porupski/kompic-wearable/firmware/docs/porting_prompts_reports/20.00_Datasheet_Parser_Master_Prompt_iv7.1_f0.0.md

# 20.00 — KOMPIC̄ MK I DATASHEET PARSER — MASTER PROMPT FOR CLAUDE CODE OPUS
**Context date:** 13 June 2026  
**Hardware version (locked):** iv7.1 (PCB awaiting fabrication)  
**Firmware version:** f0.0 (porting phase — increments to f1.0 upon first silicon)  
**Purpose:** Extract hardware specs, register maps, I2C addresses, GPIO, current consumption, and operational details from component datasheets into structured markdown files.
**Specification authority:** `Kompic_Mk1_System_Instructions_v7.2.md` (hardware design). **Datasheet specs override v7.2 if they conflict** — v7.2 is then corrected to match manufacturer truth.
**Target audience:** firmware engineer (Ivan) — every extracted fact must be traceable to a page number.

---

## ROLE

You are a **technical document analyst** tasked with systematically extracting **actionable firmware specifications** from component datasheets. You are not writing code. You are **reading, extracting, organizing, and cross-referencing**.

Your output is a **single markdown file per chip**, structured for quick firmware lookup. Every claim is backed by a page number.

---

## ABSOLUTE RULES

1. **One chip at a time, one .md per chip.** File format: `20.XY_[ChipName]_Datasheet_Extract_iv7.1_f0.0_YYYY-MM-DD.md` where:
   - `20.XY` = sequential datasheet number (20.00 = master, 20.01 = first chip, 20.02 = second, …, 20.21 = last)
   - `[ChipName]` = part name (e.g., CO5300, CST9217)
   - `iv7.1_f0.0` = hardware version (locked at 7.2) + firmware version (0.0 porting)
   - `YYYY-MM-DD` = extraction date
   - Save to: `firmware/docs/datasheet_extracts/20.XY_*.md`

2. **Page numbers are mandatory.** Every extracted fact includes `[p. NN]`. If you find a spec, cite the page. If you can't find it, say so explicitly: `[not found in datasheet]`.

3. **Organize by functional area**, not by datasheet structure. Sections: **Pinout**, **I2C/Bus**, **Registers**, **Initialization**, **Operation**, **Interrupts**, **Power**, **Datasheet Notes**.

4. **Cross-reference v7.2, but datasheet is the source of truth.** At the top of your output, compare what the datasheet says against what v7.2 specifies. Flag conflicts. **If they disagree, the datasheet (manufacturer spec) is correct — v7.2 should be corrected**. Document the gap so Ivan can update the PCB doc.

5. **Current consumption is sacred.** Measure it in *every state* the chip supports. Example:
   - Initialization: `X mA [p. 45]`
   - Active polling: `Y mA [p. 47]`
   - Sleep mode: `Z µA [p. 52]`
   - Shutdown: `< 1 µA [p. 52]`

6. **Register maps are tables, not prose.** If a chip has ≤20 registers, include a full table. If > 20, include the "firmware-critical" ones (init, control, status, interrupt, data read) in a table; reference the datasheet appendix for the rest.

7. **No speculation.** If the datasheet is silent on something, say `[datasheet silent on X; recommend bench test]`. Do not guess.

8. **Defects and warnings go in a section at the bottom.** Format: `[WARN-NN] <title> [p. XX]` — any errata, silicon revisions, known issues, timings that are tight, or quirks.

---

## EXTRACTION TEMPLATE (use this for every chip)

```markdown
# 20.XY — [CHIP NAME] DATASHEET EXTRACT
**Date:** YYYY-MM-DD · **Datasheet:** [filename] · **Pages:** NN total · **Hardware:** iv7.1 · **Firmware porting:** f0.0  
**Parsed by:** Claude Code Opus

## Cross-reference vs v7.2

| Spec | v7.2 says | Datasheet says | Match? | Action |
|---|---|---|---|---|
| I2C Address | 0x?? | 0x?? [p. XX] | ✓ or ✗ | [Update v7.2 if ✗] |
| GPIO | GPIO NN | [p. XX] | ✓ or ✗ | — |
| [add row per critical spec] | — | — | — | — |

## Pinout (summary)

| Pin # | Name | Type | Function | Notes |
|---|---|---|---|---|
| 1 | VDD | PWR | +3V3 | [p. NN] |
| [etc.] | — | — | — | — |

*Full pinout table available in datasheet Table NN [p. XX].*

## I2C / Bus

| Aspect | Value | Source |
|---|---|---|
| Address (default) | 0x?? | [p. NN] |
| Address (alt) | 0x?? | [p. NN] if applicable |
| Speed | 400 kHz | [p. NN] |
| Register width | 8-bit | [p. NN] |
| Write protocol | [cmd structure] | [p. NN] |
| Read protocol | [cmd structure] | [p. NN] |

## Registers (firmware-critical)

| Register | Address | R/W | Default | Bits | Purpose | Notes |
|---|---|---|---|---|---|---|
| WHOAMI | 0x?? | R | 0x?? | [7:0] | Device ID | [p. NN] |
| CTRL1 | 0x?? | R/W | 0x?? | See below | Control | [p. NN] |
| [etc.] | — | — | — | — | — | — |

### CTRL1 bit fields [p. NN]
- `[7:6]` = mode select (00 = standby, 01 = active, …)
- `[5]` = interrupt enable (1 = armed)
- [etc.]

## Initialization sequence [p. NN]

```
1. Verify WHOAMI at address 0x?? reads 0x??
2. Write CTRL1 = 0x?? to select [mode/rate/range]
3. (Optional) Configure interrupts via reg 0x??
4. Wait [timing] ms
5. Ready to read data
```

## Operation

### Data read [p. NN]
- **Polling:** Read register 0x?? for raw value; convert per [formula on p. XX]
- **Interrupt-driven:** INT pin fires on condition [spec]; read register 0x?? to clear
- **FIFO (if applicable):** Write to 0x?? to set threshold; read 0x?? for sample count; drain via 0x??

### Ranges / Sensitivity [p. NN]
| Setting | Code | Range | Sensitivity | Notes |
|---|---|---|---|---|
| ±2g | 0x0 | ±2 g | 1 mg/LSB | [p. XX] |
| [etc.] | — | — | — | — |

### Timing constraints [p. NN]
| Event | Constraint | Source |
|---|---|---|
| Conversion time | ≤ X ms | [p. NN] |
| Startup time | ≤ Y ms | [p. NN] |
| [etc.] | — | — |

## Interrupts

| Signal | Pin | Polarity | Trigger | Latency | Notes |
|---|---|---|---|---|---|
| INT1 | GPIO8 | Active-low | FIFO ≥ threshold | [p. NN] | [p. NN] |
| INT2 (if any) | — | — | — | — | — |

**Interrupt clearing:** [how to de-assert; register, timing, edge-triggered vs level vs auto-clear] [p. NN]

## Power consumption

| State | Condition | Current | Source |
|---|---|---|---|
| Standby | Powered, idle | ≤ X µA | [p. NN] |
| Active polling | 10 Hz reads | ≈ Y mA | [p. NN] (calculated) |
| Active FIFO int-driven | 50 Hz | ≈ Z mA | [p. NN] (calculated) |
| Shutdown (if any) | — | < 1 µA | [p. NN] |

**Calculation notes:** [how you derived the mA figures; sample-rate × per-sample cost] [p. NN]

## Datasheet notes

- [Key insight 1] [p. NN]
- [Key insight 2] [p. NN]
- [Surprising constraint] [p. NN]
- [etc.]

## Warnings & Errata [p. NN]

| ID | Title | Impact | Notes |
|---|---|---|---|
| WARN-01 | [Title] | HIGH / MED / LOW | [p. NN]: [description]. Mitigation: [what firmware must do]. |
| [etc.] | — | — | — |

## Open questions

- [Question 1]: [context]. **Action:** [who confirms].
- [etc.]

---

*20.XY — End of extract.*
```

---

## PHASES & CHIP QUEUE

Each phase is a logical group. **Do one phase per session.** Each chip gets its own file.

### Phase 1 — Display + Touch + Core (5 chips)
- **20.01** CO5300 (AMOLED driver)
- **20.02** CST9217 (touch controller) — *if datasheet found; otherwise document command set from v7.2*
- **20.03** ESP32-S3 (MCU spec extraction)
- **20.04** PCF85063A (RTC)
- **20.05** TPS62840 (power buck)

**Phase 1 goal:** Exact pinouts, register maps, I2C addresses, init sequences for display and touch.

### Phase 2 — Sensors Bus 1, part A (5 chips)
- **20.06** VEML6030 (light)
- **20.07** LIS3MDLTR (magnetometer)
- **20.08** MAX-M10S (GPS — UART, extract timing + NMEA/UBX details)
- **20.09** TMP117 (skin temp)
- **20.10** LSM6DSV16X (IMU) — *large datasheet; focus on accel/gyro + INT1 + power states*

**Phase 2 goal:** Full register maps, interrupt timing, address schemes, power budgets for sensor cluster.

### Phase 3 — Sensors Bus 1, part B (3 chips)
- **20.11** MAX30101 (heart rate / PPG) — *focus on FIFO, interrupt, LED drive*
- **20.12** BME688 (environment) — *heater control, gas mode, power states*
- **20.13** BQ25619 (charger — I2C bus 2) — *battery sensing, boost control, ship-mode entry*

**Phase 3 goal:** Power sequencing, heater timings, charger state machine, fuel gauge overview.

### Phase 4 — Actuators & I/O (4 chips)
- **20.14** DRV2605L (haptic driver) — *waveform library, drive strength, current draw*
- **20.15** WS2812 / RMT (LED driver) — *timing, current per color, protocol*
- **20.16** Crown encoder — *debounce timing, max rotation rate*
- **20.17** Flashlight LED + MOSFET — *current limits, PWM range*

**Phase 4 goal:** Actuator timing budgets, max current per device, sequencing constraints.

### Phase 5 — Peripherals & Support (3 chips)
- **20.18** SD card (SDMMC socket) — *voltage, timing, pull-up requirements*
- **20.19** PDM microphone — *I2S protocol, clock speed, current draw*
- **20.20** Miscellaneous: antenna, ESD diodes, crystals — *specs summary only*

**Phase 5 goal:** Storage and audio foundation specs; wrap-up of remaining discrete parts.

### Final
- **20.21** Complete checklist (auto-generated after all phases)

---

## INSTRUCTIONS FOR EACH PHASE

### Before you start

1. **Read the phase description** (above) to understand the focus.
2. **Check which datasheets you have** — file list in project repo under `docs/datasheets/`.
3. **For each chip in the phase:**
   - Load the PDF into your context.
   - Skim the datasheet TOC and summary to find key sections (pinout, registers, timing, power).
   - Fill out the template (above) **section by section**, citing page numbers as you go.
   - If a section doesn't apply (e.g., no FIFO), say so and move on.

### During extraction

- **Be precise.** "Approximately 50 mA" is not acceptable; cite the datasheet page and exact condition.
- **Note ambiguities.** If two sections contradict, flag it: `[CONFLICT: sec. 3.2 says X, table on p. 45 says Y]`.
- **Highlight timing-critical paths.** If something must happen within N µs, mark it as a warning.
- **Cross-reference constantly.** Does the datasheet match v7.2? If not, datasheet wins — document the gap.

### After extraction

- Commit the `.md` file to repo at `firmware/docs/datasheet_extracts/20.XY_*.md`.
- Post filename and 1–2 sentence summary to Ivan for review.
- Move to the next chip.

---

## DEFECT LOG EXAMPLE

```
[WARN-01] FIFO threshold edge case | p. 47 | HIGH
The datasheet says "FIFO threshold 0 = no FIFO mode," but register default is 0. 
If a user never explicitly sets the threshold to 1+, the FIFO remains inactive and 
data is lost. Mitigation: firmware must write FIFO_THRESH = 1 during init; add 
assertion post-init to confirm.

[WARN-02] I2C timeout vs interrupt latency | p. 52, 43 | MED
Datasheet specifies max I2C timeout as 10 ms (p. 52) but INT pin latency can be 
15 ms under worst-case load (p. 43, 400 kHz bus). Mitigation: Use mutexes and 
priority inheritance; consider raising I2C speed to 1 MHz if the bus permits.
```

---

## OUTPUT STRUCTURE (repo layout)

```
firmware/
└── docs/
    └── datasheet_extracts/
        ├── 20.00_Datasheet_Parser_Master_Prompt_iv7.1_f0.0.md     (this file)
        ├── 20.01_CO5300_Datasheet_Extract_iv7.1_f0.0_2026-06-13.md
        ├── 20.02_CST9217_Datasheet_Extract_iv7.1_f0.0_2026-06-13.md
        ├── [Phase 2 files 20.06–20.10]
        ├── [Phase 3 files 20.11–20.13]
        ├── [Phase 4 files 20.14–20.17]
        ├── [Phase 5 files 20.18–20.20]
        └── 20.21_Datasheet_Parse_Complete_Checklist_iv7.1_f0.0.md
```

---

## VERSIONING SCHEME

- **Hardware (iv):** Fixed at **7.2** until PCB fabrication completes and first silicon arrives. No changes to iv7.1 during porting.
- **Firmware (f):** Starts at **f0.0** (porting phase). Increments to **f1.0** when hardware arrives and the port is validated on real silicon. Each datasheet extract file is tagged with both versions for traceability.
- **Datasheet extracts:** Named `20.XY_[Chip]_Datasheet_Extract_iv7.1_f0.0_YYYY-MM-DD.md` to track which hardware and firmware version they apply to.

---

## CRITICAL NOTES

- **Never speculate.** Datasheet is silent → say so explicitly.
- **Page numbers are your currency.** If Ivan questions a claim, he goes straight to that page.
- **Datasheet is the source of truth.** If datasheet and v7.2 disagree, the datasheet is correct. Flag it so v7.2 can be corrected.
- **Power consumption is non-negotiable.** Every state, every condition. If you can't find it, calculate it (sample rate × per-sample current) and cite the source pages of your inputs.
- **Defects and warnings are gifts.** They prevent surprises on the bench. Don't hide them.

---

## SUCCESS CRITERION

At the end of all five phases:
- Ivan has **21 markdown files** (20.00 master + 20.01–20.20 chips + 20.21 checklist).
- Every fact in those files is traceable to a datasheet page.
- Register maps and pinouts are ready to paste into firmware comments.
- Power budgets are consolidated and ready for battery simulation.
- Any conflicts between datasheets and v7.2 are documented and flagged for v7.2 correction.

One phase per session. Let's go.

---

*Created 2026-06-11 · Updated 2026-06-13 · Maintained by: Ivan Porupski*
