porupski/kompic-wearable/firmware/docs/porting_prompts_reports/20.14-20.17_KICKOFF_PHASE4_Actuators_IO.md

# 20.14–20.17 KICKOFF — PHASE 4: ACTUATORS & I/O
**Date:** 13 June 2026  
**Hardware version:** iv7.1 (locked)  
**Firmware version:** f0.0 (porting)  
**Target chips:**
- **20.14** DRV2605L (haptic driver)
- **20.15** WS2812B (RGB LED, RMT protocol)
- **20.16** Crown encoder (mechanical specs)
- **20.17** Flashlight LED + MOSFET gate

**Effort estimate:** 1 session (3–4 hours)

---

## PHASE 4 GOAL

Extract **actuator and I/O driver specifications** — protocol timings, current limits, and sequencing constraints. Focus on haptic waveforms, LED color transitions, current per device, 5V boost rail arbitration.

---

## WHAT YOU'LL PARSE

### 20.14 — DRV2605L Haptic Driver
- I2C address (0x5A on **Bus 2** per v7.2)
- Register map (MODE, GO, WAVESEQ, FEEDBACK_CTRL, STATUS)
- Waveform library (click, buzz, alert; amplitude, duration)
- Drive strength control (voltage output range)
- Mode select (internal trigger, PWM, I2C)
- Current consumption (idle, active waveform, sweep)
- ERM vs. LRA (datasheet assumes ERM; confirm compatibility with ELV1411A LRA)
- Thermal limits

### 20.15 — WS2812B RGB LED (RMT Protocol)
- Protocol (1-wire timing; 0 vs. 1 bit encoding)
- Color format (GRB order? RGB order?)
- Update rate (refresh constraint)
- Power consumption (per color, per LED)
- RMT peripheral requirements (GPIO42, timing accuracy)
- Current limits (max per LED; 5V rail constraint)

### 20.16 — Crown Encoder
- Contact bounce time (typical debounce window)
- A/B quadrature phase relationship
- Maximum rotation rate (RPM → Hz conversion)
- Electrical specs (contact resistance, voltage limits)
- PCNT peripheral for debounce-free counting

### 20.17 — Flashlight LED + Gate MOSFET
**LED specs:**
- Forward voltage (3.2V typical for white)
- Maximum forward current
- Power dissipation (@rated current, de-rated with temperature)

**MOSFET (BSS138W):**
- Gate threshold voltage (Vgs(th))
- Rds(on) at 3.3V gate
- Maximum drain current (continuous)
- Thermal resistance (θja)

---

## 5V BOOST ARBITRATION SUMMARY

Add a section comparing all 5V consumers:
- **MAX30101 LEDs:** ~200 mA during active HR measurement
- **WS2812:** ~60 mA max (all white at full brightness)
- **Flashlight:** ~200–500 mA depending on brightness
- **BQ25619 boost capacity:** 1A total
- **Conflict:** If all three demand 5V simultaneously, boost can't supply. Firmware must sequence or limit.

---

## EXTRACTION CHECKLIST

- [ ] Protocol or electrical specs extracted
- [ ] Current draw (all modes, all brightness levels for LED/flashlight)
- [ ] Timing constraints (debounce, settling, update rate)
- [ ] Power limits (max continuous current, thermal limits)
- [ ] Warnings (contact bounce, current surges, thermal throttling)
- [ ] Page numbers on every claim

---

## OUTPUT FILENAMES

- `20.14_DRV2605L_Datasheet_Extract_iv7.1_f0.0_2026-06-13.md`
- `20.15_WS2812_Datasheet_Extract_iv7.1_f0.0_2026-06-13.md`
- `20.16_Encoder_Datasheet_Extract_iv7.1_f0.0_2026-06-13.md`
- `20.17_Flashlight_LED_MOSFET_Extract_iv7.1_f0.0_2026-06-13.md`

---

## SUCCESS FOR PHASE 4

By the end:
- Four .md files, each ≤ 6 pages
- 5V rail budget clearly defined
- Haptic waveform library enumerated
- Encoder debounce time confirmed
- Current arbitration strategy outlined

**Next phase:** Peripherals (files 20.18–20.20); SD, mic, miscellaneous.

---

*Created 2026-06-11 · Updated 2026-06-13 · Maintained by: Ivan Porupski*
