porupski/kompic-wearable/firmware/docs/porting_prompts_reports/20.18-20.20_KICKOFF_PHASE5_Peripherals_Misc.md

# 20.18–20.20 KICKOFF — PHASE 5: PERIPHERALS & MISC
**Date:** 13 June 2026  
**Hardware version:** iv7.1 (locked)  
**Firmware version:** f0.0 (porting)  
**Target chips:**
- **20.18** SD card (SDMMC interface)
- **20.19** PDM microphone (I2S protocol)
- **20.20** Miscellaneous (antenna, ESD diodes, crystals)

**Final deliverable:**
- **20.21** Datasheet Parse Complete Checklist

**Effort estimate:** 1 session (2–3 hours)

---

## PHASE 5 GOAL

Close out the datasheet extraction with **peripherals and miscellaneous** components. These have lower firmware criticality but are essential for correctness: storage (SD), audio input (PDM mic), RF (antennas), and protection (ESD diodes, crystal specs).

By the end of Phase 5, every datasheet is parsed, all extracted specs are organized, and the firmware team has a complete hardware reference library.

---

## WHAT YOU'LL PARSE

### 20.18 — SD Card (SDMMC Interface)
**File:** Generic SDMMC connector spec or LCSC reference  
**Focus:**
- Electrical specs (voltage, current limits)
- Timing constraints (setup/hold for GPIO38/39/40)
- Pull-up requirements (v7.2 says 10kΩ typical)
- Card detection (CD pin polarity if used; v7.2 says "verify on bench")
- Hot-swap safe (can ESP32 handle card removal during operation?)
- Speed grades (SD High-Speed, SDXC)

### 20.19 — PDM Microphone
**File:** Generic PDM MEMS spec or LCSC reference  
**Focus:**
- I2S protocol (CLK on GPIO47, DATA on GPIO48 per v7.2)
- Clock frequency (typical 1–4 MHz)
- Sampling rates supported (16, 32, 48 kHz typical)
- Bit depth (output resolution)
- Sensitivity (dBV/Pa or similar)
- Signal-to-noise ratio (SNR)
- Frequency response (20 Hz–20 kHz)
- Power consumption (active, standby)
- Acoustic overload point (SPL limit)

### 20.20 — Miscellaneous (Reference Specs Only)
**Collated specs for:**
- **BLE antenna (Johanson 2450AT18A):** Impedance, gain, pattern, tuning network values (per v7.2)
- **GPS antenna (ceramic patch):** Frequency (L1 1.575 GHz), gain, impedance
- **RTC crystal (32.768 kHz):** Load capacitance, ESR, tolerance, temperature range
- **ESD diode arrays (ESDALCL5, TPD2E001):** Clamping voltage, leakage current, response time
- **Schottky diodes (1N4148):** Forward voltage, leakage, reverse recovery time (for GPS/RTC backup isolation)

---

## EXTRACTION CHECKLIST

- [ ] Electrical specs (voltage, current, impedance)
- [ ] Timing constraints (if protocol-based)
- [ ] Interface pins and signal names
- [ ] Power consumption (if applicable)
- [ ] Warnings or known issues
- [ ] Page numbers on every claim

---

## OUTPUT FILENAMES (Phase 5 extracts)

- `20.18_SDCard_SDMMC_Extract_iv7.1_f0.0_2026-06-13.md`
- `20.19_PDM_Microphone_Extract_iv7.1_f0.0_2026-06-13.md`
- `20.20_Miscellaneous_Passives_Reference_iv7.1_f0.0_2026-06-13.md`

---

## FINAL CHECKLIST — ALL PHASES COMPLETE

**File:** `20.21_Datasheet_Parse_Complete_Checklist_iv7.1_f0.0_2026-06-13.md`

After Phase 5, create a summary file:

| # | Chip | File | Status | Notes |
|---|---|---|---|---|
| 20.01 | CO5300 | 20.01_CO5300_... | ✓ | Display pipeline, QSPI, sleep/wake |
| 20.02 | CST9217 | 20.02_CST9217_... | ✓ or [fallback] | Touch protocol (v7.2 if no datasheet) |
| 20.03 | ESP32-S3 | 20.03_ESP32-S3_... | ✓ | GPIO, I2C, SPI, sleep, boot straps |
| 20.04 | PCF85063A | 20.04_PCF85063A_... | ✓ | RTC, time/date, alarms, backup |
| 20.05 | TPS62840 | 20.05_TPS62840_... | ✓ | 3.2V buck, soft-start, efficiency |
| 20.06 | VEML6030 | 20.06_VEML6030_... | ✓ | Light sensor, auto-ranging |
| 20.07 | LIS3MDLTR | 20.07_LIS3MDLTR_... | ✓ | Magnetometer, hard-iron cal, LRA offset |
| 20.08 | MAX-M10S | 20.08_MAX-M10S_... | ✓ | GPS, NMEA/UBX, 1PPS, time-before-fix |
| 20.09 | TMP117 | 20.09_TMP117_... | ✓ | Skin temperature, precision, thresholds |
| 20.10 | LSM6DSV16X | 20.10_LSM6DSV16X_... | ✓ | IMU, accel/gyro, INT1, raise-to-wake |
| 20.11 | MAX30101 | 20.11_MAX30101_... | ✓ | Heart rate, PPG, FIFO, INT, LEDs |
| 20.12 | BME688 | 20.12_BME688_... | ✓ | Environment, gas heater, bus contention |
| 20.13 | BQ25619 | 20.13_BQ25619_... | ✓ | Charger, fuel gauge, boost, ship-mode |
| 20.14 | DRV2605L | 20.14_DRV2605L_... | ✓ | Haptics, waveforms, I2C bus 2 |
| 20.15 | WS2812 | 20.15_WS2812_... | ✓ | Status LED, RMT protocol, color |
| 20.16 | Encoder | 20.16_Encoder_... | ✓ | Crown input, debounce, PCNT |
| 20.17 | Flashlight | 20.17_Flashlight_... | ✓ | LED, MOSFET gate, PWM brightness |
| 20.18 | SD Card | 20.18_SDCard_... | ✓ | SDMMC interface, mount on demand |
| 20.19 | PDM Mic | 20.19_PDM_Mic_... | ✓ | I2S, audio capture, SNR |
| 20.20 | Miscellaneous | 20.20_Miscellaneous_... | ✓ | Antenna, crystals, ESD diodes |

---

## CONSOLIDATION TASKS FOR 20.21

In the final checklist, also include:
- **Total power budget** (sum of all sensors at typical duty cycle)
- **I2C bus utilization** (Bus 1 vs. Bus 2 worst-case load)
- **5V boost rail consumer list** (total max draw vs. 1A capacity)
- **RTC GPIO wake sources** (GPIO 6, 7, 8, 15, 16, 21 confirmed)
- **Cross-v7.2 conflicts** (any specs where datasheet overrides v7.2, list them for doc correction)

---

## SUCCESS FOR PHASE 5 (AND FINAL COMPLETION)

By the end:
- 21 datasheet extract .md files checked into `firmware/docs/datasheet_extracts/`
- Each file ≤ 8 pages, traceable to source pages
- Cross-references to v7.2 complete (conflicts flagged for doc correction)
- Power budgets consolidated (input for battery simulation)
- Register maps ready to paste into firmware comments
- Defects and warnings enumerated (input for firmware design)
- Final checklist confirms all specs captured

**Total time:** ~5 sessions (1 per phase) ≈ 25–30 hours focused extraction.

**Output:** A complete hardware reference library, organized and indexed for the firmware team.

---

*Created 2026-06-11 · Updated 2026-06-13 · Maintained by: Ivan Porupski*
