porupski/kompic-wearable/firmware/docs/datasheet_extracts/20.18_SDCard_SDMMC_Extract_iv7.1_f0.0_2026-06-19.md

# 20.18 — SD CARD / SDMMC SOCKET DATASHEET EXTRACT
**Date:** 2026-06-19 · **Datasheet:** SDMMC Socket LCSC.pdf (Shenzhen Shouhan Technology, "TF PUSH", Rev. A/0, 8 pp.) · **Hardware:** iv7.1 · **Firmware porting:** f0.0
**Parsed by:** Claude Code Sonnet 4.6

---

## Cross-reference vs v7.2

| Topic | iv7.1 / v7.2 assumption | Datasheet finding | Action required |
|---|---|---|---|
| Supply voltage | 3.2V TPS62840 rail | Datasheet silent on VDD spec; passive connector. | Confirmed compatible — 3.2V within SD spec 2.7–3.6V tolerance [SD spec] |
| Card detect (CD) pin | Present; polarity "verify on bench" | Pin 2 = CD/DAT3 (shared). Separate dedicated CD switch pin visible in mechanical drawing ("Cd"). Polarity NOT stated. | MUST verify on bench — polarity unresolved |
| 1-bit SDMMC mode | Only DAT0 connected (GPIO40) | Socket has all 8 signal pins. Physically supports 4-bit. 1-bit is a firmware/GPIO choice, not a socket limitation. | No action — socket capable; 1-bit chosen by design |
| Pull-ups on SD lines | 10 kΩ typical (v7.2) | Datasheet silent on pull-up values | Consistent with SD spec [SD spec] |
| Insertion cycles | Not stated in v7.2 | 5000 cycles rated [p. 5, Table I item 5] | No conflict |
| Contact resistance | Not stated in v7.2 | 40 mΩ max initial; 100 mΩ max after 5000 cycles [p. 5, Table I] | Acceptable |
| Operating temperature | Not stated | −25°C to +85°C storage; −55°C to +85°C thermal shock rated [p. 6, p. 8, Table I] | Within wearable range |

---

## Connector mechanical specs

| Parameter | Value | Source |
|---|---|---|
| Product type | MicroSD (TF) push-push (push-in / push-out eject) | [p. 1] |
| Total signal contacts | 8 (DAT0–DAT3, CMD, CLK, VDD, VSS) | [p. 1, pin table] |
| Card detect contact | 1 separate CD pin ("Cd" in PCB layout) | [p. 1, drawing] |
| Total pins inc. CD | 9 electrical contacts | [p. 1] |
| Contact pitch | 1.10 mm; total 8-contact span 8.80 mm | [p. 1, PCB layout] |
| Overall body width | 14.75 mm | [p. 1] |
| Overall body height above PCB | ~3.40 mm | [p. 1, side view] |
| Eject travel | ~0.92 mm push-out stroke | [p. 1] |
| PCB mounting hole diameter | 2 × ⌀0.80 mm (±0.10) | [p. 1] |
| PCB mounting hole pitch | 8.00 mm centre-to-centre | [p. 1] |
| Mounting type | SMT pads + 2 through-hole anchor posts | [p. 1] |
| Multimedia card compatible | Yes | [p. 1, Notes item 3] |
| Housing material | High-temp thermoplastic, UL94V-0 | [p. 1, Notes item 1] |
| Contact plating | Gold over Nickel (contact area); Tin over Nickel (solder area) | [p. 1, Notes item 2] |
| RoHS | Yes | [p. 2, §3.3] |

**Pin table** [p. 1]: Pin 1=DAT2, Pin 2=CD/DAT3, Pin 3=CMD, Pin 4=VDD, Pin 5=CLK, Pin 6=VSS, Pin 7=DAT0, Pin 8=DAT1.

---

## Electrical characteristics

| Parameter | Value | Conditions | Source |
|---|---|---|---|
| Contact resistance (initial) | 40 mΩ max | 10 mA, 20 mV OC; MIL-STD-202F | [p. 5, Table I item 2] |
| Contact resistance (after 5000 cycles) | 100 mΩ max | Post-durability | [p. 5, Table I item 5] |
| Contact resistance (after thermal shock) | 100 mΩ max | −55°C to +85°C, 5 cycles | [p. 6, Table I item 9] |
| Contact resistance (after humidity) | 100 mΩ max | 40°C, 90–95% RH, 96 h | [p. 6, Table I item 10] |
| Insulation resistance (initial) | 1000 MΩ min | 500 V DC ±10% | [p. 5, Table I item 3] |
| Insulation resistance (after humidity) | 100 MΩ min | Post-humidity | [p. 6, Table I item 10] |
| Dielectric strength | 500 V AC, 1 min | Leakage ≤ 1.0 mA | [p. 5, Table I item 4] |
| Rated current per contact | 0.3 A | Temp rise ≤30°C; UL498 | [p. 5, Table I item 6] |
| Insertion cycles | 5000 | Contact resistance ≤100 mΩ post-test | [p. 5, Table I item 5] |
| Vibration | No discontinuity >1 µs | 10–55 Hz, 1.5 mm, 2 h/axis; MIL-STD-202 Method 201 | [p. 5, Table I item 7] |
| Shock | No discontinuity >1 µs | 490 m/s², 3 axes; MIL-STD-202 Method 213 | [p. 5, Table I item 8] |
| Operating temperature | −25°C to +85°C | Storage; thermal shock rated to −55°C | [p. 3, §3.8; p. 6] |
| Contact capacitance | Not stated | — | [not found in datasheet] |

---

## Card Detect (CD) pin

**Physical presence:** Yes — dedicated "Cd" pin in PCB layout, separate from the 8 signal contacts. Pin 2 is dual-function CD/DAT3. [p. 1, drawing]

**Active polarity when card inserted:** **NOT stated in this datasheet.** No logic level, pull direction, or switch type described.

**Convention (unverified):** Most push-push TF sockets use a normally-closed switch that opens when a card is inserted (Cd goes HIGH with pull-up when absent, LOW when inserted). This is an unconfirmed assumption for this specific part — **bench verification is mandatory before writing card-detect firmware.**

**Firmware impact:** In iv7.1, SD_Cd is listed as "test pad only" (not on a GPIO). Hot-swap detection is therefore not implemented. This is acceptable for v1 if the card is treated as fixed storage during operation.

---

## SDMMC protocol context (1-bit mode)

### Why 1-bit was chosen
GPIO budget is exhausted. Only GPIO38 (CLK), GPIO39 (CMD), GPIO40 (DAT0) are available. DAT1–DAT3 not assigned. 4-bit mode is physically impossible without a hardware spin. The socket supports 4-bit mechanically. [iv7.1 pinout; p. 1 pin table]

### Pull-up requirements [SD spec]

| Signal | Pull-up required | Recommended value | Kompic v7.2 | Status |
|---|---|---|---|---|
| SD_CLK (GPIO38) | Optional | 10–100 kΩ | 10 kΩ | Consistent |
| SD_CMD (GPIO39) | Mandatory | 10–100 kΩ | 10 kΩ | Correct |
| SD_DAT0 (GPIO40) | Mandatory | 10–100 kΩ | 10 kΩ | Correct |
| SD_DAT1–DAT3 | Required if used | 10–100 kΩ | Not connected | Card has internal weak pull-ups on unused DAT lines in 1-bit mode |

Pull-ups must be to SD VDD rail (3.2V in Kompic).

### Maximum clock frequency (1-bit mode) [SD spec]

| Speed mode | Max clock | Bus width | Notes |
|---|---|---|---|
| Default Speed (DS) | 25 MHz | 1-bit or 4-bit | Mandatory baseline; all SD cards support |
| High Speed (HS) | 50 MHz | 1-bit or 4-bit | Requires CMD6 negotiation; most modern microSD support |
| UHS-I (SDR50/104/DDR50) | 100–208 MHz | 4-bit only | Not available in 1-bit mode |

**Practical limit for Kompic:** 50 MHz (HS 1-bit). Note: 10 kΩ pull-up × ~20 pF line capacitance → RC ≈ 200 ns — too slow for 50 MHz HS recovery. See WARN-02.

### Initialization sequence (1-bit SDMMC, ESP-IDF) [SD spec / ESP-IDF]

```
1. Apply VDD; CMD and DAT0 held high by pull-ups.
2. Wait ≥1 ms for card power-up.
3. Send ≥74 clock cycles with CMD high (card initialization clocks).
4. CMD0 (GO_IDLE_STATE) — reset card.
5. CMD8 (SEND_IF_COND) — detect SD v2.0+ vs legacy.
6. ACMD41 (SD_SEND_OP_COND) — repeat until card not busy.
7. CMD2 (ALL_SEND_CID), CMD3 (SEND_RELATIVE_ADDR) — get RCA.
8. CMD7 (SELECT_CARD) — transition to Transfer state.
9. ACMD6 (SET_BUS_WIDTH) with arg 0b00 — FORCE 1-bit mode.
   DO NOT send 0b10 (4-bit) — DAT1–DAT3 not wired.
10. (Optional) CMD6 (SWITCH_FUNC) — negotiate High Speed 50 MHz.

ESP-IDF: set sdmmc_slot_config_t.width = 1 and
SDMMC_HOST_FLAG_1BIT to enforce 1-bit throughout.
```

### Hot-swap safety
Push-push mechanism allows physical removal at any time. Card removal during active I/O corrupts the filesystem (FAT/FAT32 has no journaling). Firmware must either unmount before removal or detect the CD transition and flush/unmount cleanly. With CD currently on a test pad (no GPIO), hot-swap safety is by user convention only: do not remove the card while the device is logging. [SD spec / ESP-IDF]

---

## Power consumption

| Item | Value | Notes |
|---|---|---|
| Connector idle | 0 mW (passive) | No active electronics |
| Pull-up quiescent (CMD + DAT0) | ~0.64 mA | 2 × (3.2V / 10kΩ); lines high at idle |
| Pull-up quiescent (+ CLK, if populated) | ~0.96 mA | 3 × 10kΩ pull-ups |
| SD card active | 20–100 mA | Card-dependent [SD spec] |
| SD card idle (STANDBY state) | 0.5–2 mA | Card-dependent [SD spec] |
| SD card sleep | ~0.1 mA | After CMD5 or power-cycle [SD spec] |
| Contact current rating | 0.3 A max per contact | Temp rise ≤30°C [p. 5, Table I item 6] |

---

## Datasheet notes

- [p. 1] Multimedia card (MMC) compatible — connector accepts both microSD and MMC form factors.
- [p. 3, §3.8] Storage: −25°C to +85°C, ≤80% RH, non-corrosive. Re-qualify after >6 months storage.
- [p. 5, Table I item 5] 5000 insertion cycles — adequate for personal device (daily swap = 13+ years).
- [p. 5, Table I item 6] 0.3 A per contact rated — SD card current peaks well below this; no thermal concern.
- [p. 5–6, Table I items 7–8] Vibration/shock: MIL-STD-202, 490 m/s² — robust for a wrist-worn device.
- [p. 8, Table III] Pb-free reflow: peak 255°C, max 60 s above 217°C. Compatible with JLCPCB Pb-free profile.
- [p. 2, §1] Product described as "T-FLASH 外焊" (TF card, external anchor solder style).
- [p. 2, §2] Test references: MIL-STD-1344A, MIL-STD-202F, EIA364, IEC-512-3.

---

## Warnings & Errata

| ID | Title | Impact | Notes |
|---|---|---|---|
| W-01 | CD pin polarity undetermined | MEDIUM | Datasheet gives no information on CD switch logic level. Open Issue #4 in iv7.1 remains unresolved. Do not write card-detect firmware until bench-confirmed. |
| W-02 | 10 kΩ pull-ups too slow for 50 MHz HS mode | HIGH | 10 kΩ × ~20 pF ≈ 200 ns RC — far too slow for 50 MHz CMD recovery. Use Default Speed (25 MHz) with 10 kΩ, or reduce pull-ups to 4.7 kΩ and verify signal integrity at 50 MHz with scope. |
| W-03 | DAT1–DAT3 not connected — must enforce 1-bit in driver | HIGH | If ESP-IDF SDMMC host is initialised without `width = 1`, it will attempt 4-bit via ACMD6 → bus corruption on unwired lines. Always set `sdmmc_slot_config_t.width = 1`. |
| W-04 | No GPIO for CD pin | LOW | CD is a test pad only. Hot-swap detection impossible without hardware change. Treat SD card as fixed storage during operation. |
| W-05 | Hand-soldering risk at 1.10 mm contact pitch | LOW-MED | Inspect under magnification for solder bridges. Gold-over-nickel contacts — do not overheat. |
| W-06 | Contact capacitance not specified | LOW | Datasheet silent. At 25 MHz DS this is unlikely to matter. At 50 MHz HS, verify empirically with scope. |
| W-07 | GPIO38–40 have no RTC wake capability | INFO | SD cannot wake ESP32-S3 from deep sleep — by design, consistent with iv7.1. |

---

## Open questions

1. **CD pin polarity** — LOW or HIGH when card inserted? Measure on bench with multimeter before writing card-detect logic. (iv7.1 Open Issue #4.)
2. **Contact capacitance** — Not in datasheet. Obtain from Shenzhen Shouhan or measure if 50 MHz HS mode is desired.
3. **Pull-up values for HS mode** — Reduce CMD/DAT0 pull-ups from 10 kΩ to 4.7 kΩ or 2.2 kΩ if 50 MHz HS is needed; verify with oscilloscope.
4. **LCSC part number** — Confirm BOM part number matches this drawing's PCB footprint (8.00 mm mounting hole pitch, 1.10 mm contact pitch) before ordering.
5. **Filesystem journaling** — FAT32 has no journaling; hot-swap corruption risk. Consider exFAT (ESP-IDF v5+) or a "safe to remove" UI indicator.
6. **4-bit upgrade path** — For Kompic Mk II with more GPIOs: route DAT1–DAT3 and this socket supports 4-bit 50 MHz (4× throughput). Worth routing in next spin if fast data logging is needed.

---

*20.18 — End of extract.*
