porupski/kompic-wearable/firmware/docs/datasheet_extracts/20.19_PDM_Microphone_Extract_iv7.1_f0.0_2026-06-19.md

# 20.19 — MSM261DGT003 PDM MICROPHONE DATASHEET EXTRACT
**Date:** 2026-06-19 · **Datasheet:** MSM261DGT003.pdf · **Hardware:** iv7.1 · **Firmware porting:** f0.0
**Parsed by:** Claude Code Sonnet 4.6

---

## Cross-reference vs v7.1

| Topic | iv7.1 assumption | Datasheet reality | Action required |
|---|---|---|---|
| Supply rail | "1.8V rail (MEMS mic VDD)" listed under +1V8 consumers | VDD range 1.6–3.6 V; test conditions at 1.8 V — **1.8V is correct and confirmed** | None — rail assignment confirmed |
| VDD rail label | System Instructions list mic under +1V8 | 1.8V is within 1.6–3.6V range; 1.8V is the datasheet reference condition | Confirmed: power from +1V8 rail |
| PDM protocol | PDM (not I2S) | Confirmed PDM digital output, fourth-order Σ-Δ modulator, ½-cycle PDM data format | Confirmed |
| L/R pin | "likely tied to GND" | JP9 default = GND (left channel = Mic(Low)); DATA asserts on CLK **falling** edge, latches on CLK **rising** edge | Confirmed: JP9 default GND = L channel; firmware/ESP32 must sample on rising edge |
| Mic_CLK GPIO | GPIO47 | CLK input to mic — no constraint from mic side beyond frequency range | Confirmed |
| Mic_Dout GPIO | GPIO48 | DATA output from mic | Confirmed |
| Operating temperature | Not stated in iv7.1 | Not explicitly stated in datasheet for operating range; storage −40 to +100°C; reliability bias tests to +105°C | Operating range not specified — see Open Questions |
| Decoupling | Not called out | 100 nF + 10 µF ceramic as close to VDD as possible [p. 12] | Add to bring-up checklist |

---

## Pinout (summary)

| PIN# | Function | Kompic iv7.1 connection |
|---|---|---|
| 1 | VDD | +1V8 rail |
| 2, 5 | GND | GND |
| 3 | DATA | GPIO48 (Mic_Dout) |
| 4 | CLK | GPIO47 (Mic_CLK) |
| 6 | L/R (SEL) | JP9 default = GND → left channel (Mic(Low)) |

Package is 6-pad LGA. Pins 2 and 5 are both GND; there is no separate pad for a separate power-good or enable — VDD is the only power input. The acoustic port (Ø0.65 mm) is top-ported (top face of the package). [p. 9]

---

## Interface / Protocol

**PDM confirmed — not I2S.** The MSM261DGT003 outputs a 1-bit pulse-density-modulated bitstream using a fourth-order Sigma-Delta (Σ-Δ) modulator. There are no I2S frame-sync (WS/LRCK) or I2S word-clock signals. The only two signal lines are:

- **CLK** — a clock input driven by the host (ESP32). The mic samples and modulates audio continuously at this clock rate.
- **DATA** — a 1-bit open-drain-like PDM output line. The bit density encodes instantaneous amplitude: higher density of 1s = higher sound pressure. Polarity: increasing sound = increasing density of 1s. [p. 3]

**Data format: ½ Cycle PDM.** The DATA line is driven for only one half of each clock cycle (the active half), and goes to High-Z for the other half. This allows two PDM microphones to share a single DATA line (stereo configuration) — one mic drives during the high half, the other during the low half. [p. 3, p. 7]

**L/R pin controls which half-cycle is active:**

| L/R pin | Mic name | Asserts DATA on | Latches DATA on |
|---|---|---|---|
| VDD | Mic(High) | CLK rising edge | CLK falling edge |
| GND | Mic(Low) | CLK falling edge | CLK rising edge |

**Kompic uses L/R = GND (JP9 default)** → Mic(Low) → DATA is asserted on CLK falling edge and the valid data bit is latched (read by host) on the CLK rising edge. [p. 7]

**How ESP32-S3 I2S-PDM-RX mode handles this:**
The ESP32-S3 I2S peripheral has a dedicated PDM RX mode (`I2S_COMM_FORMAT_STAND_PCM_SHORT` with PDM RX enabled via `i2s_pdm_rx_config_t`). In this mode:
- The I2S peripheral generates the CLK output on Mic_CLK (GPIO47) — there is no separate WS line.
- DATA is received on Mic_Dout (GPIO48).
- The peripheral integrates a decimation filter (CIC + IIR) that converts the incoming 1-bit PDM bitstream at the CLK frequency into multi-bit PCM samples at the target audio sample rate.
- The decimation ratio is: **decimation = f_CLK / (f_sample × 2)**. At f_CLK = 3.072 MHz and f_sample = 48 kHz, decimation = 32.
- For L/R = GND (Mic(Low)), the ESP32 PDM RX mode samples on the rising edge, which is correct.
- No MCLK or WS signals are needed or generated in PDM mode.

---

## Electrical characteristics

| Parameter | Symbol | Min | Typ | Max | Units | Conditions | Source |
|---|---|---|---|---|---|---|---|
| Supply voltage | VDD | 1.6 | — | 3.6 | V | — | [p. 3] |
| Absolute max supply | — | −0.3 | — | 4.0 | V | — | [p. 3] |
| Logic input high | VIH | 0.7×VDD | — | 3.6 | V | — | [p. 5] |
| Logic input low | VIL | −0.3 | — | 0.3×VDD | V | — | [p. 5] |
| Logic output high | VOH | VDD − 0.45 | — | — | V | IOUT = 2 mA | [p. 5] |
| Logic output low | VOL | — | — | 0.45 | V | IOUT = 2 mA | [p. 5] |
| Clock duty cycle | — | 40 | — | 60 | % | — | [p. 5] |
| Short circuit current | ISC | 1 | — | 10 | mA | DATA pin grounded | [p. 3] |
| Max output load | CLOAD | — | — | 200 | pF | — | [p. 3] |

**Note on logic levels at 1.8V VDD:**
- VIH min = 0.7 × 1.8 = 1.26 V
- VIL max = 0.3 × 1.8 = 0.54 V
- ESP32-S3 GPIO output high (3.3V domain on R8 per iv7.1) = ~3.0–3.3V → well above VIH. **Mismatch: mic VDD = 1.8V but CLK is driven from the 3.3V GPIO domain (GPIO47 is "3.3V domain on R8").** CLK input to the mic at 3.3V logic levels exceeds VIH max of 3.6V absolute — it is within the absolute maximum (3.6V), but VOH of a 3.3V GPIO can reach 3.3V which is above the mic's VDD. This warrants verification. See Warnings & Errata.

---

## Acoustic performance

| Parameter | Symbol | Min | Typ | Max | Units | Conditions | Source |
|---|---|---|---|---|---|---|---|
| Sensitivity | S | −27 | −26 | −25 | dBFS | 94 dB SPL @ 1 kHz; Standard mode, f_CLK=2.4 MHz | [p. 4] |
| Sensitivity | S | −26 | −25 | −24 | dBFS | 94 dB SPL @ 1 kHz; Low-Power mode, f_CLK=768 kHz | [p. 5] |
| Sensitivity matching | — | — | ±1 | — | dB | Between matched units | [p. 2] |
| SNR (A-weighted) | SNR | — | 64 | — | dB(A) | 20 kHz BW, A-weighted; f_CLK=2.4 MHz | [p. 4] |
| SNR (A-weighted) | SNR | — | 63 | — | dB(A) | A-weighted 20 Hz–8 kHz; f_CLK=768 kHz | [p. 5] |
| Acoustic overload point | AOP | — | 120 | — | dB SPL | 10% THD @ 1 kHz | [p. 4, p. 5] |
| Total harmonic distortion | THD | — | 0.1 | — | % | 94 dB SPL @ 1 kHz | [p. 4, p. 5] |
| PSRR | PSRR | — | 50 | — | dBV/FS | 200 mVpp sinewave @ 1 kHz | [p. 4, p. 5] |
| PSR+Noise | PSR+N | — | −80 | — | dBFS(A) | 100 mVpp square wave @ 217 Hz, A-weighted | [p. 4, p. 5] |
| DC output offset | — | — | 4 | — | % FS | Fullscale = ±100% FS | [p. 3] |
| Directivity | — | — | Omnidirectional | — | — | — | [p. 3] |

**Frequency response (from graph, p. 7):** The typical frequency response measured at 94 dB SPL shows the response is flat (within ~1 dB) from approximately **200 Hz to 5 kHz**, with a gradual roll-off below 200 Hz (low-frequency −3 dB point not explicitly tabulated — estimated from graph at approximately 100–150 Hz) and a slight rise (~1–2 dB) above 5 kHz up to the plotted 10 kHz limit. The datasheet does not provide explicit −3 dB frequency numbers in tabular form; the graph is the only reference. [p. 7]

---

## Timing

### Clock frequency ranges by mode

| Mode | f_CLK min | f_CLK max | VDD | Source |
|---|---|---|---|---|
| Sleep Mode | 0 | 50 kHz | 1.6–3.6 V | [p. 3] |
| Low-Power Mode | 150 kHz | 900 kHz | 1.6–3.6 V | [p. 3] |
| Standard Performance Mode | 1.1 MHz | 4.0 MHz | 1.6–3.6 V | [p. 3] |

Mode is determined **entirely by the CLK frequency applied** — there is no separate mode register or control pin. The mic automatically enters the correct mode based on where f_CLK falls. [p. 6]

### Timing parameters

| Parameter | Symbol | Min | Typ | Max | Units | Conditions | Source |
|---|---|---|---|---|---|---|---|
| Clock rise/fall time | t_EDGE | — | — | 20 | ns | — | [p. 7] |
| Delay time to High-Z | t_DZ | — | — | 40 | ns | DATA → Hi-Z after active half | [p. 7] |
| Delay time to data driven | t_DD | — | — | 50 | ns | DATA valid after CLK edge | [p. 7] |
| Fall-asleep time | — | — | — | 30 | µs | f_CLK ≤ 50 kHz | [p. 3] |
| Wake-up time | — | — | — | 200 | µs | f_CLK ≥ 151 kHz | [p. 3] |
| Power-up time | — | — | 6 | 20 | ms | VDD ≥ V(min) | [p. 3] |
| Mode-change time | — | — | — | 10 | ms | Any mode transition | [p. 3] |

**Sample rate derivation (Standard Performance Mode, f_CLK = 1.1–4.0 MHz):**

The PDM bitstream must be decimated by the host to recover PCM audio. The decimation ratio determines the audio sample rate. The ESP32-S3 I2S-PDM-RX hardware decimation filter typically supports a fixed oversampling ratio of 64×.

| Target sample rate | Required f_CLK (at 64× decimation) | In-range? |
|---|---|---|
| 16 kHz | 64 × 16,000 = 1.024 MHz | Borderline — below 1.1 MHz min for Standard mode; would fall in gap between Low-Power max (900 kHz) and Standard min (1.1 MHz). **Not cleanly achievable.** |
| 44.1 kHz | 64 × 44,100 = 2.8224 MHz | Within Standard mode range (1.1–4.0 MHz). Achievable. |
| 48 kHz | 64 × 48,000 = 3.072 MHz | Within Standard mode range (1.1–4.0 MHz). Achievable. Preferred target. |

Note: the ESP32-S3 PDM RX decimation ratio is configurable (the `dn_sample_mode` field in `i2s_pdm_rx_config_t` can select ×64 or ×128 downsampling). At ×64 and f_CLK = 3.072 MHz, audio output = 48 kHz. The datasheet test condition uses f_CLK = 2.4 MHz (yielding 37.5 kHz equivalent decimated rate at 64×), which is non-standard audio — the 2.4 MHz figure is a characterisation convenience, not a recommended operating point. For Kompic, **f_CLK = 3.072 MHz → 48 kHz PCM** is the target.

For 16 kHz: use ×128 decimation at f_CLK = 2.048 MHz (within Standard mode range) → 16 kHz output. Alternatively, decimate 48 kHz PCM in firmware to 16 kHz.

---

## Power consumption

| State | Condition | Current (typ) | Source |
|---|---|---|---|
| Standard Performance Mode | f_CLK = 2.4 MHz, VDD = 1.8 V | 670 µA | [p. 4] |
| Low-Power Mode | f_CLK = 768 kHz, VDD = 1.8 V | 290 µA | [p. 5] |
| Sleep Mode | f_CLK ≤ 50 kHz, VDD = 1.8 V | 1 µA (typ) | [p. 3] |
| Powered Down | VDD = 0 V | 0 | [p. 6] |

**Sleep mode entry:** reduce f_CLK to ≤ 50 kHz. Fall-asleep time ≤ 30 µs. The mic remains powered (VDD held); only CLK is throttled. [p. 3, p. 6]

**Wake from sleep:** raise f_CLK to ≥ 151 kHz. Wake-up time ≤ 200 µs. [p. 3]

**Power down:** remove VDD entirely (VDD = 0 V). Requires full power-up sequence on re-enable (power-up time 6–20 ms). [p. 6]

**Power budget at 1.8 V (Kompic):**
- Standard mode: 670 µA × 1.8 V = **1.2 mW**
- Low-power mode: 290 µA × 1.8 V = **0.52 mW**
- Sleep: 1 µA × 1.8 V = **1.8 µW**

---

## Package

**LGA (Land Grid Array), metal can**

| Dimension | Value | Tolerance |
|---|---|---|
| Length (L) | 4.00 mm | ±0.10 mm |
| Width (W) | 2.00 mm | ±0.10 mm |
| Height (H) | 1.10 mm | ±0.10 mm |
| Acoustic port diameter | Ø0.65 mm | ±0.05 mm |

[p. 9]

**Orientation:** Top-ported — the acoustic port (Ø0.65 mm hole) is on the top face of the metal can. The PCB must have a matching hole beneath the port if the mic faces down, or the port must be exposed to the sound path. For Kompic, the acoustic port faces up (toward the PTFE sticker / case hole). [p. 2, p. 9]

**Pad layout (bottom view, 6 pads):**

Pads are arranged in two columns of three (left column: 1, 2, 3; right column: 4, 5, 6 — numbered from bottom-left, bottom-right, up):

| Column left | Column right |
|---|---|
| PIN 3 = DATA (top-left) | PIN 4 = CLK (top-right) |
| PIN 2 = GND (mid-left) | PIN 5 = GND (mid-right) |
| PIN 1 = VDD (bot-left) | PIN 6 = L/R (bot-right) |

Pad dimensions (from bottom view drawing): each pad approximately 0.64 mm tall × 0.57 mm wide, with 0.3 mm spacing between pad rows. Corner radius on package body R0.319 mm. [p. 9]

**MSL rating:** Class 1 — no bake required before reflow. [p. 10]

**Maximum reflow cycles:** 3. [p. 10]

**Reflow peak:** 260°C max. [p. 8]

**Tape & reel:** EIA-481 standard, 13-inch reel, 5700 units per reel. [p. 11]

---

## ESP32-S3 I2S-PDM configuration notes

### Driver configuration (ESP-IDF I2S PDM RX)

```c
i2s_chan_config_t chan_cfg = I2S_CHANNEL_DEFAULT_CONFIG(I2S_NUM_0, I2S_ROLE_MASTER);
i2s_new_channel(&chan_cfg, NULL, &rx_handle);

i2s_pdm_rx_config_t pdm_rx_cfg = {
    .clk_cfg = {
        .sample_rate_hz = 48000,
        .clk_src         = I2S_CLK_SRC_DEFAULT,
        .mclk_multiple   = I2S_MCLK_MULTIPLE_256,  // not used in PDM RX
        .dn_sample_mode  = I2S_PDM_DSR_8S,          // x64 decimation
    },
    .slot_cfg = I2S_PDM_RX_SLOT_DEFAULT_CONFIG(I2S_DATA_BIT_WIDTH_16BIT,
                                                I2S_SLOT_MODE_MONO),
    .gpio_cfg = {
        .clk  = GPIO_NUM_47,    // Mic_CLK
        .din  = GPIO_NUM_48,    // Mic_Dout
        .invert_flags = {
            .clk_inv = false,
        },
    },
};
i2s_channel_init_pdm_rx_mode(rx_handle, &pdm_rx_cfg);
```

### CLK frequency calculation

The ESP32-S3 I2S PDM RX clock is derived from the APB or PLL clock and divided down. The CLK output frequency on GPIO47 equals:

**f_CLK = sample_rate × decimation_ratio**

| sample_rate_hz | dn_sample_mode | decimation | f_CLK on GPIO47 | In mic Standard mode range? |
|---|---|---|---|---|
| 48,000 | I2S_PDM_DSR_8S (×64) | 64 | 3.072 MHz | Yes (1.1–4.0 MHz) |
| 16,000 | I2S_PDM_DSR_8S (×64) | 64 | 1.024 MHz | No — below 1.1 MHz min |
| 16,000 | I2S_PDM_DSR_16S (×128) | 128 | 2.048 MHz | Yes (1.1–4.0 MHz) |
| 44,100 | I2S_PDM_DSR_8S (×64) | 64 | 2.8224 MHz | Yes |

**Recommended operating point for Kompic:** 48 kHz, ×64 decimation, f_CLK = 3.072 MHz.

**For 16 kHz capture:** use ×128 decimation (I2S_PDM_DSR_16S) with sample_rate_hz = 16,000 → f_CLK = 2.048 MHz. Do not try 16 kHz with ×64 (f_CLK = 1.024 MHz falls in the dead band between Low-Power max 900 kHz and Standard min 1.1 MHz).

### L/R pin setting for single channel

JP9 is soldered to GND by default → L/R = GND → **Mic(Low)** mode:
- DATA is asserted on the **CLK falling edge**
- The host latches DATA on the **CLK rising edge**

ESP32-S3 PDM RX in `I2S_SLOT_MODE_MONO` with default slot configuration reads the left channel (CLK-falling-edge data), which is exactly what Mic(Low)/L=GND provides. No inversion flags needed.

If a second mic were added (stereo), it would tie L/R to VDD (Mic(High)), share the DATA line, and assert on the rising edge — the two mics share one wire without contention because each drives only during its own half-cycle.

### Decoupling

Place 100 nF ceramic + 10 µF ceramic on VDD as close to PIN 1 as possible. [p. 12] The 1.8V rail is a low-noise LDO output (XC6206) which helps, but the decoupling is still required. The PSRR of 50 dBV/FS at 1 kHz means a 200 mVpp ripple on VDD injects a −50 dBFS signal into the audio — keep the 1.8V rail clean.

### Sleep strategy

To put the mic to sleep without removing power: reduce f_CLK to ≤ 50 kHz (or stop the CLK entirely — 0 Hz is within the sleep range). The mic enters sleep in ≤ 30 µs, drawing 1 µA. Wake by restoring f_CLK ≥ 151 kHz; allow ≤ 200 µs before valid data.

In ESP-IDF: `i2s_channel_disable(rx_handle)` stops the CLK. Re-enable with `i2s_channel_enable(rx_handle)` and discard the first ~200 µs of samples.

---

## Datasheet notes

- [p. 2] Part is described as "omnidirectional, top-ported, PDM digital output MEMS microphone." Package confirmed 4 mm × 2 mm × 1.1 mm metal can LGA.
- [p. 2] Fourth-order Σ-Δ modulator. Features include multiple modes (Sleep, Low-Power, Standard Performance) and sensitivity matching within ±1 dB between units.
- [p. 3] Test conditions for all specifications: 25 ±10°C, 50 ±20% R.H., VDD = 1.8 V, f_CLK = 2.4 MHz, L/R pin grounded, no load.
- [p. 3] Mode is controlled entirely by CLK frequency — no register writes, no I2C, no SPI. Pure hardware state machine.
- [p. 3] DC output offset is 4% FS (typ) — this is a normal PDM characteristic; the decimation filter in the ESP32 will center the output. No action needed in firmware beyond standard I2S-PDM driver.
- [p. 6] State diagram confirms four states: Powered Down (VDD=0), Sleep (f_CLK ≤ 50 kHz), Low-Power (150 kHz ≤ f_CLK ≤ 900 kHz), Standard Performance (1.1 MHz ≤ f_CLK ≤ 4 MHz). Transitions are automatic based on f_CLK and VDD.
- [p. 7] Frequency response graph (94 dB SPL) shows flat response approximately 200 Hz–5 kHz, mild rise above 5 kHz. Low-end rolloff visible below ~200 Hz. Graph x-axis: 100 Hz–10 kHz.
- [p. 7] Timing diagram clarifies the ½-cycle PDM scheme. DATA line goes to High-Z for the half-cycle when this mic is not the active talker. This is key for stereo shared-wire operation.
- [p. 9] Pin 1 marker (triangle/chamfer) is at bottom-left corner of package bottom view.
- [p. 10] MSL Class 1 — no moisture bake required. Max 3 reflow cycles. Do not board wash, brush, or ultrasonically clean after reflow. Do not apply pressure or vacuum to the acoustic port.
- [p. 10] Floor life (out of bag): ≤ 4 weeks at ≤ 75% RH.
- [p. 12] Recommended interface shows ESD protection diodes (PESD5V0F1BL) on CLK and DATA lines, series impedance Z_rf on CLK and DATA, and termination resistor R_term at the processor end. Decoupling: 100 nF + 10 µF on VDD.
- [p. 13] ESD: ±2 kV HBM on I/O pins, ±8 kV LID-GND (lid to ground), ±200 V MM.
- [p. 13] Reliability sensitivity note: sensitivity shall vary within ±3 dB of initial value after all reliability tests (measured after 2 hours conditioning at 25 ±10°C, 50 ±20% RH).

---

## Warnings & Errata

| ID | Title | Impact | Notes |
|---|---|---|---|
| W1 | CLK voltage domain mismatch | MEDIUM | GPIO47 is in the "3.3V domain on R8" (iv7.1 system instructions). The mic VDD = 1.8 V, so CLK VIH max is 3.6 V absolute. A 3.3V GPIO driving CLK to the mic is within the absolute maximum (3.6V), but the margin is only 0.3 V. The datasheet does not explicitly call out a max VIH beyond the absolute maximum supply spec of 4.0 V. However, best practice for a 1.8V-supply digital device is to use a 1.8V logic driver or add a series resistor to form a voltage divider. Verify on bring-up: measure VIH on CLK pin. If the 3.3V GPIO drives CLK without a level translator and the mic operates correctly, it is technically within absolute max ratings — but it is a reliability concern. |
| W2 | 16 kHz at ×64 decimation falls in CLK dead band | HIGH | f_CLK = 1.024 MHz (16 kHz × 64) is below the Standard Performance Mode minimum of 1.1 MHz and above the Low-Power Mode maximum of 900 kHz. The mic would be in an undefined transition zone. Always use ×128 decimation for 16 kHz (f_CLK = 2.048 MHz). |
| W3 | Acoustic port must not be blocked or pressurized | MEDIUM | The PTFE sticker on the case hole is the correct solution. Do not apply vacuum to the port during assembly (e.g., pick-and-place suction must not cover the port hole). The datasheet explicitly prohibits pressure or vacuum on the port. [p. 10] |
| W4 | No explicit operating temperature range stated | LOW | The datasheet gives storage temperature (−40 to +100°C) and reliability test ranges but does not state a separate operating temperature specification. For a wearable, operation from −20 to +60°C is assumed safe based on reliability testing to −40/+105°C, but this is not explicitly confirmed. |
| W5 | Mode-change time 10 ms must be respected | MEDIUM | When transitioning between modes by changing f_CLK (e.g., waking from sleep to standard mode), allow 10 ms before treating DATA as valid. [p. 3] |
| W6 | Power-up time 6–20 ms | MEDIUM | After VDD is applied, valid PDM data is not available for up to 20 ms. The firmware driver must discard the first ≥20 ms of samples after power-on, or after exiting power-down mode. |

---

## Open questions

1. **CLK level translator needed?** The CLK line (GPIO47) is in the 3.3V domain. The mic is a 1.8V device with VIH max equal to the absolute maximum supply of 3.6V (effectively). Is there a series resistor on R8 that already limits the CLK drive voltage, or is the GPIO swinging full 3.3V to the mic CLK pin? Check the schematic: if R8 is a series resistor on the clock line forming a divider with the mic's input impedance, the voltage at the CLK pin may be safe. If R8 is a pull-up resistor (to 3.3V) on the DATA line only, the CLK drive issue remains unmitigated.

2. **Operating temperature range?** The datasheet does not specify a minimum/maximum operating temperature. For a wrist-worn device (skin contact ~20–37°C ambient, but potential exposure to −10°C to +50°C outdoors), is there any guidance from MEMSensing? Not stated in the datasheet. Assume safe based on reliability qualification range.

3. **Frequency response −3 dB lower limit?** The graph (p. 7) shows rolloff below 200 Hz but the exact −3 dB low-frequency cutoff is not tabulated. For voice/keyword detection at 300 Hz+, this is fine. For full-bandwidth audio logging down to 20 Hz, the low-frequency rolloff may clip bass content. Characterise on bring-up with a known SPL source.

4. **Does the ESP-IDF I2S PDM RX driver correctly handle Mic(Low) (L/R=GND) without clock inversion?** The ESP32-S3 Technical Reference Manual should be cross-checked to confirm that the default PDM RX configuration reads DATA on the rising CLK edge, matching Mic(Low) behaviour. If the driver defaults to Mic(High) (rising-edge assertion), set `clk_inv = true` in `invert_flags`.

5. **Actual sensitivity in dBV/Pa?** The datasheet expresses sensitivity in dBFS (relative to digital full-scale), not dBV/Pa. Converting to dBV/Pa requires knowing the ADC reference, which is internal to the Σ-Δ modulator and not stated. For absolute SPL calibration, characterise against a known source on the bench. The ±1 dB sensitivity matching is useful for stereo applications but Kompic uses only one mic.

6. **R8 role clarification:** iv7.1 mentions "3.3V domain on R8" for both GPIO47 and GPIO48. Is R8 a single series resistor on the CLK line, a pull-up on DATA, or something else? This directly affects W1 above.

---

*20.19 — End of extract.*
