porupski/kompic-wearable/firmware/docs/datasheet_extracts/20.20_Miscellaneous_Passives_Reference_iv7.1_f0.0_2026-06-19.md

# 20.20 — MISCELLANEOUS COMPONENTS REFERENCE EXTRACT
**Date:** 2026-06-19 · **Hardware:** iv7.1 · **Firmware porting:** f0.0
**Parsed by:** Claude Code Sonnet 4.6
**Components:** BLE antenna, GPS patch antenna, RTC crystal, ESDALCL5 ESD, TPD2E001 ESD, ML621 backup cell, XC6206 1.8V LDO

---

## Cross-reference vs v7.1

| # | Component | Role | Key finding | Action needed |
|---|---|---|---|---|
| 1 | Johanson 2450AT18A0100001E | BLE/WiFi chip antenna | Confirmed 2.4–2.5 GHz — correct band for ESP32-S3 BLE/WiFi. NOT a GPS antenna. The flag from 20.08 was correct: this part is in the wrong position in the BOM if labelled as GPS antenna. As the BLE antenna it is the right part. | No firmware action. RF trace width at 0.17mm is a known open issue for the 1mm stackup. |
| 2 | BAT WIRELESS BWGNSCNX8-8W2 | GPS patch antenna | Confirmed 1575±5 MHz and 1561±5 MHz — GPS L1 and BeiDou B1. Passive (no LNA). RHCP. Correct band. Resolves 20.08 flag. | No firmware action. Confirm bias-T is absent (passive). |
| 3 | HCI FC31M2-32.768 | RTC oscillator crystal | CL must be specified at order: 6 / 9 / 12.5 pF options. Confirm which was ordered — drives PCB cap selection. ESR < 70 kΩ. | Confirm CL variant ordered. Check PCB caps match. |
| 4 | ESDALCL5-1BM2 | ESD, single-line, I2C / data lines | 26 pF typ capacitance at 1 MHz, 0 V bias — HIGH for I2C at 400 kHz; marginal but tolerable if placed at the IC side not the connector. Bidirectional. VBR = 5 V min. | No firmware action. Layout note: place as close to protected IC as possible. |
| 5 | TPD2E001 | ESD, 2-channel, USB D+/D- | 1.5 pF typ — excellent for USB 2.0 FS (12 Mbps) and CDC. ±8 kV contact / ±15 kV air. Leakage ≤ 1 nA. | No firmware action. Fits USB FS perfectly. |
| 6 | Panasonic ML621 | RTC backup rechargeable cell | 5.0 mAh, 3.0 V nominal, CV charging 2.8–3.2 V. Present 3.2V rail → 1×1N4148 clamp gives ~2.5 V at cell — BELOW the 2.8 V guaranteed minimum. Needs re-check. | CRITICAL: verify actual charge voltage at cell. May need lower Vf diode or second diode removed. |
| 7 | Torex XC6206P182MR | 1.8 V LDO | Confirmed 1.8 V output. Max I_out = 80 mA (table E-4 for 1.8 V row). Dropout = 150 mV typ at 60 mA (Dropout Voltage 1 table). Quiescent 1.0 µA typ, 3.0 µA max. No enable pin — always on when VIN is present. VIN range 1.8–6.0 V. | No firmware action. Budget 1.8V rail against 80 mA limit. |

---

## Part A — BLE Antenna: Johanson 2450AT18A0100001E

### Band confirmation
**This is a 2.4–2.5 GHz chip antenna.** [Antenna-2450AT18A0100001E-Rev4.0.pdf p. 1]

It is the correct antenna for the ESP32-S3-WROOM-1U BLE and WiFi radios (2400–2500 MHz). The flag raised in extract 20.08 — "the BOM antenna is 2.4 GHz, wrong band for GPS" — was correct. The antenna is correctly assigned to BLE; the GPS receiver (MAX-M10S) uses the separate BAT WIRELESS BWGNSCNX8-8W2 ceramic patch. No band conflict exists once the two antennas are understood as separate BOM lines.

### Electrical specifications
| Parameter | Value | Source |
|---|---|---|
| Passband frequency | 2400–2500 MHz | [p. 1] |
| Impedance | 50 Ω | [p. 1] |
| Return loss | 9.5 dB min (band edge); −15.98 dB typ @ 2450 MHz | [p. 1, p. 4] |
| Peak gain | 1.5 dBi typ | [p. 1] |
| Average gain | 0.0 dBi typ | [p. 1] |
| Average radiated efficiency | 74% | [p. 1] |
| Radiation pattern | Near-omnidirectional in horizontal plane | [p. 4] |
| Power capacity | 3 W max (CW) | [p. 1] |
| Operating temperature | −40 to +125°C | [p. 1] |

### Package / dimensions
| Dimension | Value |
|---|---|
| Package | SMD, EIA 1206, Nickel Tin termination |
| Length (L) | 3.20 ± 0.20 mm |
| Width (W) | 1.60 ± 0.20 mm |
| Thickness (T) | 1.30 +0.10/−0.20 mm |
| Terminal a (end cap) | 0.50 ± 0.30 mm |
| Pin 1 | Feed |
| Pin 2 | NC* (must be soldered for mechanical stability) |

[Antenna-2450AT18A0100001E-Rev4.0.pdf p. 2]

### Matching network (evaluation board reference values)
The evaluation board uses a tee (series–shunt–series) network: [p. 3]

| Component | Value | JTI P/N |
|---|---|---|
| C (series, toward antenna) | 1.0 pF | QSCF500Q1R0B1GV001T |
| L (shunt to GND) | 2.7 nH | LRC0402CS2N7GV001T |
| L (series to antenna pad) | 3.9 nH | LRC0402CS3N9GV001T |

**Critical note:** These values are for Johanson's own evaluation board (P/N 2450AT18A0100001CE1), which uses a specific stackup and trace geometry. The system instructions confirm matching network values on the Kompic PCB are documented as 1 pF series, 2.7 nH shunt, 3.9 nH series — matching the JTI reference — but the datasheet explicitly states: *"matching values on client's PCB will be different, depending on the layout, thickness, material, etc."* [p. 3] These must be re-verified after the 1 mm 4-layer stackup is finalised and the 50 Ω trace width is corrected.

### PCB keep-out and layout
- Corner-mount recommended. [p. 1]
- Ground clearance zone at antenna end: 6.5 × 4 mm minimum (measured from evaluation board drawing). [p. 3]
- Evaluation board overall ground plane: 39.5 × 13.5 mm. The antenna sits on the short edge corner. [p. 3]
- Ground vias adjacent to the matching network "highly recommended to have better antenna efficiency." [p. 3]
- Feed line is GCPW (grounded coplanar waveguide) at 50 Ω on the evaluation board. [p. 3]
- System instructions document keep-out as approximately 14 × 8 mm, 3 mm GND clearance on all layers. This is consistent with the datasheet geometry.

### Known open issue (from system instructions)
RF traces are laid at 0.17 mm, carried over from the 0.8 mm stackup design. The actual 1 mm 4-layer stackup has not been characterised for 50 Ω width. Both the trace width and the matching network values must be re-derived before trusting antenna performance. [02_Kompic_Mk1_System_Instructions_v7.1.md, Open Issues §1]

---

## Part B — GPS Patch Antenna: BAT WIRELESS BWGNSCNX8-8W2

### Band confirmation — RESOLVES 20.08 FLAG
**Confirmed: this antenna operates at 1575±5 MHz (GPS L1) and 1561±5 MHz (BeiDou B1).** [BWGNSCNX8-8W2.pdf p. 1, p. 4]

This is the correct antenna for the MAX-M10S GPS receiver. The 20.08 extract flagged that the BOM label "Antenna-2450AT18A0100001E" appeared under the GPS line item — that was a BOM annotation error. The actual GPS antenna fitted is the BWGNSCNX8-8W2, which is definitively L1/B1 band. The 20.08 concern is closed.

### Electrical specifications
| Parameter | Value | Source |
|---|---|---|
| Frequency range | 1575±5 MHz (GPS L1) and 1561±5 MHz (BeiDou B1) | [p. 1, p. 4] |
| Antenna type | Passive ceramic patch | [p. 1, p. 4] |
| Input impedance | 50 Ω | [p. 4] |
| V.S.W.R | < 3 (spec); measured: 1.39 @ 1561 MHz, 3.07 @ 1575 MHz | [p. 4, p. 9] |
| Gain (spec) | 1 dBi (typ) | [p. 4] |
| Measured gain @ 1575 MHz | 0.17 dBi | [p. 10] |
| Measured gain @ 1570 MHz | 0.80 dBi (peak across band) | [p. 10] |
| Measured gain @ 1580 MHz | −1.13 dBi | [p. 10] |
| Polarization | RHCP (right-hand circular) | [p. 4] |
| Return loss @ 1561 MHz | −12.785 dB (measured) | [p. 9] |
| Return loss @ 1575 MHz | −6.25 dB (measured) | [p. 9] |
| Efficiency @ 1575 MHz | 39.08% (measured) | [p. 10] |
| Efficiency @ 1570 MHz | 44.67% (measured, peak) | [p. 10] |
| LNA | None — passive antenna only | [p. 1, p. 4] |
| DC voltage input | Not applicable (passive) | [p. 4] |
| Power capacity | 50 W | [p. 4] |
| Operating temperature | −45°C to +85°C | [p. 4] |
| Storage temperature | −45°C to +85°C | [p. 4] |

### Mechanical specifications
| Parameter | Value | Source |
|---|---|---|
| Dimensions | 8 mm × 8 mm × 2 mm | [p. 1, p. 4, p. 6] |
| Material | Ceramic dielectric | [p. 4] |
| Color | Silver White | [p. 4] |
| Weight | 3.2 g | [p. 4] |
| Connector type | Not specified (bare pin/pad — ANT pin + GND pin) | [p. 3] |

### Mounting method
The datasheet shows a feed pin (ANT connection) and a ground pin for convenient soldering. [p. 3] The system instructions confirm: "ceramic patch on edge, perpendicular to the PCB; feed pin soldered to top copper; radiating face aimed through its epoxy window; 50 Ω feed trace from bias-T < 5 mm, top layer only." [02_Kompic_Mk1_System_Instructions_v7.1.md]

### Performance notes
- VSWR at 1575 MHz measures 3.07 — exceeding the < 3 specification. This is marginal but not unusual for a passive ceramic patch of this size without active matching. Acceptable for a wearable tracker where sensitivity is secondary to form factor. [p. 9]
- Efficiency at L1 is 39%, which is moderate for an 8×8 mm passive patch. A wearable environment (body shadowing, epoxy window) will further reduce effective gain. No LNA is present, so the MAX-M10S input sensitivity determines system NF. The MAX-M10S has its own integrated LNA.
- RHCP matches GPS satellite polarization. [p. 4]
- The antenna was designed for BeiDou/GPS dual-band use (1575 and 1561 MHz). [p. 1, p. 3]

---

## Part C — RTC Crystal: HCI FC31M2-32.768-NTLLLDT

### Frequency confirmation
**Confirmed: 32.768 kHz, fundamental mode.** [FC31M2-32.768-NTLLLDT.pdf p. 1]

This is the correct crystal for the PCF85063A RTC.

### Electrical specifications
| Parameter | Value | Conditions / Notes | Source |
|---|---|---|---|
| Nominal frequency | 32.768 kHz | Fundamental mode | [p. 1] |
| Crystal mode | Fundamental | | [p. 1] |
| Frequency tolerance | ±20 / ±30 / ±50 ppm | Must be specified at order; other options available | [p. 1] |
| Stability over temperature | −0.03 ± 0.01 ppm/ΔT² | Parabolic coefficient (T in °C from turning point) | [p. 1] |
| Turning point temperature | 25 ± 5°C | | [p. 1] |
| Equivalent series resistance (ESR) | < 70 kΩ | | [p. 1] |
| Shunt capacitance C0 | 1.5 pF typ | | [p. 1] |
| Motional capacitance C1 | 3.3 fF typ | | [p. 1] |
| Load capacitance (CL) | 6 pF / 9 pF / 12.5 pF | Must be specified at order | [p. 1] |
| Drive level | 0.1 µW typ / 0.5 µW max | | [p. 1] |
| Aging | ±3 ppm/year | At +25°C | [p. 1] |
| Operating temperature | −40 to +85°C | Other options available | [p. 1] |
| Storage temperature | −55 to +125°C | | [p. 1] |

### Package
| Parameter | Value | Source |
|---|---|---|
| Package type | SMD, 3.2 × 1.5 mm ceramic seam seal | [p. 1] |
| Dimensions | 3.2 ± 0.15 mm × 1.5 ± 0.15 mm × 0.9 mm max | [p. 1] |
| Pads | 2 solder pads, both CRYSTAL (symmetric) | [p. 1] |
| Land pattern suggestion | 1.7 mm pad length, 2.5 mm pad spacing centre-to-centre | [p. 1] |

### Critical firmware/PCB design note — Load Capacitance
**The CL variant ordered determines which external caps to place.** The PCF85063A oscillator's effective load capacitance is set by the two PCB capacitors (C_ext1, C_ext2) in series plus stray capacitance (~2–3 pF typical for a short trace). General formula: CL = (C_ext1 × C_ext2)/(C_ext1 + C_ext2) + C_stray.

For the common 12.5 pF crystal with ~2.5 pF stray: two matched caps of ~20 pF each in series give approximately (20×20)/(20+20) + 2.5 = 12.5 pF. Verify actual CL variant on the BOM. If the 6 pF variant was ordered, caps should be approximately 7 pF each (series = 3.5 pF + 2.5 pF stray).

The datasheet does not specify which CL variant the NTLLLDT order code corresponds to — the ordering code suffix must be decoded or confirmed with HCI. [p. 1]

### Stability calculation
At body temperature ~35°C (ΔT = 10°C above turning point 25°C):
- Frequency deviation = −0.03 × 10² = −3 ppm. At 32.768 kHz this is ~0.1 Hz/s drift, or about 8.6 s/day — well within RTC correction range. The PCF85063A has a software offset register to correct this.

---

## Part D — ESDALCL5-1BM2 ESD Diode

### Description
Single-line, bidirectional, low-capacitance, low-leakage TVS diode. Designed to protect data lines or I/O ports. [ESDALCL5-1BM2.pdf p. 1]

### Electrical characteristics (Ta = 25°C)
| Parameter | Symbol | Condition | Value | Unit | Source |
|---|---|---|---|---|---|
| Breakdown voltage (pin1→pin2) | V_BR | I_R = 1 mA | 11 min, 13 typ | V | [p. 2] |
| Breakdown voltage (pin2→pin1) | V_BR | I_R = 1 mA | 5 min, 8 typ | V | [p. 2] |
| Stand-off / leakage current | I_RM | V_RM = 3 V | ≤ 10 nA | nA | [p. 2] |
| Stand-off / leakage current | I_RM | V_RM = 1 V | ≤ 1 nA | nA | [p. 2] |
| Dynamic resistance | R_d | Square pulse, I_PP = 1 A, t_p = 2.5 µs | 650 typ | mΩ | [p. 2] |
| Line capacitance | C_line | F = 1 MHz, V_R = 0 V | 26 typ, 30 max | pF | [p. 2] |
| Peak pulse voltage (ESD) | V_PP | IEC 61000-4-2 contact and air | ±30 kV | kV | [p. 2] |
| Peak pulse power | P_PP | 8/20 µs, T_j initial = T_amb | 150 W | W | [p. 2] |
| Peak pulse current | I_PP | 8/20 µs | 9 A | A | [p. 2] |

### ESD compliance
- IEC 61000-4-2 Level 4 and higher: ±30 kV air, ±30 kV contact discharge. [p. 1]
- MIL STD 883G Method 3015-7: Class 3 Human Body Model. [p. 1]

### Package
SOD882 (also designated M2). Body: 1.00 × 0.60 mm, height 0.47 mm typ. Very small: 0.6 mm² PCB area. [p. 1, p. 6]

### Application on Kompic Mk I
The ESDALCL5-1BM2 is a single-line device. On a wearable with multiple I2C lines and interrupt lines, each protected line requires one device. The system instructions do not explicitly identify which specific signals use this device vs. the TPD2E001.

**I2C signal integrity concern:** The 26 pF typ (30 pF max) line capacitance is significant. At I2C Fast Mode 400 kHz with 5.1 kΩ pull-ups and 3.2 V rail, the RC time constant is 5100 × 30×10⁻¹² = 153 ns. The I2C spec allows maximum rise time of 300 ns at 400 kHz (C_bus ≤ 400 pF, t_r ≤ 300 ns). A single ESDALCL5-1BM2 contributes 30 pF max per line. If multiple devices are daisy-chained on a bus that also has node capacitance, verify total C_bus remains under 400 pF. If used only at the connector/port entry point (not mid-bus), impact is limited. Datasheet recommends placement at the input of the device under protection. [p. 1]

**No firmware action required.** This is a passive protection device with no register interface.

---

## Part E — TPD2E001 ESD Diode

### Description
Two-channel, uni-directional TVS diode array for high-speed data interfaces. Rated to IEC 61000-4-2 Level 4. [tpd2e001.pdf p. 1]

### Electrical characteristics (V_CC = 5 V, T_A = −40°C to 85°C)
| Parameter | Symbol | Condition | Min | Typ | Max | Unit | Source |
|---|---|---|-----|-----|-----|---|---|
| Supply voltage | V_CC | | 0.9 | — | 5.5 | V | [p. 4] |
| Supply current | I_CC | | — | 1 | 100 | nA | [p. 4] |
| Diode forward voltage | V_F | I_F = 10 mA | 0.65 | — | 0.95 | V | [p. 4] |
| Breakdown voltage | V_BR | I_BR = 10 mA | 11 | — | — | V | [p. 4] |
| Channel clamp voltage (±15 kV HBM) | V_C | I_F = 10 A, positive transients | — | — | V_CC + 25 | V | [p. 4] |
| Channel clamp voltage (±8 kV contact) | V_C | I_F = 24 A, positive transients | — | — | V_CC + 60 | V | [p. 4] |
| Channel clamp voltage (±15 kV air) | V_C | I_F = 45 A, positive transients | — | — | V_CC + 100 | V | [p. 4] |
| Channel leakage current | I_IO | V_IO = GND to V_CC | −1 | — | 1 | nA | [p. 4] |
| Channel input capacitance | C_IO | V_CC = 5 V, bias = V_CC/2, f = 10 MHz | — | 1.5 | — | pF | [p. 4] |

### ESD ratings
| Standard | Level | Value | Source |
|---|---|---|---|
| IEC 61000-4-2 contact | Level 4 | ±8 kV | [p. 4] |
| IEC 61000-4-2 air-gap | Level 4 | ±15 kV | [p. 4] |
| HBM (ANSI/ESDA/JEDEC JS-001) | — | ±15 kV | [p. 4] |
| CDM (JESD22-C101) | — | ±1 kV | [p. 4] |

### Application on Kompic Mk I — USB D+/D-
The application schematic in the datasheet shows IO1 → D+ and IO2 → D−, with V_CC tied to V_BUS via 0.1 µF bypass. [p. 1, p. 7] The system instructions confirm: "D+/D- via TPD2E001 to IO20/IO19." [02_Kompic_Mk1_System_Instructions_v7.1.md]

At 1.5 pF per channel, the capacitive loading on USB D+/D- is negligible for USB 2.0 Full Speed (12 Mbps) and well within USB 2.0 Hi-Speed (480 Mbps) tolerance if the native USB port is ever used at higher speed. The ESP32-S3's native USB operates at USB 2.0 Full Speed only, so even 10× this capacitance would not matter.

**V_CC connection for Kompic:** Since there is no USB VBUS detected in the system instructions (USB-C CC pins set device mode with 5.1 kΩ to GND), the V_CC pin should be connected to the 3.3 V or 5 V rail via 0.1 µF bypass, or left with only the bypass cap per the datasheet's Option 2 (0.1 µF cap only, no supply rail connection) allowing IO voltage swing up to 10 V. In USB CDC use the IO lines swing 0–3.3 V (ESP32-S3 GPIO levels), so V_CC to 3.3 V with 0.1 µF bypass is the clean choice. [p. 7–8]

### Package
Available in SOT-5X3 (DRL, 5-pin, 1.60×1.20 mm), USON (DRY, 6-pin, 1.45×1.00 mm), WSON (DRS, 6-pin, 3.00×3.00 mm), SOT-23 (DZD, 4-pin, 2.90×1.30 mm). [p. 1] The LCSC BOM variant must be checked to identify the specific package on the Kompic board.

**No USB-specific certification stated in the datasheet.** The device is listed for USB 2.0 as a primary application. [p. 1]

**No firmware action required.**

---

## Part F — ML621 Rechargeable Backup Cell

### Description
Panasonic ML621 — coin-type manganese rechargeable lithium battery, intended for RTC/memory backup. [ML621.pdf p. 1]

### Specifications
| Parameter | Value | Notes | Source |
|---|---|---|---|
| Nominal voltage | 3.0 V | | [p. 1] |
| Charging voltage (guaranteed) | 2.8 V to 3.2 V | At −20°C to +60°C | [p. 1, p. 2] |
| Nominal capacity | 5.0 mAh | Drain to 2.0 V cutoff, 20°C; standard condition: CV 3.1 V, 1 kΩ, 50 h discharge: 200 kΩ | [p. 1, p. 2] |
| Continuous drain | 0.01 mA (10 µA) | | [p. 1] |
| Diameter | 6.8 mm max | Without tabs | [p. 1] |
| Height | 2.1 mm max | Without tabs | [p. 1] |
| Weight | Approx. 0.22 g | | [p. 1] |
| Operating temperature | −20°C to +60°C | Both discharge and charging | [p. 1] |
| Charging system | Constant-voltage (CV) only | Trickle charging FORBIDDEN | [p. 1, p. 2] |
| Charge/discharge cycles | Approx. 1,000 at 10% depth of discharge | | [p. 1] |
| Self-discharge (retention) | ~80% at 150 days at 60°C, 3.1 V continuous charging; ~60% at 300 days at 60°C | From Fig. (continuous charging, high temperature stress) | [p. 2] |

### Charging circuit on Kompic Mk I
From system instructions: "ML621 rechargeable cell (5.5 mAh), 1×1N4148 + 10 kΩ charge limit. At the PCF85063's sub-µA timekeeping draw this holds the clock for ~4 years." [02_Kompic_Mk1_System_Instructions_v7.1.md]

**Critical discrepancy — charge voltage:**
- The 3.2 V rail charges through one 1N4148 diode (V_f ≈ 0.6–0.7 V forward). At 10 µA (the level in the RTC backup circuit), V_f for a 1N4148 is approximately 0.5–0.55 V (much lower than the 0.7 V at 10 mA).
- Cell charge voltage ≈ 3.2 V − 0.5 V = 2.7 V — this falls BELOW the 2.8 V minimum guaranteed charging voltage.
- At 2.7 V the datasheet warns: "It is not possible for the battery to recover completely when the charging voltage is below the specification." [p. 2]
- **Action required:** Increase charge voltage to ensure cell sees ≥ 2.8 V. Options: (a) use the Schottky diode instead of 1N4148 (V_f ≈ 0.2–0.3 V at low current → cell gets 2.9–3.0 V); (b) use 3.3 V rail if available as charge source; (c) verify actual 3.2 V rail voltage and actual diode drop at the circuit's charge current. The BQ25619's REGN reference (~3.3–3.5 V) could be an alternative source if accessible.

**Trickle charging prohibition:** The current Kompic charging circuit (1N4148 + 10 kΩ from 3.2 V) is a passive constant-current-limiting resistor plus diode, not a true CV charger. It approximates CV because the cell voltage will rise until it equals (V_rail − V_diode), at which point current drops to approximately zero. This is acceptable as a passive CV approximation. The prohibition on trickle charging refers to forcing current into a fully-charged cell, which this circuit avoids because the diode + resistor current naturally falls as the cell charges up. However, if the cell voltage ever exceeds the rail-minus-diode voltage, the diode blocks reverse current — correct behavior.

### RTC backup duration calculation
The PCF85063A (from its datasheet, not in this extract) has a timekeeping current of approximately 0.25 µA typical in backup mode.

- ML621 capacity: 5.0 mAh
- PCF85063A backup current: ~0.25 µA (estimate — verify from 20.04 PCF85063A extract)
- Backup duration (ignoring self-discharge): 5.0 mAh / 0.00025 mA = 20,000 hours = ~833 days = ~2.3 years
- Self-discharge: ML621 self-discharge at room temperature is not explicitly stated as a rate. At 20°C the continuous-charging chart shows nearly 100% retention over 300 days at 3.1 V. Without charging, the cell will self-discharge much faster — a conservative estimate for Li-Mn coin cells is ~1–3% per year at 25°C, but this is not stated in the datasheet.
- System instructions state "~4 years" as an order-of-magnitude estimate. This is plausible if the cell is frequently recharged during normal watch operation, but 4 years without any charge from the main rail is optimistic.
- **Backup behavior when main battery is removed:** the cell will drain at ~0.25 µA. 5 mAh / 0.00025 mA = 20,000 h ≈ 833 days ≈ 2.3 years from full charge. This assumes no other leakage paths.
- **Capacity discrepancy:** System instructions reference "5.5 mAh" for the ML621. Datasheet specifies 5.0 mAh. Use 5.0 mAh for calculations.

---

## Part G — XC6206 1.8V LDO

### Description
Torex XC6206 series — CMOS positive LDO voltage regulator, low ESR ceramic capacitor compatible, laser-trimmed output voltage, current-limiting short-circuit protection. [xc6206.pdf p. 1]

### Identification of specific variant
Part number on Kompic: **XC6206P182MR** (from system instructions). Decoding: P = positive, 18 = 1.8 V output, 2 = ±2% accuracy (V_OUT ≥ 1.5 V), MR = SOT-23, 3000 pcs/reel. [p. 2]

### Electrical specifications (Ta = 25°C)
| Parameter | Symbol | Conditions | Min | Typ | Max | Unit | Source |
|---|---|---|-----|-----|-----|---|---|
| Output voltage | V_OUT | Standard, I_OUT = 30 mA | ×0.98 | 1.8 V | ×1.02 | V | [p. 4] |
| Output voltage accuracy | — | High accuracy (Acc=1 variant, n/a here) | — | ±2% | — | | [p. 4] |
| Supply current (quiescent) | I_DD | No load | — | 1.0 | 3.0 | µA | [p. 4] |
| Input voltage range | V_IN | | 1.8 | — | 6.0 | V | [p. 4] |
| Maximum output current | I_OUTMAX | V_OUT ≥ V_OUT(E) × 0.9 | 80 | — | — | mA | [p. 5, table E-4, V_OUT = 1.8 V row] |
| Dropout voltage 1 (Vdif1) | V_dif1 | I_OUT = 30 mA, V_OUT(T) = 1.8 V | — | 150 typ | 390 max | mV | [p. 5, table E-2/E-3, V_OUT = 1.8 V row] |
| Dropout voltage 2 (Vdif2) | V_dif2 | I_OUT = 60 mA, V_OUT(T) = 1.8 V | — | 450 typ | 810 max | mV | [p. 5] |
| Dropout voltage 2 | V_dif2 | I_OUT = 100 mA, V_OUT(T) > 1.8 V | — | 350 typ | — | mV | [p. 5] |
| Load regulation | ΔV_OUT | 1 mA ≤ I_OUT ≤ 50 mA, V_OUT(T) ≤ 1.8 V | — | — | 45 max | mV | [p. 4] |
| Line regulation | ΔV_OUT/(ΔV_IN · V_OUT) | V_OUT(T) < 4.5 V, I_OUT = 30 mA | — | 0.05 | 0.25 | %/V | [p. 4] |
| Output voltage temp coefficient | — | I_OUT = 30 mA, −40°C to 85°C | — | ±100 | — | ppm/°C | [p. 4] |
| Operating temperature | T_opr | | −40 | — | +85 | °C | [p. 3] |

### Enable pin
**None.** The XC6206 is a 3-terminal device (V_SS, V_IN, V_OUT — no enable pin). Output is active whenever V_IN is present and above dropout. [p. 2–3]

Since the XC6206 VIN is fed from the TPS62840 3.2 V output, and the TPS62840 is always-on (EN = SYS rail), the 1.8 V rail is always on whenever the battery/USB is connected. There is no FW-controlled shutdown of the 1.8 V rail.

### Capacitor requirements
- Input capacitor: 1.0 µF ceramic minimum (place close to IC). [p. 1, p. 6]
- Output capacitor: 1.0 µF ceramic minimum. [p. 1, p. 6]
- Low ESR capacitors: ceramic. Compatible with MLCC. [p. 1]

### 1.8V rail consumers and current budget
| Consumer | Estimated current |
|---|---|
| MAX30101 VDDA | ~1.1 mA typ (from 20.11 MAX30101 extract) |
| BME688 VDD | ~2.1 mA typ active, ~0.1 µA sleep |
| LSM6DSV16X V_IO | ~2.7 mA active, <1 µA sleep |
| LIS3MDLTR VDD_IO | ~30 µA typ |
| MAX-M10S V_IO | ~2 mA active, <1 µA sleep |
| MEMS mic VDD | ~0.67 mA typ |
| **Total estimated active** | **~10 mA (well within 80 mA limit)** |

The 80 mA max current limit for the 1.8 V output at 1.8 V output voltage is not at risk under normal operation.

### Dropout check
V_IN = 3.2 V (from TPS62840), V_OUT = 1.8 V. Headroom = 1.4 V. Dropout voltage at 30 mA is 150 mV typical, 390 mV max. Headroom is ample — no dropout risk even at max current draw.

---

## System power budget summary (all rails)

This is a consolidated snapshot drawing on all prior extracts (20.01–20.20). Values are firmware-typical active estimates; sleep values are where known.

### 3.2V rail (from TPS62840, 750 mA rated)
| Consumer | Active typ | Sleep / standby |
|---|---|---|
| ESP32-S3-WROOM-1U | ~80–240 mA (WiFi Tx peak) / ~30 mA (active, no RF) | ~20 µA deep sleep |
| CO5300 AMOLED panel | ~40–80 mA @ full brightness | ~0 (SLPIN cuts boost) |
| CST9217 touch | ~3 mA active | ~100 µA standby |
| LSM6DSV16X VDD | ~0.55 mA active | ~3 µA acc-only |
| LIS3MDLTR VDD | ~0.3 mA active | ~1 µA sleep |
| TMP117 | ~135 µA active (4 Hz) | ~1.7 µA standby |
| VEML6030 | ~0.5 mA active | ~0.5 µA sleep |
| DRV2605 | ~12 mA active (haptic) | ~2 µA standby |
| PCF85063A RTC VDD | ~1 µA timekeeping | ~0.25 µA backup |
| MAX-M10S VCC | ~20 mA active (acquisition) | ~5 µA power-save |
| BME688 VDDIO | ~0.5 µA typ | |
| XC6206 quiescent | 1 µA typ | |
| **3.2V total (rough peak)** | **~180 mA active, no WiFi/display** | **~25 µA deep sleep** |

### 1.8V rail (from XC6206, 80 mA rated)
| Consumer | Active typ |
|---|---|
| MAX30101 VDDA | ~1.1 mA |
| BME688 VDD | ~2.1 mA |
| LSM6DSV16X V_IO | ~0.7 mA |
| LIS3MDLTR VDD_IO | ~0.03 mA |
| MAX-M10S V_IO | ~0.5 mA |
| MEMS mic VDD | ~0.67 mA |
| **1.8V total** | **~5 mA (margin to 80 mA is large)** |

### 5V rail (BQ25619 PMID boost, FW-gated, mutually exclusive with charging)
| Consumer | Current |
|---|---|
| MAX30101 VDD_LED (IR+Red) | ~50 mA peak (both LEDs at max) |
| WS2812B RGB LED | ~60 mA max (full white) |
| Flashlight LED | ~13–23 mA (FET-limited, 94Ω series) |
| **5V total** | Application-dependent; boost rating 1 A |

### Backup rail
| Cell | Voltage | Consumer | Duration (full charge) |
|---|---|---|---|
| ML621 (RTC) | 3.0 V nom | PCF85063A ~0.25 µA | ~2.3 years (calculated) |
| 0.22F supercap (GPS) | ~2.7 V charged | MAX-M10S BBR ~15 µA | ~4 hours hot-start hold |

---

## Warnings & Errata

| ID | Title | Severity | Impact | Notes |
|----|---|---|---|---|
| W-20.20-01 | GPS antenna BOM annotation resolved | INFO | Prior 20.08 flag closed | BWGNSCNX8-8W2 is confirmed L1/B1 band. The 2450AT18A0100001E is correctly the BLE antenna. No hardware action. |
| W-20.20-02 | ML621 charge voltage below minimum | HIGH | Cell may not fully charge; long-term capacity degradation | 3.2 V rail − 1×1N4148 V_f (≈0.5 V at low current) = ~2.7 V at cell — below 2.8 V minimum. Replace 1N4148 with Schottky diode (e.g. BAT54, V_f ≈ 0.2 V at µA) to ensure ≥ 2.8 V at cell. Or verify with actual circuit measurement before dismissing. |
| W-20.20-03 | RF trace width not recalculated for 1mm stackup | HIGH | BLE antenna performance degraded; 50 Ω impedance not guaranteed | Known open issue. 0.17 mm traces from 0.8 mm design. Requires stackup characterisation and trace width re-derivation. Both BLE and GPS RF traces affected. |
| W-20.20-04 | Matching network values are evaluation board reference only | MEDIUM | Actual BLE antenna gain may be suboptimal | JTI explicitly states values will differ on customer PCB. Re-tune after stackup fix (W-20.20-03). |
| W-20.20-05 | ESDALCL5-1BM2 capacitance 26–30 pF per line | MEDIUM | Added capacitance on I2C bus; verify total C_bus < 400 pF | At 400 kHz, 5.1 kΩ pull-up + 30 pF gives t_r ≈ 150 ns — within spec for single device. Cumulative loading if multiple devices in series could approach limit. |
| W-20.20-06 | BWGNSCNX8-8W2 VSWR at 1575 MHz measures 3.07 (spec < 3) | LOW | Slight return loss degradation at GPS L1 centre; signal loss negligible | 3.07 vs < 3 spec is marginal. In a wearable with body-loading the resonant frequency will shift; final VSWR is environment-dependent. Monitor during bring-up. |
| W-20.20-07 | GPS patch antenna — passive, no LNA | INFO | MAX-M10S sees antenna with efficiency ~39% at L1 | The MAX-M10S has an internal LNA. Ensure the 50 Ω feed trace from antenna to module is < 5 mm (as documented) and well-matched to minimise noise figure degradation. |
| W-20.20-08 | HCI FC31M2 CL variant must be confirmed | MEDIUM | Wrong CL → wrong PCB cap values → frequency error | The NTLLLDT order code's CL (6/9/12.5 pF) is not decodable from this datasheet alone. Verify BOM against HCI ordering information before PCB cap placement. |
| W-20.20-09 | XC6206 has no enable pin — 1.8V always on | INFO | Cannot power-gate 1.8V sensors in sleep | All 1.8V consumers must self-enter low-power states in firmware. No hardware kill available on this rail. Budget ~5 µA standby for sensor V_IO leakage in sleep. |
| W-20.20-10 | ML621 trickle charging prohibition | INFO | Existing circuit is a passive CV approximation, not trickle charge | The 1N4148 + 10 kΩ from 3.2 V is acceptable circuit topology as long as the cell sees ≥ 2.8 V (see W-20.20-02). No active trickle forcing. |

---

## Open questions

1. **ML621 charge voltage:** What is the actual measured voltage at the ML621 terminals during normal operation? Given the 3.2 V rail and the 1N4148 V_f at the micro-amp charge current, the cell may be receiving < 2.8 V. Measure in circuit before trusting RTC backup longevity. Consider replacing with a Schottky diode.

2. **HCI FC31M2 CL variant:** What is the specific load capacitance (6, 9, or 12.5 pF) of the crystal variant ordered? The NTLLLDT suffix does not decode unambiguously from the datasheet. Confirm with HCI or the LCSC listing, then verify PCB cap values match.

3. **ESDALCL5-1BM2 application mapping:** Which specific signals on the Kompic PCB use ESDALCL5-1BM2 vs no ESD protection? The single-line device would logically be used on I2C lines at the connector, interrupt lines, or the USB CC lines (though CC uses 5.1 kΩ to GND which provides some protection). Confirm placement to assess capacitive loading budget.

4. **TPD2E001 package variant:** Which package variant (SOT-5X3 DRL, USON DRY, WSON DRS, or SOT-23 DZD) is fitted? The LCSC part number should clarify this. The 1.5 pF capacitance is package-independent for the electrical spec.

5. **TPD2E001 V_CC connection:** Is V_CC connected to 3.3 V (with 0.1 µF bypass) or left as a floating bypass cap only? For USB CDC at 3.3 V IO levels, V_CC to 3.3 V is the cleaner configuration. Confirm in schematic.

6. **GPS antenna keep-out and epoxy window alignment:** Is the ceramic patch antenna's radiating face correctly aimed through the epoxy window in the titanium case? The patch must have an unobstructed sky-facing window. Standard clear epoxy is RF-transparent; opaque filled epoxy may add loss.

7. **BLE/GPS 50 Ω trace width:** When is the stackup going to be characterised and traces re-routed? This blocks reliable RF performance for both antennas. Should be addressed before the first RF test.

8. **ML621 capacity discrepancy:** The system instructions reference "5.5 mAh" for the ML621, but the datasheet specifies 5.0 mAh. Use the datasheet 5.0 mAh for calculations.

9. **1.8V rail sensor sleep currents:** Confirm all 1.8V-domain sensors (MAX30101 VDDA, BME688, LSM6DSV16X V_IO, LIS3MDLTR VDD_IO, GPS V_IO, mic VDD) are correctly configured to enter low-power or shutdown mode in firmware sleep, since the XC6206 has no enable pin and the rail cannot be hardware-killed.

10. **GPS backup supercap vs ML621 in 20.08 vs this extract:** The 20.08 extract documented the GPS supercap hold time as ~2 hours. The system instructions say ~2 hours hot-start hold. The ML621 is solely for RTC (PCF85063A) backup; it does not back up the GPS. Confirm no cross-wiring between these two isolated backup domains.

---

*20.20 — End of extract.*
