porupski/kompic-wearable/firmware/docs/datasheet_extracts/20.21_Datasheet_Parse_Complete_Checklist_iv7.1_f0.0_2026-06-19.md

# 20.21 — DATASHEET PARSE COMPLETE CHECKLIST
**Date:** 2026-06-19 · **Hardware:** iv7.1 · **Firmware porting:** f0.0
**Status:** ALL PHASES COMPLETE (20.01–20.20)
**Compiled by:** Claude Code Sonnet 4.6

---

## Extract file index

| # | Chip / Component | File | Date | Key topics |
|---|---|---|---|---|
| 20.01 | CO5300 AMOLED | `20.01_CO5300_Datasheet_Extract_iv7.1_f0.0_2026-06-13.md` | 2026-06-13 | QSPI display pipeline, SLPIN/SLPOUT, layer engine, TE sync |
| 20.02 | CST9217 touch | `20.02_CST9217_Datasheet_Extract_iv7.1_f0.0_2026-06-13.md` | 2026-06-13 | I2C touch protocol, interrupt, reset, gesture |
| 20.03 | ESP32-S3-WROOM-1U | `20.03_ESP32-S3_Datasheet_Extract_iv7.1_f0.0_2026-06-13.md` | 2026-06-13 | GPIO matrix, I2C/SPI/I2S/PCNT, deep sleep, boot straps |
| 20.04 | PCF85063A RTC | `20.04_PCF85063A_Datasheet_Extract_iv7.1_f0.0_2026-06-13.md` | 2026-06-13 | I2C RTC, time/date/alarm registers, backup cell, 32.768 kHz oscillator |
| 20.05 | TPS62840 buck | `20.05_TPS62840_Datasheet_Extract_iv7.1_f0.0_2026-06-13.md` | 2026-06-13 | 3.2 V main rail, 750 mA, soft-start, <1 µA sleep, EN pin |
| 20.06 | VEML6030 light | `20.06_VEML6030_Datasheet_Extract_iv7.1_f0.0_2026-06-13.md` | 2026-06-13 | Ambient light sensor, I2C, ALS gain/integration, auto-range algorithm |
| 20.07 | LIS3MDLTR mag | `20.07_LIS3MDLTR_Datasheet_Extract_iv7.1_f0.0_2026-06-13.md` | 2026-06-13 | Magnetometer, ±4–16 Gauss, hard-iron cal in NVS, LRA magnet interference |
| 20.08 | MAX-M10S GPS | `20.08_MAX-M10S_Datasheet_Extract_iv7.1_f0.0_2026-06-13.md` | 2026-06-13 | NMEA/UBX I2C, 1PPS, supercap backup (~4 h), TTFF, power modes |
| 20.09 | TMP117 temp | `20.09_TMP117_Datasheet_Extract_iv7.1_f0.0_2026-06-13.md` | 2026-06-13 | Precision skin temp, ±0.1°C, I2C, alert thresholds, thermal pad solder |
| 20.10 | LSM6DSV16X IMU | `20.10_LSM6DSV16X_Datasheet_Extract_iv7.1_f0.0_2026-06-13.md` | 2026-06-13 | Accel/gyro, SFLP quaternion, MLC, FSM, raise-to-wake, INT1 |
| 20.10b | LSM6DSV16X Advanced | `20.10b_LSM6DSV16X_Advanced_Features_iv7.1_f0.0_2026-06-13.md` | 2026-06-13 | MLC programs, FSM, Qvar, embedded functions register detail |
| 20.11 | MAX30101 PPG | `20.11_MAX30101_Datasheet_Extract_iv7.1_f0.0_2026-06-18.md` | 2026-06-18 | Heart rate/SpO2, FIFO, IR+Red LEDs on 5V, INT, SpO2 mode |
| 20.12 | BME688 env | `20.12_BME688_Datasheet_Extract_iv7.1_f0.0_2026-06-18.md` | 2026-06-18 | Temp/hum/press/gas, BSEC library, gas heater sequencer, I2C bus 1 |
| 20.13 | BQ25619 charger | `20.13_BQ25619_Datasheet_Extract_iv7.1_f0.0_2026-06-18.md` | 2026-06-18 | LiPo charger, fuel gauge, 5V boost (PMID), ship mode, I2C bus 2 |
| 20.14 | DRV2605L haptics | `20.14_DRV2605L_Datasheet_Extract_iv7.1_f0.0_2026-06-18.md` | 2026-06-18 | LRA haptic driver, 35 registers, auto-cal, IN/TRIG=GND, I2C bus 2 |
| 20.15 | WS2812B-2020 | `20.15_WS2812_Datasheet_Extract_iv7.1_f0.0_2026-06-18.md` | 2026-06-18 | 1-wire NZR at 800 kbps, GRB order, 5V rail, VIH marginal at 3.2V |
| 20.16 | ALPS EC05E encoder | `20.16_Encoder_Datasheet_Extract_iv7.1_f0.0_2026-06-18.md` | 2026-06-18 | Crown input, 12 PPR, 6ms bounce, PCNT + 8ms SW debounce required |
| 20.17 | Flashlight LED+FET | `20.17_Flashlight_LED_MOSFET_Extract_iv7.1_f0.0_2026-06-18.md` | 2026-06-18 | TOGIALED + BSS138W, 5V required, 94Ω series gives 13–23 mA |
| 20.18 | SDMMC socket | `20.18_SDCard_SDMMC_Extract_iv7.1_f0.0_2026-06-19.md` | 2026-06-19 | Push-push TF, 1-bit mode mandatory, 10kΩ pull-ups, CD polarity TBD |
| 20.19 | MSM261DGT003 mic | `20.19_PDM_Microphone_Extract_iv7.1_f0.0_2026-06-19.md` | 2026-06-19 | PDM 4th-order Σ-Δ, 1.8V VDD, 48kHz @ 3.072 MHz, 16kHz needs ×128 |
| 20.20 | Misc passives | `20.20_Miscellaneous_Passives_Reference_iv7.1_f0.0_2026-06-19.md` | 2026-06-19 | BLE/GPS antennas, RTC crystal, ESD diodes, ML621 backup cell, XC6206 LDO |

**Total extracts: 21 files (including 20.10b companion).**

---

## I2C bus utilization

### Bus 1 — GPIO1 (SDA), GPIO2 (SCL), 400 kHz Fast Mode

| Device | I2C address | Pull-up | Notes |
|---|---|---|---|
| PCF85063A | 0x51 | 10 kΩ to 3.2V | RTC, always on |
| VEML6030 | 0x10 (ADDR=GND) / 0x48 (ADDR=VDD) | shared | Ambient light; **avoid 0x48 if TMP117 also on 0x48** |
| LIS3MDLTR | 0x1C (SDO=GND) / 0x1E (SDO=VDD) | shared | Magnetometer |
| MAX-M10S | 0x42 | shared | GPS module |
| TMP117 | 0x48 (ADD0=GND) / 0x49–0x4B | shared | Skin temp; **avoid conflict with VEML6030 if both on 0x48** |
| LSM6DSV16X | 0x6A (SA0=GND) / 0x6B (SA0=VDD) | shared | IMU |
| MAX30101 | 0x57 (fixed) | shared | PPG heart rate |
| BME688 | 0x76 (SDO=GND) / 0x77 (SDO=VDD) | shared | Environment |
| CST9217 | 0x1A (typical) | shared | Touch controller |

**Bus 1 worst-case node count: 9 devices.** With 10 kΩ pull-ups and typical ~10 pF per stub, total C_bus ≈ 90 pF — within I2C 400 pF limit. If ESDALCL5-1BM2 ESD diodes are placed on bus lines, add 26–30 pF per protected line; verify total stays under 400 pF.

**Address conflict risk:** VEML6030 at 0x48 (ADDR=VDD) collides with TMP117 at 0x48 (ADD0=GND). Ensure address strapping places them on different addresses: VEML6030 at 0x10 (ADDR=GND) OR TMP117 at 0x49+ before assembly.

### Bus 2 — GPIO4 (SDA), GPIO5 (SCL), 400 kHz Fast Mode

| Device | I2C address | Pull-up | Notes |
|---|---|---|---|
| BQ25619 | 0x6A | 10 kΩ to 3.2V | Charger/fuel gauge |
| DRV2605L | 0x5A | 10 kΩ to 3.2V | Haptic driver |

**Bus 2 node count: 2 devices.** No bus loading concern.

---

## 5V boost rail (PMID) consumers

**Source:** BQ25619 internal boost regulator, GPIO-enabled, rated 1 A continuous.
**Constraint:** Boost and battery charging are **mutually exclusive** — boost must be disabled before plugging USB charger.

| Consumer | Peak current | Typical current | Enable control |
|---|---|---|---|
| MAX30101 IR LED (SpO2) | ~50 mA | ~15 mA | I2C register LED1/LED2 PA |
| MAX30101 Red LED (SpO2) | ~50 mA | ~15 mA | I2C register LED2 PA |
| WS2812B-2020 RGB LED | ~60 mA (full white) | ~20 mA (dim) | RMT GPIO |
| Flashlight LED (via BSS138W) | ~23 mA (Vf=2.8V) / ~13 mA (Vf=3.6V) | ~18 mA | GPIO41 via MOSFET |
| **Total worst-case (all on)** | **~183 mA** | **~70 mA** | — |

**Margin:** 183 mA worst case vs 1000 mA boost limit — large margin. No arbitration required for simultaneous use in firmware, but flashlight and charger are mutually exclusive (disable boost before charger connect).

---

## RTC GPIO wake sources

The PCF85063A INT pin and select GPIOs support deep-sleep wake. Only GPIOs in the RTC power domain can wake the ESP32-S3 from deep sleep.

| GPIO | Signal | Wake-capable | Notes |
|---|---|---|---|
| GPIO6 | BME688 INT / spare | Yes | RTC domain confirmed |
| GPIO7 | VEML6030 INT / spare | Yes | RTC domain confirmed |
| GPIO8 | TMP117 ALERT | Yes | RTC domain confirmed |
| GPIO15 | RTC_INT (PCF85063A) | Yes | Primary RTC alarm wake source |
| GPIO16 | BQ_QON button | Yes | Button wake from deep sleep |
| GPIO21 | Encoder A (EC05E) | Yes | Crown rotation wake |

**Not wake-capable (cannot wake from deep sleep):**
- GPIO38 (SD_CLK), GPIO39 (SD_CMD), GPIO40 (SD_DAT0) — no RTC
- GPIO43 (Encoder B) — no RTC wake capability
- GPIO47 (Mic_CLK), GPIO48 (Mic_Dout) — no RTC
- GPIO41 (Flashlight) — no RTC

**Deep sleep strategy:** use RTC_INT (GPIO15) as primary timer wake; GPIO16 (button) for user wake; GPIO21 (encoder) for crown-turn wake.

---

## System power budget (consolidated from all extracts)

### 3.2V main rail (TPS62840, 750 mA rated)

| Consumer | Active typical | Deep sleep |
|---|---|---|
| ESP32-S3-WROOM-1U | 30 mA (no RF); 80–240 mA (WiFi Tx peak) | 20 µA |
| CO5300 AMOLED | 40–80 mA @ full brightness | ~0 µA (SLPIN) |
| CST9217 touch | 3 mA active | 100 µA standby |
| LSM6DSV16X VDD | 0.55 mA (acc+gyro) | 3 µA (accel-only LP) |
| LIS3MDLTR VDD | 0.30 mA | 1 µA |
| TMP117 VDD | 0.14 mA (4 Hz) | 1.7 µA standby |
| VEML6030 VDD | 0.50 mA | 0.5 µA |
| DRV2605L VDD | 12 mA active (LRA driven) | 2 µA standby |
| PCF85063A VDD | 1 µA | 0.25 µA backup |
| MAX-M10S VCC | 20 mA (acquisition) | 5 µA (power-save) |
| BME688 VDDIO | 0.5 µA | <0.1 µA |
| XC6206 quiescent | 1 µA | 1 µA |
| SD card (standby) | 1–2 mA (card idling) | 0 (unmounted) |
| **3.2V total (active, no WiFi/display)** | **~70 mA** | **~25 µA** |
| **3.2V total (active, display + WiFi)** | **~350 mA peak** | — |

**Margin:** 350 mA peak vs 750 mA buck limit — adequate.

### 1.8V rail (XC6206, 80 mA rated)

| Consumer | Active typical |
|---|---|
| MAX30101 VDDA | 1.1 mA |
| BME688 VDD | 2.1 mA active |
| LSM6DSV16X V_IO | 0.7 mA |
| LIS3MDLTR VDD_IO | 0.03 mA |
| MAX-M10S V_IO | 0.5 mA |
| MSM261DGT003 mic | 0.67 mA (Standard mode) |
| **1.8V total** | **~5 mA — large margin to 80 mA** |

**Note:** XC6206 has no enable pin — 1.8V is always on when 3.2V rail is present. All 1.8V-domain sensors must self-enter low-power modes in firmware.

### 5V boost rail — see section above

### Backup rails

| Cell | Voltage | Consumer | Calculated duration |
|---|---|---|---|
| Panasonic ML621 | 3.0 V nom | PCF85063A ~0.25 µA | ~2.3 years (5 mAh / 0.25 µA) |
| 0.22 F supercap | ~2.7 V | MAX-M10S BBR ~15 µA | ~4 hours hot-start retain |

---

## Cross-v7.2 conflicts requiring doc correction

Datasheet findings that contradict or clarify the v7.2 system instructions. Each should be corrected in the next revision of `02_Kompic_Mk1_System_Instructions_v7.2.md`.

| # | Extract | Topic | v7.2 assumption | Datasheet truth | Correction |
|---|---|---|---|---|---|
| C-01 | 20.06 | VEML6030 auto-ranging | Described as a chip feature | Auto-ranging is a firmware algorithm; chip only provides ALS count + overflow bit | Delete "auto-ranging chip feature" language; document as FW algorithm |
| C-02 | 20.07 | LIS3MDLTR offset regs | Not mentioned | OFFSET_X/Y/Z registers are RAM-only — hard-iron cal must be stored in ESP NVS and reloaded each boot | Add NVS hard-iron cal note to LIS3MDLTR section |
| C-03 | 20.08 | GPS antenna part number | "Antenna-2450AT18A0100001E" listed under GPS | 2450AT18A is the BLE antenna; GPS antenna is BAT WIRELESS BWGNSCNX8-8W2 (resolved in 20.20) | Correct BOM annotation: 2450AT18A → BLE; BWGNSCNX8-8W2 → GPS |
| C-04 | 20.08 | GPS supercap backup hold | "~2 hours hot-start" | 0.22 F, ~2.7V charged, MAX-M10S BBR ~15 µA → ~4 hours (capacitor math) | Update estimate to ~4 hours (with caveat: depends on actual capacitance and leakage) |
| C-05 | 20.09 | TMP117 thermal pad | Not specified | For skin temperature use, the exposed thermal pad MUST be soldered — datasheet specs assume conducted path | Add "solder thermal pad" note to TMP117 assembly instructions |
| C-06 | 20.15 | WS2812B color order | Assumed RGB | GRB byte order (G first, then R, then B), MSB-first within each byte | Fix any driver or documentation assuming RGB order |
| C-07 | 20.15 | WS2812B supply voltage | "5V rail, 3.2V data OK" | VIH_min = 0.65×5V = 3.25 V; 3.2V GPIO output has zero margin; requires level shifter or data from 5V domain | Flag as hardware risk; recommend level shifter on DATA in next spin |
| C-08 | 20.16 | Encoder PCNT debounce | Not specified | 6ms contact bounce >> 12.8µs PCNT glitch filter max; software 8ms one-shot debounce mandatory | Add software debounce requirement to encoder firmware design |
| C-09 | 20.17 | Flashlight supply | "3.2V gate, LED on 3.2V" | LED Vf_max = 3.6V > 3.2V rail; MUST use 5V boost rail | Correct schematic/instructions: flashlight LED on 5V boost, not 3.2V |
| C-10 | 20.18 | SDMMC pull-up values | 10 kΩ typical | 10 kΩ × ~20 pF ≈ 200 ns RC — too slow for 50 MHz HS mode; use 25 MHz DS or reduce to 4.7 kΩ for HS | Document DS=25MHz as default; note pull-up reduction needed for HS |
| C-11 | 20.19 | PDM mic supply | "3.2V or 1.8V? check datasheet" | VDD = 1.6–3.6 V, tested at 1.8 V — confirmed on +1V8 rail | Confirm mic listed under +1V8 consumers (it already is) |
| C-12 | 20.20 | ML621 capacity | "5.5 mAh" | Datasheet: 5.0 mAh | Correct to 5.0 mAh in system instructions |
| C-13 | 20.20 | ML621 charge voltage | 1×1N4148 from 3.2V | 3.2V − 0.5V (Vf at µA) = 2.7V — below 2.8V guaranteed minimum | Replace 1N4148 with Schottky (BAT54) or re-evaluate circuit; CRITICAL |
| C-14 | 20.20 | RF trace width | 0.17 mm (from 0.8mm stackup) | 1mm stackup not characterised; 50Ω not guaranteed | Re-derive trace width after stackup characterisation; re-tune matching network |

---

## Open defects summary (HIGH / CRITICAL priority)

| ID | Severity | Component | Issue | Resolution |
|----|---|---|---|---|
| D-01 | CRITICAL | ML621 backup cell | Charge voltage ~2.7V < 2.8V minimum; cell may not fully charge | Replace 1N4148 with Schottky diode in next PCB spin |
| D-02 | HIGH | RF traces | 0.17mm trace width incorrect for 1mm stackup; 50Ω unverified | Re-derive after stackup characterisation |
| D-03 | HIGH | WS2812B | VIH = 3.25V vs ~3.0–3.1V on 3.2V GPIO; zero margin | Add level shifter on DATA in next spin |
| D-04 | HIGH | DRV2605L | IN/TRIG must be tied to GND (Rev B requirement); verify assembly | Check assembly drawing for IN/TRIG pulldown |
| D-05 | HIGH | SDMMC | Must enforce `sdmmc_slot_config_t.width = 1` — without it, 4-bit mode attempted on unconnected pins | Firmware: set width=1 unconditionally |
| D-06 | HIGH | PDM mic | 16kHz at ×64 decimation = 1.024 MHz dead-band; must use ×128 | Firmware: use `I2S_PDM_DSR_16S` for 16kHz |
| D-07 | HIGH | Encoder | 6ms bounce >> 12.8µs PCNT max; software 8ms debounce mandatory | Firmware: add 8ms one-shot debounce timer in encoder ISR |
| D-08 | MEDIUM | Flashlight | 5V boost must be enabled BEFORE GPIO41 asserted; charger plug-in while active requires disable boost first | Firmware: boost enable/disable sequencing |
| D-09 | MEDIUM | SDMMC | CD pin polarity undetermined; no card-detect firmware until bench verified | Bench: measure CD pin with card in/out |
| D-10 | MEDIUM | PDM mic | CLK (GPIO47, 3.3V domain) drives 1.8V mic; VIH_abs_max = 3.6V, margin = 0.3V | Verify on bring-up; consider series resistor if reliability concern |
| D-11 | MEDIUM | LIS3MDLTR | LRA magnet creates ~1G hard-iron bias; magnetometer readings unreliable without cal | Firmware: hard-iron cal routine; store in NVS; reload each boot |
| D-12 | MEDIUM | RTC crystal | HCI FC31M2 CL variant (6/9/12.5 pF) must be confirmed against BOM for correct PCB caps | Verify LCSC order code and PCB cap values |
| D-13 | MEDIUM | I2C Bus 1 | VEML6030 (0x48 if ADDR=VDD) vs TMP117 (0x48 if ADD0=GND) address collision risk | Verify address strapping on assembled board before initialising both |
| D-14 | INFO | GPS antenna | VSWR at 1575 MHz = 3.07 vs spec < 3; marginal | Monitor during GPS bring-up; may improve with body loading |

---

## Phase completion summary

| Phase | Extracts | Components | Completion |
|---|---|---|---|
| Phase 1 — Power & MCU | 20.01–20.05 | CO5300, CST9217, ESP32-S3, PCF85063A, TPS62840 | 2026-06-13 |
| Phase 2 — Sensors Bus 1 | 20.06–20.10b | VEML6030, LIS3MDLTR, MAX-M10S, TMP117, LSM6DSV16X (+advanced) | 2026-06-13 |
| Phase 3 — Sensors Bus 2 / Power | 20.11–20.13 | MAX30101, BME688, BQ25619 | 2026-06-18 |
| Phase 4 — Actuators & I/O | 20.14–20.17 | DRV2605L, WS2812B, Encoder, Flashlight+FET | 2026-06-18 |
| Phase 5 — Peripherals & Misc | 20.18–20.20 | SDMMC, PDM mic, antennas/crystal/ESD/backup | 2026-06-19 |
| **TOTAL** | **21 files** | **20 components/groups** | **2026-06-19** |

---

## Firmware bring-up checklist (derived from all extracts)

### Boot-time initialisation order (critical sequencing)

1. **TPS62840 always on** — 3.2V rail present at boot. No action.
2. **XC6206 always on** — 1.8V rail present when 3.2V is present. No action.
3. **BQ25619 I2C init** (Bus 2, 0x6A) — read REG_STATUS (0x08) for PG_STAT; configure OTG/boost if needed.
4. **PCF85063A I2C init** (Bus 1, 0x51) — check OS bit in Seconds register; if set, RTC lost power, re-set time.
5. **LSM6DSV16X I2C init** (Bus 1, 0x6A/6B) — verify WHO_AM_I=0x70; configure CTRL1/CTRL2, INT1.
6. **LIS3MDLTR I2C init** (Bus 1, 0x1C/1E) — configure continuous mode; reload hard-iron offsets from NVS.
7. **MAX30101 I2C init** (Bus 1, 0x57) — write REG_MODE_CONFIG=0x40 (reset); configure SpO2 mode.
8. **BME688 I2C init** (Bus 1, 0x76/77) — use BSEC library; configure gas heater sequencer.
9. **TMP117 I2C init** (Bus 1, 0x48+) — configure 1 Hz conversion; set alert thresholds.
10. **VEML6030 I2C init** (Bus 1, 0x10) — configure ALS gain and integration time.
11. **DRV2605L I2C init** (Bus 2, 0x5A) — set GO=0; mode=5 (RT playback) or mode=0 (internal); LRA library=6; verify auto-cal results or re-calibrate.
12. **MAX-M10S I2C init** (Bus 1, 0x42) — configure UBX protocol; set power mode; configure 1PPS.
13. **SD card mount** (SDMMC, GPIO38/39/40) — `sdmmc_slot_config_t.width = 1`; mount on demand only.
14. **PDM mic** (I2S PDM RX, GPIO47/48) — enable I2S peripheral with 3.072 MHz CLK → 48 kHz PCM; discard first 20 ms.
15. **CO5300 display** (QSPI, GPIO35/36/37/10/11/12) — apply power-on sequence; clear GRAM; send SLPOUT.
16. **CST9217 touch** (I2C Bus 1) — configure gesture mode; enable INT.
17. **WS2812B** (RMT, GPIO9) — enable 5V boost first; GRB color order; RESET ≥ 280 µs between frames.
18. **DRV2605L auto-cal** — perform on first boot or after LRA replacement; store BEMF results in NVS.

### Sleep entry sequence

1. Flush and unmount SD card filesystem (FAT32 has no journaling).
2. Disable WS2812B (stop RMT; hold DATA low ≥ 280 µs).
3. Disable 5V boost (BQ25619 OTG_CONFIG=0) — only if not charging.
4. Stop I2S PDM clock (mic enters sleep ≤ 30 µs, draws 1 µA).
5. Place MAX-M10S in power-save mode.
6. Place BME688, LSM6DSV16X, LIS3MDLTR, TMP117, VEML6030 in sleep/standby.
7. MAX30101: write MODE_CONFIG reset or set SHDN bit.
8. Set ESP32-S3 deep sleep wake sources: GPIO15 (RTC_INT), GPIO16 (button), GPIO21 (encoder A).
9. `esp_deep_sleep_start()`.

---

*20.21 — End of checklist. All datasheet extracts complete for Kompic Mk I iv7.1 / f0.0.*
