porupski/kompic-wearable/firmware/docs/datasheet_extracts/20.14_DRV2605L_Datasheet_Extract_iv7.1_f0.0_2026-06-18.md

# 20.14 — DRV2605L DATASHEET EXTRACT
**Date:** 2026-06-18 · **Datasheet:** drv2605l.pdf · **Pages:** 68 total · **Hardware:** iv7.1 · **Firmware porting:** f0.0
**Parsed by:** Claude Code Sonnet 4.6

---

## Cross-reference vs v7.2

| Item | v7.2 / System Instructions claim | Datasheet says | Status |
|---|---|---|---|
| I2C address | 0x5A | 0x5A (7-bit), binary 1011010 [p. 25] | ✓ CONFIRMED |
| Bus | I2C bus 2, SDA=GPIO4, SCL=GPIO5, 400 kHz | Max SCL = 400 kHz [p. 7] | ✓ CONFIRMED |
| DRV_EN on GPIO0 | Yes; internal pull-up is boot-only, must drive as FW output | EN is active-high, device is in shutdown when EN=LOW [p. 21] | ✓ CONFIRMED — FW must drive GPIO0 HIGH as a GPIO output; boot pull-up alone will not hold EN reliably after ROM bootloader releases the strap |
| LRA motor: ELV1411A | LRA type assumed | DRV2605L supports both ERM and LRA; N_ERM_LRA=1 selects LRA [p. 12, 46] | ✓ CONFIRMED — LRA supported |
| No INT GPIO assigned | No DRV2605L INT in pinout | The device has no dedicated INT output pin — status is polled via STATUS register 0x00. INTRIG/IN_TRIG (ball B1) serves as external trigger input only in I2C mode. [p. 4–5, 36] | ✓ CONFIRMED — no INT GPIO needed |
| CST9217 touch address 0x5A on bus 1 | 0x5A on bus 1 | DRV2605L is also 0x5A — but on bus 2. No conflict since they are on different I2C buses. | INFO — no conflict |

---

## Pinout (summary)

### DSBGA 9-pin YZF Package

| Ball | Name | Type | Function | Notes |
|---|---|---|---|---|
| A1 | EN | I | Device enable. Active HIGH. Logic low = shutdown. | [p. 4] |
| A2 | REG | O | 1.8V internal regulator output. Requires 1 µF cap to GND. Do NOT load externally. | [p. 4] |
| A3 | OUT+ | O | Positive differential haptic output | [p. 4] |
| B1 | IN/TRIG | I | PWM / analog / external trigger input. **Tie to GND if unused.** | [p. 4, Rev B] |
| B2 | SDA | I/O | I2C data | [p. 4] |
| B3 | GND | P | Supply ground | [p. 4] |
| C1 | SCL | I | I2C clock | [p. 4] |
| C2 | VDD | P | Supply input 2–5.2 V. Requires 1 µF cap to GND. | [p. 4] |
| C3 | OUT- | O | Negative differential haptic output | [p. 4] |

**Critical:** IN/TRIG must be tied to GND if unused [p. 4, Revision B changelog]. Verify PCB schematic.

---

## I2C / Bus

| Parameter | Value | Source |
|---|---|---|
| I2C slave address (7-bit) | 0x5A (binary 1011010) | [p. 25] |
| 8-bit write address | 0xB4 | [p. 26] |
| 8-bit read address | 0xB5 | [p. 26] |
| Address configurable? | No — fixed, no address pin | [p. 25] |
| Max SCL frequency | 400 kHz | [p. 7] |
| VIH threshold | 1.3 V min | [p. 6] |
| VIL threshold | 0.5 V max | [p. 6] |
| Pull-up requirement | External pull-ups required; 660 Ω to 4.7 kΩ recommended | [p. 25] |
| Pull-ups in Kompic | 5.1 kΩ to 3V3 (bus 2, per System Instructions) | System Instructions |
| I2C Watchdog Timer | Resets I2C protocol after 4.33 ms bus hang in active mode. Does NOT function in standby — bus hang in standby requires power-cycle. | [p. 19] |
| Bus assignment | Bus 2 (SDA=GPIO4, SCL=GPIO5) | System Instructions |

---

## Registers (firmware-critical)

### Full Register Map (0x00–0x22)

| Addr | Default | Bit 7 | Bit 6 | Bit 5 | Bit 4 | Bit 3 | Bit 2 | Bit 1 | Bit 0 | Page |
|---|---|---|---|---|---|---|---|---|---|---|
| 0x00 | 0xE0 | DEVICE_ID[2] | DEVICE_ID[1] | DEVICE_ID[0] | Reserved | DIAG_RESULT | Reserved | OVER_TEMP | OC_DETECT | p. 35–36 |
| 0x01 | 0x40 | DEV_RESET | STANDBY | Reserved | Reserved | Reserved | MODE[2] | MODE[1] | MODE[0] | p. 35, 37 |
| 0x02 | 0x00 | RTP_INPUT[7:0] | | | | | | | | p. 38 |
| 0x03 | 0x01 | Reserved | Reserved | Reserved | HI_Z | Reserved | LIBRARY_SEL[2] | LIBRARY_SEL[1] | LIBRARY_SEL[0] | p. 38 |
| 0x04 | 0x01 | WAIT1 | WAV_FRM_SEQ1[6:0] | | | | | | | p. 35, 39 |
| 0x05 | 0x00 | WAIT2 | WAV_FRM_SEQ2[6:0] | | | | | | | p. 35, 39 |
| 0x06 | 0x00 | WAIT3 | WAV_FRM_SEQ3[6:0] | | | | | | | p. 35 |
| 0x07 | 0x00 | WAIT4 | WAV_FRM_SEQ4[6:0] | | | | | | | p. 35 |
| 0x08 | 0x00 | WAIT5 | WAV_FRM_SEQ5[6:0] | | | | | | | p. 35 |
| 0x09 | 0x00 | WAIT6 | WAV_FRM_SEQ6[6:0] | | | | | | | p. 35 |
| 0x0A | 0x00 | WAIT7 | WAV_FRM_SEQ7[6:0] | | | | | | | p. 35 |
| 0x0B | 0x00 | WAIT8 | WAV_FRM_SEQ8[6:0] | | | | | | | p. 35 |
| 0x0C | 0x00 | — | — | — | — | — | — | — | GO | p. 35, 39 |
| 0x0D | 0x00 | ODT[7:0] (Overdrive Time Offset, signed) | | | | | | | | p. 40 |
| 0x0E | 0x00 | SPT[7:0] (Sustain Time Offset Positive, signed) | | | | | | | | p. 40 |
| 0x0F | 0x00 | SNT[7:0] (Sustain Time Offset Negative, signed) | | | | | | | | p. 41 |
| 0x10 | 0x00 | BRT[7:0] (Brake Time Offset, signed) | | | | | | | | p. 41 |
| 0x11 | 0x05 | — | — | — | — | ATH_PEAK_TIME[1] | ATH_PEAK_TIME[0] | ATH_FILTER[1] | ATH_FILTER[0] | p. 42 |
| 0x12 | 0x19 | ATH_MIN_INPUT[7:0] | | | | | | | | p. 42 |
| 0x13 | 0xFF | ATH_MAX_INPUT[7:0] | | | | | | | | p. 42 |
| 0x14 | 0x19 | ATH_MIN_DRIVE[7:0] | | | | | | | | p. 43 |
| 0x15 | 0xFF | ATH_MAX_DRIVE[7:0] | | | | | | | | p. 43 |
| 0x16 | 0x3E | RATED_VOLTAGE[7:0] | | | | | | | | p. 44 |
| 0x17 | 0x8C | OD_CLAMP[7:0] | | | | | | | | p. 44 |
| 0x18 | 0x0C | A_CAL_COMP[7:0] (auto-cal result) | | | | | | | | p. 44 |
| 0x19 | 0x6F | A_CAL_BEMF[7:0] (auto-cal result) | | | | | | | | p. 45 |
| 0x1A | 0x36 | N_ERM_LRA | FB_BRAKE_FACTOR[2] | FB_BRAKE_FACTOR[1] | FB_BRAKE_FACTOR[0] | LOOP_GAIN[1] | LOOP_GAIN[0] | BEMF_GAIN[1] | BEMF_GAIN[0] | p. 46 |
| 0x1B | 0x93 | STARTUP_BOOST | — | AC_COUPLE | DRIVE_TIME[4] | DRIVE_TIME[3] | DRIVE_TIME[2] | DRIVE_TIME[1] | DRIVE_TIME[0] | p. 47 |
| 0x1C | 0xF5 | BIDIR_INPUT | BRAKE_STABILIZER | SAMPLE_TIME[1] | SAMPLE_TIME[0] | BLANKING_TIME[1] | BLANKING_TIME[0] | IDISS_TIME[1] | IDISS_TIME[0] | p. 48–50 |
| 0x1D | 0xA0 | NG_THRESH[1] | NG_THRESH[0] | ERM_OPEN_LOOP | SUPPLY_COMP_DIS | DATA_FORMAT_RTP | LRA_DRIVE_MODE | N_PWM_ANALOG | LRA_OPEN_LOOP | p. 51 |
| 0x1E | 0x20 | ZC_DET_TIME[1] | ZC_DET_TIME[0] | AUTO_CAL_TIME[1] | AUTO_CAL_TIME[0] | — | OTP_STATUS | — | OTP_PROGRAM | p. 52 |
| 0x1F | 0x80 | AUTO_OL_CNT[1] | AUTO_OL_CNT[0] | LRA_AUTO_OPEN_LOOP | PLAYBACK_INTERVAL | BLANKING_TIME[3] | BLANKING_TIME[2] | IDISS_TIME[3] | IDISS_TIME[2] | p. 53 |
| 0x20 | 0x33 | — | OL_LRA_PERIOD[6:0] | | | | | | | p. 53 |
| 0x21 | 0x00 | VBAT[7:0] (read-only voltage monitor) | | | | | | | | p. 53–54 |
| 0x22 | 0x00 | LRA_PERIOD[7:0] (read-only live resonance period) | | | | | | | | p. 54 |

---

### STATUS — 0x00 [p. 35–36]

| Bits | Field | Description |
|---|---|---|
| 7:5 | DEVICE_ID[2:0] | **7 = DRV2605L** (low-voltage). Read at startup to confirm device identity. |
| 3 | DIAG_RESULT | 0=pass; 1=fail/fault. Valid only after GO self-clears. Clears on read. |
| 1 | OVER_TEMP | Latching over-temperature flag. Clears on read. |
| 0 | OC_DETECT | Latching overcurrent flag. Clears on read. |

### MODE — 0x01 [p. 35, 37]

| Bits | Field | Description |
|---|---|---|
| 7 | DEV_RESET | Software reset, all registers to defaults. Self-clears. |
| 6 | STANDBY | 1=low-power standby (retains regs, allows I2C). 0=active. **Default=1 at powerup.** |
| 2:0 | MODE[2:0] | 0=Internal trigger (GO bit); 1=External trigger edge; 2=External trigger level; 3=PWM/analog; 4=Audio-to-vibe; **5=RTP real-time**; 6=Diagnostics; **7=Auto-calibration** |

### LIBRARY_SEL — 0x03 [p. 38]

| Bits | Field | Description |
|---|---|---|
| 4 | HI_Z | Forces OUT+/OUT- to true high-impedance immediately. |
| 2:0 | LIBRARY_SEL[2:0] | 0=Empty; 1=Library A (ERM open-loop only); 2–5=Libraries B–E (ERM); **6=LRA Library (use for ELV1411A)**; 7=Library F (ERM) |

### GO — 0x0C [p. 35, 39]

| Bits | Field | Description |
|---|---|---|
| 0 | GO | Write 1 to trigger waveform sequence (MODE=0) or calibration (MODE=7). Self-clears on completion. Clearing during playback cancels immediately. |

**WAIT bit in sequencer (0x04–0x0B):** Bit 7=1 means lower 7 bits are a delay (×10 ms) instead of an effect ID. [p. 16, 39]

### FEEDBACK_CTRL — 0x1A [p. 46]

| Bits | Field | Description |
|---|---|---|
| 7 | N_ERM_LRA | **0=ERM; 1=LRA.** Must be set before calibration. Set to 1 for ELV1411A. |
| 6:4 | FB_BRAKE_FACTOR[2:0] | Braking gain. 0=1×; 1=2×; **2=3× (recommended for calibration)**; 3=4×; 4=6×; 5=8×; 6=16×; 7=disabled |
| 3:2 | LOOP_GAIN[1:0] | 0=Low; 1=Medium; **2=High (recommended for calibration)**; 3=Very High |
| 1:0 | BEMF_GAIN[1:0] | LRA: 0=3.75×; 1=7.5×; **2=15×**; 3=22.5×. Auto-cal overwrites this. |

### CTRL1 — 0x1B [p. 47]

| Bits | Field | Description |
|---|---|---|
| 7 | STARTUP_BOOST | 1=higher loop gain during overdrive for faster start (default, keep). |
| 4:0 | DRIVE_TIME[4:0] | LRA: initial resonant freq guess. t_drive(ms) = DRIVE_TIME × 0.1 + 0.5. Optimum ≈ 0.5/f_LRA. **Example: f=200 Hz → DRIVE_TIME=20=0x14** |

### CTRL2 — 0x1C [p. 48–50]

| Bits | Field | Description |
|---|---|---|
| 7 | BIDIR_INPUT | 1=Bidirectional input (required for ROM library effects, keep). |
| 6 | BRAKE_STABILIZER | 1=enabled (default, keep). |
| 5:4 | SAMPLE_TIME[1:0] | LRA back-EMF sample time. **3=300 µs (recommended)**. |
| 3:2 | BLANKING_TIME[1:0] | LSBs. **1=25 µs (recommended)**. |
| 1:0 | IDISS_TIME[1:0] | LSBs. **1=25 µs (recommended)**. |

### CTRL3 — 0x1D [p. 51]

| Bits | Field | Description |
|---|---|---|
| 0 | LRA_OPEN_LOOP | **0=auto-resonance closed-loop (default)**. Keep 0. |

### RATED_VOLTAGE — 0x16 [p. 44]

Sets full-scale reference voltage. Must be written before calibration.

```
RATED_VOLTAGE = V_rated_RMS / 20.58e-3
Example: 1.0 V_RMS → 1.0 / 0.02058 ≈ 49 = 0x31
```

(Simplified; use full formula from p. 44 with SAMPLE_TIME correction for accuracy.)

### OD_CLAMP — 0x17 [p. 44]

Maximum overdrive/clamp voltage. Must be > RATED_VOLTAGE. Typical: 1.5–2× RATED_VOLTAGE.

```
V_clamp(V) = 21.22e-3 × OD_CLAMP
Example: If RATED_VOLTAGE=0x31 (49), OD_CLAMP = 0x4A–0x62 gives 1.5–2× headroom
```

---

## Initialization sequence

### LRA mode with auto-calibration

```
1. Wait ≥ 250 µs after VDD ramp-up.                                    [p. 59]
2. Drive GPIO0 HIGH (EN). Wait ≥ 1.5 ms for device ready.              [p. 6–7]
3. Write 0x07 to 0x01  — exit standby, enter calibration mode.         [p. 29, 37]
4. Write 0x1A = 0xB6   — N_ERM_LRA=1, FB_BRAKE_FACTOR=3x, LOOP_GAIN=High, BEMF_GAIN=15x
5. Write RATED_VOLTAGE to 0x16  — motor-specific, see formula above.   [p. 29, 44]
6. Write OD_CLAMP to 0x17      — motor-specific, see formula above.    [p. 29, 44]
7. Write 0x1E = 0x30   — AUTO_CAL_TIME=3 (1000–1200 ms, most accurate) [p. 29, 52]
8. Write 0x1B per DRIVE_TIME calculation — initial resonant freq guess. [p. 29, 47]
9. Write 0x01 to 0x0C  — GO=1, start calibration.                      [p. 29]
10. Poll 0x0C until GO=0 (calibration complete, ~1200 ms max).         [p. 29]
11. Read 0x00: if DIAG_RESULT (bit3) = 0 → PASS. If 1 → FAIL,
    check register values and retry.                                    [p. 29, 36]
12. Write 0x00 to 0x01  — STANDBY=0, MODE=0 (internal trigger).        [p. 29, 37]
13. Write 0x06 to 0x03  — LIBRARY_SEL=6 (LRA library).                 [p. 38]
14. (Optional) Store 0x18 (A_CAL_COMP) and 0x19 (A_CAL_BEMF)
    to ESP32 NVS for restore on next boot.                              [p. 28–29]
```

### Subsequent boot (NVS calibration restore)

```
1. Wait 250 µs. Drive GPIO0 HIGH. Wait 1.5 ms.
2. Write 0x07 to 0x01  — exit standby.
3. Restore 0x1A, 0x16, 0x17 with motor values.
4. Restore stored A_CAL_COMP to 0x18, A_CAL_BEMF to 0x19.
5. Write 0x00 to 0x01  — MODE=0 internal trigger.
6. Write 0x06 to 0x03  — LRA library.
```

---

## Waveform library (ROM effects — LRA subset)

**LIBRARY_SEL = 6** for all LRA use. Effect IDs 1–123; 0 = end of sequence. [p. 38]

**Note:** Individual LRA effect names are licensed Immersion TS2200 content — not reproduced in the datasheet. Table below reflects commonly documented effect conventions. Characterise on bench with ELV1411A to confirm feel. [datasheet silent; p. 15]

| ID | Effect name | Approx duration | Notes |
|---|---|---|---|
| 1 | Strong Click — 100% | ~5–10 ms | UI confirmation, button press |
| 2 | Strong Click — 60% | ~5–10 ms | Lighter confirmation |
| 3 | Strong Click — 30% | ~5–10 ms | Subtle tap |
| 4 | Sharp Click — 100% | ~5 ms | Crisp UI tap |
| 7 | Soft Bump — 100% | ~10 ms | Alert notification |
| 10 | Double Click — 100% | ~50 ms | Double-tap confirm |
| 11 | Double Click — 60% | ~50 ms | — |
| 12 | Triple Click — 100% | ~80 ms | Triple-tap |
| 14 | Strong Buzz — 100% | ~100 ms | Alert / alarm |
| 16 | 750 ms Alert — 100% | ~750 ms | Long alarm |
| 17 | 1000 ms Alert — 100% | ~1000 ms | Extended alarm |
| 47 | Pulse — 100% | ~150 ms | Heartbeat single pulse |
| 49 | Transition Click — 100% | ~50 ms | Crown turn feedback |
| 51 | Transition Hum — 100% | ~300 ms | Continuous scroll feel |
| 56 | Pulsing Strong — 100% 1 Hz | ~1000 ms | Heartbeat 60 bpm simulation |
| 69 | Short Double Click — 100% | ~30 ms | Compact double-tap |

**Sequence trigger example (double-click):**
```c
i2c_write(0x04, 0x0A);  // WAV_FRM_SEQ1 = effect 10
i2c_write(0x05, 0x00);  // end of sequence
i2c_write(0x0C, 0x01);  // GO
```

**Sequence with wait (heartbeat — two pulses 300 ms apart):**
```c
i2c_write(0x04, 0x2F);  // effect 47
i2c_write(0x05, 0x9E);  // WAIT=1, delay = 0x1E × 10 ms = 300 ms
i2c_write(0x06, 0x2F);  // effect 47 again
i2c_write(0x07, 0x00);  // end
i2c_write(0x0C, 0x01);  // GO
```

---

## Operation

### Internal trigger (MODE=0)
Write effect IDs to 0x04–0x0B, write GO=1 (0x0C). Starts within 0.7 ms [p. 7]. GO self-clears on completion. [p. 33, 39]

### Real-Time Playback (MODE=5)
Write 0x05 to 0x01, then continuously write amplitude to 0x02 (RTP_INPUT). Signed by default: 0x7F=full+, 0x00=zero, 0x81=full−. Useful for streaming custom waveforms from PPG data. [p. 33, 38]

### LRA resonance monitor
Read 0x22 (LRA_PERIOD) during active playback to get live resonant period:
```
f_LRA (Hz) = 1 / (LRA_PERIOD[7:0] × 98.46 µs)   [p. 12, 54]
```

---

## Power consumption

| State | Condition | Typical | Maximum | Unit | Source |
|---|---|---|---|---|---|
| Shutdown | EN=0 V | 4 | 7 | µA | [p. 7] |
| Standby | EN=1.8 V, STANDBY=1 | 4.1 | 7 | µA | [p. 7] |
| Active quiescent | STANDBY=0, no signal | 0.5 | 0.65 | mA | [p. 7] |
| Active driving LRA (no load) | Duty 90%, LRA mode | 2.4 | 3.5 | mA | [p. 7] |
| Active driving ERM (no load) | Duty 90%, ERM mode | 2.3 | 3.5 | mA | [p. 7] |
| Full vibration, ERM load | RL=10Ω+100µH, 1.3V, VDD=3.6V | ~70–75 | — | mA | [p. 10, Fig. 10] |

**θJA (DSBGA):** 145.2 °C/W [p. 6]. At ~260 mW peak (full LRA load), ΔTj ≈ 37 °C — monitor OVER_TEMP bit (0x00 bit 1) during stress testing in sealed enclosure.

---

## Datasheet notes

- DEVICE_ID = 7 (0b111). Always verify at startup — DRV2605 (non-L) returns ID=3. [p. 36]
- Auto-calibration results (0x18 A_CAL_COMP, 0x19 A_CAL_BEMF) should be stored in NVS and restored each boot to avoid the 1.2 s calibration delay. [p. 28–29]
- OTP programming (registers 0x16–0x1A) requires VDD 4.0–4.4 V and is one-time irreversible. [p. 29]
- I2C watchdog: 4.33 ms in active mode. In standby, bus hang needs power-cycle to recover. [p. 19]
- Brownout protection: VDD ramp rate must exceed 3.6 kV/s for clean reset. [p. 20]
- Output PWM is trinary-modulated at 20.5 kHz; no external filter or ferrite needed. [p. 1, 7, 18]
- 1 µF (X5R/X7R) required on VDD and REG pins; 0.1 µF low-ESR on VDD recommended. [p. 57]
- IN/TRIG must be tied to GND if unused (added in Revision B). [p. 4]
- STANDBY immediately stops any playing waveform. [p. 21]
- LRA auto-resonance tracks motor frequency in real-time without requiring re-calibration. [p. 12]
- Device auto-switches to open-loop if back-EMF is not detected (e.g., motor unplugged). [p. 12]

---

## Warnings & Errata

| ID | Title | Impact | Notes |
|---|---|---|---|
| W-01 | GPIO0 (DRV_EN) boot pull-up releases after ROM bootloader | HIGH | Boot pull-up does not persist at runtime. FW must explicitly configure GPIO0 as output and drive HIGH before any I2C access. [System Instructions; p. 21] |
| W-02 | IN/TRIG must be grounded if unused | MEDIUM | Floating IN/TRIG can cause unintended actuator drive. Verify PCB schematic has IN/TRIG (ball B1) tied to GND. [p. 4, Rev B] |
| W-03 | RATED_VOLTAGE and OD_CLAMP must be written before calibration | HIGH | Running calibration with default values targets wrong voltage for ELV1411A. Always write motor-specific values first. [p. 24, 29] |
| W-04 | Library A incompatible with closed-loop bidirectional mode | MEDIUM | Default LIBRARY_SEL=1 (Library A) at powerup — must be changed to 6 for LRA. [p. 32, 38] |
| W-05 | OTP is one-time, irreversible | MEDIUM | Only program OTP after thorough bench validation. Requires 4.0–4.4 V VDD temporarily. [p. 29] |
| W-06 | Standby mode: I2C watchdog inactive | LOW | Bus hang in standby requires power-cycle. Ensure I2C transactions complete before asserting STANDBY. [p. 19] |
| W-07 | Slow VDD ramp (<3.6 kV/s) → unknown device state | LOW | Relevant at deep-discharge recovery. Require power-cycle with fast ramp to recover. [p. 20] |
| W-08 | No published LRA effect list in datasheet | LOW | LRA ROM effect names/durations are licensed TS2200 content. Characterise effects empirically at bring-up. [p. 15] |
| W-09 | ELV1411A resonant frequency unknown | HIGH | f_LRA and V_rated_RMS are required to compute RATED_VOLTAGE and DRIVE_TIME. Source ELV1411A datasheet or measure on bench before finalising calibration registers. [datasheet silent] |
| W-10 | CST9217 and DRV2605L share address 0x5A | INFO | No conflict (separate buses). Do not accidentally address across bus boundaries. |

---

## Open questions

1. **ELV1411A parameters:** Rated voltage (V_RMS), resonant frequency (Hz), coil impedance (Ω) — required for RATED_VOLTAGE and DRIVE_TIME. Source datasheet or measure.
2. **IN/TRIG PCB connection:** Is ball B1 tied to GND on the Kompic Mk I PCB? Verify in KiCad schematic. If floating, a hardware fix is needed before bring-up.
3. **LRA effect ID characterisation:** After hardware bring-up, iterate through IDs 1–123 with ELV1411A and log feel + duration for a firmware effect table.
4. **Auto-calibration vs NVS restore strategy:** Run calibration on every cold boot (~1.2 s delay) or only when NVS is empty? OTP option requires temporary 4.0–4.4 V boost — available in factory test?
5. **RTP streaming latency:** End-to-end latency from PPG beat detection to haptic output. 0.7 ms GO start-up + I2C bus time are datasheet floors; scheduling latency needs measurement.
6. **DRV_EN during deep sleep:** GPIO0 can retain output state in RTC domain. Decide whether to hold EN=HIGH (retain standby, 4 µA) or EN=LOW (full shutdown, 4 µA shutdown) during deep sleep. No functional difference in current at those levels but shutdown drops register state and requires full re-init on wake.

---

*20.14 — End of extract.*
