porupski/kompic-wearable/firmware/docs/datasheet_extracts/20.15_WS2812_Datasheet_Extract_iv7.1_f0.0_2026-06-18.md

# 20.15 — WS2812B-2020 DATASHEET EXTRACT
**Date:** 2026-06-18 · **Datasheet:** Worldsemi WS2812B-2020.pdf · **Pages:** 10 total · **Hardware:** iv7.1 · **Firmware porting:** f0.0
**Parsed by:** Claude Code Sonnet 4.6

---

## Cross-reference vs iv7.1

| Spec | iv7.1 says | Datasheet says | Match? | Action |
|---|---|---|---|---|
| GPIO for data line | GPIO42 (Sig_LED_Din) | N/A — no GPIO recommendation | N/A | Use GPIO42 as planned |
| Power rail | 5V PMID (BQ25619 boost) | VDD = 5V nominal; rated 5V; max 7V absolute | ✓ | 5V PMID is correct |
| Series resistor on DIN | 47Ω (BOM summary) | Not specified; common practice | N/A | 47Ω is reasonable; datasheet silent [p. 5] |
| Number of LEDs | Single indicator LED | Cascade supported, no count limit | N/A | Single pixel — no cascade needed |
| Data line voltage | 3.3V ESP32-S3 output | VIH = 0.65×VDD = 0.65×5 = **3.25V** minimum | **✗ MARGINAL** | See Logic Level section — action required |
| Protocol peripheral | RMT (ESP32-S3) | Single-wire NZR, 800 Kbps | ✓ | RMT is correct choice |

---

## Pinout (summary)

4-pin package [p. 2, p. 3]:

| Pin | Symbol | Function |
|---|---|---|
| 1 | DO | Control data signal output (cascade to next LED DI) |
| 2 | GND | Data & power ground |
| 3 | DI | Control data signal input |
| 4 | VDD | LED power supply — connect to +5V |

Polarity mark at DI/GND corner (pin 3/pin 2 corner) [p. 2]. PCB pad: 0.70 mm wide × 0.40 mm high, pitch 1.13 mm between pad columns [p. 2].

---

## Protocol — RMT Timing (CRITICAL)

Source: "Data Transfer Time" table [p. 4] and timing diagram [p. 5].

| Symbol | Description | Min | Typ | Max | Unit |
|---|---|---|---|---|---|
| T0H | 0-bit high time | 220 | — | 380 | ns |
| T0L | 0-bit low time | 580 | — | 1000 | ns |
| T1H | 1-bit high time | 580 | — | 1000 | ns |
| T1L | 1-bit low time | 580 | — | 1000 | ns |
| TRESET (RES) | Frame unit, low voltage (reset/latch) | 280 | — | — | µs |

Constraint [p. 4]: T0H+T0L ≥ 1.25 µs and T1H+T1L ≥ 1.25 µs. Nominal 800 Kbps [p. 1].

Reset note [p. 1]: "RESET time > 280 µs — won't cause wrong reset while interruption." Use ≥ 300 µs in RMT driver for margin.

Recommended RMT values (ESP32-S3, APB 80 MHz): T0H=300ns, T0L=900ns, T1H=750ns, T1L=600ns, RESET=300µs low.

---

## Data format

Source: "Composition of 24bit data" [p. 5].

- **Bits per LED:** 24 bits
- **Color order: GRB** — G7..G0 first, R7..R0 second, B7..B0 third [p. 5]
- **Bit order: MSB first** — "high bit data at first" [p. 5]
- **Gray levels:** 256 per channel, 8-bit [p. 1]

**Firmware:** To set color (R, G, B), transmit bytes [G, R, B] MSB-first. G and R are swapped vs natural RGB byte order.

---

## Power consumption

Source: LED Characteristics table [p. 4].

| State | Condition | Current | Source |
|---|---|---|---|
| Quiescent / off | VDD=5V, DIN idle | < 0.6 mA | [p. 4] |
| Red only, working | VDD=5V, 12 mA/channel | 12 mA | [p. 4] |
| Green only, working | VDD=5V, 12 mA/channel | 12 mA | [p. 4] |
| Blue only, working | VDD=5V, 12 mA/channel | 12 mA | [p. 4] |
| Full white (255,255,255) | VDD=5V, all channels | 36 mA | [p. 4] |

Full white = 36 mA × 5V = 180 mW. Trivial against BQ25619 PMID 1A boost rating. Per-channel current at full 8-bit drive is factory-fixed internally; the 12 mA figure is the datasheet brightness test condition, not an external set point [datasheet silent on actual drive current — recommend bench measurement].

---

## Logic level compatibility

Source: Electrical Characteristics [p. 3].

| Parameter | Symbol | Value | Unit |
|---|---|---|---|
| VIH minimum | VIH | **0.65 × VDD = 3.25V** | V |
| VIL maximum | VIL | 0.7V | V |

**ESP32-S3 GPIO42 VOH ≈ 2.9–3.1V** from the 3.2V TPS62840 rail (Kompic runs 3.2V, not 3.3V). This is **below VIH(min) = 3.25V. Zero margin. INCOMPATIBLE as-is.**

Recommended fix: add a 3.3V→5V single-channel level shifter (e.g. SN74LVC1T45, SOT-363) on the DIN line. Flag for v7.2 schematic correction. Alternatively bench-verify explicitly — if it works in practice with the 47Ω series resistor, document it, but do not assume.

---

## Electrical / Absolute maximums

Source: [p. 3, p. 1].

| Parameter | Symbol | Ratings | Unit |
|---|---|---|---|
| Power supply voltage (operating) | VDD | +3.7 to +5.3 | V |
| Power supply voltage (static, DIN idle) | VDD | up to 12V | V |
| Logical input voltage | VI | −0.3V to VDD+0.7V | V |
| Reverse connection | — | Not damaged | — |

Operating temperature range: **[datasheet silent — not stated. Assume commercial −20°C to +70°C; bench-test at 37°C for wearable.]**

Port refresh frequency (internal PWM): 2 kHz [p. 1].

---

## Package dimensions

Source: [p. 2, p. 7].

| Dimension | Value | Unit |
|---|---|---|
| Package body (L × W) | 2.00 × 2.00 | mm |
| Package height (seated) | 0.84 | mm |
| Pad standoff | 0.28 | mm |
| Pad width | 0.70 | mm |
| Pad height | 0.40 | mm |
| Pad column pitch | 1.13 | mm |
| Carrier tape pocket A0 × B0 × K0 | 2.20 × 2.40 × 1.01 | mm |

---

## Datasheet notes

1. **No filter capacitor needed** [p. 1]: Datasheet explicitly states no bypass cap required on VDD. A 100nF cap is harmless if placed anyway.
2. **Reverse polarity protection** [p. 1]: IC survives reversed VDD. VDD can withstand 12V in static state.
3. **Signal reshaping** [p. 1, p. 5]: Each pixel reshapes and re-drives DO. For single LED, DO is NC.
4. **MSL 5a** [p. 8]: Workshop life 24 hours after unpacking at ≤30°C/60%RH. Bake before reflow (70–75°C × ≥24h whole reel, or 120°C × 4h bulk).
5. **Reflow profile** [p. 9]: Lead-free. Peak 245°C, reflow 45–90s, liquid region above 217°C. Compatible with standard board fab profile.
6. **Datasheet version V1.5**, revised 2022-08-23 [p. 10].

---

## Warnings & Errata

| ID | Title | Impact | Notes |
|---|---|---|---|
| W-01 | 3.3V logic MARGINAL for DIN VIH | HIGH | VIH(min)=3.25V; ESP32-S3 VOH from 3.2V rail ≈2.9–3.1V. No margin. Add level shifter or bench-verify. Flag for v7.2. |
| W-02 | MSL 5a — 24h workshop life | MEDIUM | Bake LED before reflow. Do not leave reel open >24h. |
| W-03 | GRB color order, not RGB | MEDIUM | Driver must send [G, R, B] bytes MSB-first. RGB byte order will silently swap red and green. |
| W-04 | Operating temperature not specified | LOW | No Tmin/Tmax in datasheet. Wearable at ~37°C is within any reasonable range. |
| W-05 | No decoupling cap required | INFO | Explicitly stated in datasheet. 100nF is harmless if placed. |

---

## Open questions

1. **Level shifter on DIN:** Does v7.2 schematic include a 3.3V→5V translator on WS2812 DIN? If not, add to BOM (SN74LVC1T45 or equivalent). Verify before finalising v7.2.
2. **Actual per-channel drive current:** Datasheet gives 12 mA as test condition, not a hard spec. Measure on bench at VDD=5V, full white, to confirm battery budget figure.
3. **PMID boost sequencing:** BQ25619 PMID boost and charger are mutually exclusive. Firmware must enable boost before activating the LED and coordinate with charging state. Not a WS2812B issue but gates LED use.
4. **LED brightness for indicator:** At full white/36 mA the LED will be intensely bright at wrist distance. Plan to use PWM values of ~5–30/255 for normal indicator use. Calibrate at bring-up.
5. **GPIO42 boot transients:** GPIO42 = MTMS (JTAG strap). If 5V PMID boost is not yet enabled during boot, the LED is unpowered and any boot transient on GPIO42 is irrelevant. Confirm PMID enable sequencing in firmware boot sequence to ensure this safe ordering.

---

*20.15 — End of extract.*
