porupski/kompic-wearable/firmware/docs/datasheet_extracts/20.16_Encoder_Datasheet_Extract_iv7.1_f0.0_2026-06-18.md

# 20.16 — ALPS EC05E1220401 ENCODER DATASHEET EXTRACT
**Date:** 2026-06-18 · **Datasheet:** ALPSALPINE EC05E1220401.pdf · **Pages:** 4 total · **Hardware:** iv7.1 · **Firmware porting:** f0.0
**Parsed by:** Claude Code Sonnet 4.6

---

## Critical findings (read this first)

No hardware-breaking conflicts vs. iv7.1. Three firmware-actionable points:

### 1. Bounce time is 6 ms — PCNT filter must be supplemented with software debounce [p. 3]

The datasheet states: *"振荡 : 6ms max. 跳动 : 6ms max."* (oscillation bounce: 6 ms max; jitter bounce: 6 ms max) measured at V=5V, R=10kΩ. Both figures are quoted at 5V. At 3.3V with pull-ups, bounce may differ; however, the datasheet gives no 3.3V figure. **Use 6 ms as the design value.** The ESP32-S3 PCNT glitch filter register `PCNT_GLITCH_THRES` is 10 bits (max 1023 cycles = ~12.8 µs at 80 MHz APB), which is **far too short to filter mechanical bounce on its own.** Mechanical debounce must be handled in firmware (timer-based or state-machine) after the PCNT interrupt; the PCNT filter only eliminates RF/EMI glitches.

### 2. Output is purely resistive (mechanical switch) — 3.3V compatible with pull-ups [p. 1, p. 3]

The encoder is a passive mechanical type. The terminals (A, B, C) are dry contacts — no active output stage, no power supply required by the encoder itself. The rated operating point is 0.55 mA @ 5.5V DC. At 3.3V with 10kΩ pull-ups the contact current is 3.3V / 10kΩ = 0.33 mA, within the 0.55 mA rating. 3.3V operation is confirmed safe.

### 3. A/B phase at detent position is undefined [p. 3]

The output waveform diagram includes a note: *"※ 定位位置の A 相、B 相输出未作规定。"* — "The A-phase and B-phase outputs at the detent position are not specified." Firmware must not rely on a known absolute A/B level at rest; it must decode transitions only.

---

## Cross-reference vs v7.2

| Spec | v7.2 / pinout says | Datasheet says | Match? | Action |
|---|---|---|---|---|
| Part type | Crown rotary encoder, quadrature A/B | Incremental encoder, A/B 2-phase output [p. 1] | ✓ | — |
| EC_SigA → GPIO21 | GPIO21 (RTC wake-capable) | Terminal A on the encoder [p. 2] | ✓ | — |
| EC_SigB → GPIO43 | GPIO43 / TXD0, ~3ms boot spurious edge | Terminal B on the encoder [p. 2] | ✓ | Boot spurious edge is 3ms; bounce is 6ms — boot edge lands within the bounce-ignore window |
| Push switch present | "No push switch expected from pinout" | No push-switch terminals — only A, B, C (common) [p. 2] | ✓ | Confirmed: no push switch on this part |
| 3.3V rail compatibility | 3.3V domain | Rated 0.55 mA @ 5.5V DC; passive contacts [p. 1] | ✓ | 0.33 mA at 3.3V / 10kΩ is within rating |
| PPR / detents | Not specified in iv7.1 doc | 12 pulses per revolution, 12 detents per revolution [p. 1] | N/A — new info | Document for UI design (12 clicks = 360°) |
| PCNT usage | "ESP32-S3 PCNT will be used" | Mechanical output — glitch filter alone insufficient for 6ms bounce [p. 3] | N/A | See Firmware Implications |

---

## Mechanical / Electrical specs

| Parameter | Value | Source |
|---|---|---|
| Type | Mechanical incremental encoder (dry contact) | [p. 1] |
| Output | Resistive / passive 2-phase (A, B) — no active driver | [p. 1, p. 3] |
| Pulses per revolution (PPR) | 12 | [p. 1] |
| Detents per revolution | 12 | [p. 1] |
| Pulses per detent | 1 (1:1 pulse-to-detent ratio) | [p. 1] |
| Max rotation rate | Not specified | [not found in datasheet] |
| Contact bounce time (oscillation) | 6 ms max (at 5V, R=10kΩ) | [p. 3] |
| Contact bounce time (jitter) | 6 ms max (at 5V, R=10kΩ) | [p. 3] |
| Rated operating current | 0.55 mA max (resistive load) | [p. 1] |
| Rated operating voltage | 5.5V DC (rated point) | [p. 1] |
| Contact resistance | Not stated as standalone spec | [not found in datasheet] |
| Insulation resistance | 50 MΩ min @ 50V DC | [p. 1] |
| Withstand voltage | 50V AC for 1 minute | [p. 1] |
| Positioning torque | 1.6 ± 1.3 mN·m | [p. 1] |
| Operating temperature | -30°C to +85°C | [p. 1] |
| Lifespan | 100,000 cycles | [p. 1] |
| Body dimensions (W × D) | ~7.6 × 5.7 mm footprint | [p. 2] |
| Shaft diameter | ø2.2 mm | [p. 2] |
| Shaft hole profile | Hex (6-60°), B-face inner ø2.7 mm | [p. 2] |
| PCB mount type | SMD (surface mount) | [p. 2, p. 4] |
| Terminal count | 3: A, C (common), B | [p. 2] |
| Mounting holes | 2× ø0.62 mm through-holes for mechanical retention | [p. 2] |

---

## Wiring

| Terminal | Label | Function | Connect to |
|---|---|---|---|
| A | A | Phase A output (dry contact to C) | GPIO21 (EC_SigA) via 10kΩ pull-up to 3.3V |
| C | C | Common (return) | GND |
| B | B | Phase B output (dry contact to C) | GPIO43 (EC_SigB) via 10kΩ pull-up to 3.3V |
| Mounting holes | — | Mechanical retention only | Soldered to GND pads |

**No push switch.** The EC05E1220401 variant has no push-switch terminals.

**Pull-up sizing:** 10kΩ to 3.3V → I_contact = 0.33 mA, within the 0.55 mA rating.

**Phase relationship:** On CW rotation, A leads B (per the output waveform diagram). At detent rest positions, A/B states are unspecified [p. 3].

---

## Firmware implications

### PCNT configuration

The ESP32-S3 PCNT hardware filter (`PCNT_GLITCH_THRES`) can only suppress pulses shorter than ~12.8 µs at 80 MHz APB. The encoder's 6 ms bounce is ~470× longer than the filter maximum — **the PCNT filter alone cannot debounce this encoder.**

Recommended approach:

1. **PCNT glitch filter:** Set to maximum (~1023 APB cycles ≈ 12.8 µs) to suppress RF/EMI glitches only.

2. **Interrupt-driven debounce timer:** On PCNT interrupt, start a one-shot FreeRTOS timer for **8 ms** (6 ms bounce + 2 ms margin). Discard any additional PCNT events that arrive within the 8 ms window. Accept the first event after the timer expires as a confirmed tick.

3. **Quadrature decoding mode:** Use PCNT in quadrature mode. At 12 PPR with X1 → 12 counts/rev (1 count per detent click — natural UI unit).

4. **Direction:** PCNT natively detects direction from A/B phase sequence. Check CW/CCW polarity on bench and swap A/B assignment in firmware if needed (no hardware change required).

5. **Boot edge on GPIO43 (EC_SigB):** A single ~3 ms spurious edge appears on TXD0/GPIO43 during the boot ROM log. Delay PCNT init by ≥10 ms post-boot to avoid it.

6. **Wake from deep sleep:** GPIO21 (EC_SigA) is RTC wake-capable; GPIO43 (EC_SigB) is not — direction cannot be determined on the wake edge alone. Direction decoding resumes after full init.

### Suggested PCNT register values (ESP-IDF v5.x)

```c
pcnt_unit_config_t unit_cfg = {
    .low_limit  = -32767,
    .high_limit =  32767,
};
pcnt_glitch_filter_config_t filter_cfg = {
    .max_glitch_ns = 12800,  // 12.8 µs max — suppresses EMI only, not mechanical bounce
};
// Software 8 ms one-shot debounce timer in PCNT ISR callback
```

---

## Datasheet notes

1. **Chinese-language datasheet** (ALPS Alpine product page, archived 2017-10-25). Part EC05E1220401 = "5-type through-shaft" (5型贯通轴型) EC05E series. [p. 1]
2. **Bounce measurement conditions:** oscillation and jitter both measured at 5V DC, R=10kΩ, rotation speed 360°/s. [p. 3]
3. **A/B waveform:** Standard 2-phase quadrature, overlapping pulses 90° apart, CW rotation shown. At each detent, A/B output state explicitly not guaranteed. [p. 3]
4. **Reflow conditions:** Peak 250°C max, 230°C min for soldering zone, preheat 150–180°C for 60–120s, peak dwell 30–40s, max 2 reflow passes. Hand-solder: ≤350°C iron, 3s max. [p. 4]
5. **Shaft hex profile:** 6-60° lobe pattern, B-face reference ø2.7 mm — crown shaft must be machined to mate with this geometry for the slip fit. [p. 2]
6. **Lifespan in context:** 100,000 cycles at 12 detents/rev = 8,333 full revolutions. At 20 crown interactions/day ≈ 1.5 years to wear rating. Relevant for serviceability planning. [p. 1]

---

## Warnings & Errata

| ID | Title | Impact | Notes |
|---|---|---|---|
| W-01 | PCNT glitch filter insufficient for bounce | HIGH (firmware) | 6 ms bounce >> 12.8 µs PCNT filter max. Software 8 ms debounce timer mandatory. [p. 3] |
| W-02 | A/B state at detent undefined | HIGH (firmware) | Decode transitions only; treat detent rest state as don't-care. [p. 3] |
| W-03 | Bounce spec measured at 5V, not 3.3V | MEDIUM | Use 6 ms as conservative design value. Verify on bench at 3.3V — bounce may be shorter but cannot be assumed so without measurement. |
| W-04 | Max rotation rate not specified | LOW | Crown is hand-operated; at 12 PPR and 4 rev/s max, pulse rate ≈ 48 Hz (period 20 ms >> bounce). No concern at human speeds. [datasheet silent; recommend bench test] |
| W-05 | Boot spurious edge on GPIO43 (EC_SigB) | LOW (known) | Single ~3 ms glitch during boot ROM log. Delay PCNT init by ≥10 ms post-boot. No hardware change required. |
| W-06 | GPIO21 wake-capable; GPIO43 is not | LOW (firmware) | Direction unknown on sleep-wake edge. Discard or handle gracefully; direction decoding resumes after PCNT init. |
| W-07 | Encoder lifespan ~1.5 years at daily use | INFO | 100,000 cycles at 20 interactions/day. Note for product serviceability documentation. [p. 1] |

---

## Open questions

1. **Contact resistance value:** Not stated in datasheet. Measure on bench with 4-wire milliohm measurement (expected < 100Ω for a new encoder). Relevant if pull-up resistor value is changed.
2. **Bounce at 3.3V:** The 6 ms spec is at 5V. Measure bounce on bench with 3.3V supply and scope before finalising the debounce timer value.
3. **CW/CCW polarity mapping:** Confirm on bench — "CW" is relative to encoder body orientation on PCB. Adjust PCNT channel count direction in firmware if inverted.
4. **Hex shaft fit:** Confirm crown shaft across-flats dimension against ALPS B-face ø2.7 mm reference circle before machining. Measure a physical sample with callipers. [p. 2]

---

*20.16 — End of extract.*
