porupski/kompic-wearable/firmware/docs/datasheet_extracts/20.17_Flashlight_LED_MOSFET_Extract_iv7.1_f0.0_2026-06-18.md

# 20.17 — FLASHLIGHT LED + GATE MOSFET DATASHEET EXTRACT
**Date:** 2026-06-18 · **Datasheets:** `TOGIALED TJ-S4008SW4TGLCCW-A5.pdf` (9 pp.) · `onsemi BSS138W.pdf` (6 pp.) · **Hardware:** iv7.1 · **Firmware porting:** f0.0
**Parsed by:** Claude Code Sonnet 4.6
**Scope:** LED2 (flashlight emitter) + U12 (gate MOSFET). Two separate datasheets, combined into one extract because the LED and MOSFET form a single switch-mode load. Also covers PCB circuit topology, 5 V rail constraints, and the PWM-dimming calculation.

---

## Cross-reference vs v7.2

| Spec | v7.2 says | Datasheet says | Match? | Action |
|---|---|---|---|---|
| LED part | TJ-S4008SW4TGLCCW-A5 (LED2) | TJ-S4008SW4TGLCCW-A5, SMD 3.5 package (4.0 × 1.4 mm, 0.8 mm thick), white [p. 1–2] | ✓ | — |
| LED Vf (nominal) | ~3.2 V [Phase 4 kickoff] | 2.8 V min – 3.6 V max @ If = 20 mA; **no typical given** [p. 3] | ⚠ | Kickoff's "3.2 V typical" is an engineer's mid-range estimate — the datasheet gives no explicit typical. Use 3.2 V for power budget (mid-span), but design for worst-case Vf = 3.6 V. |
| LED rated current | 30 mA max [kickoff] | **If = 30 mA** (absolute maximum) [p. 3] | ✓ | Do not exceed. For continuous use derate to 20 mA (datasheet life-test condition [p. 7]). |
| MOSFET part | BSS138W (U12) | BSS138W, N-channel logic-level MOSFET, SOT-323 (SC-70) package [p. 1] | ✓ | LCSC BOM footprint lists "SC-70-3"; onsemi labels same package CASE 419AB / SOT-323 — same die. |
| MOSFET Vgs(th) | "3.3 V gate drives it fully on" [kickoff] | Vgs(th) = 0.8 V min / 1.3 V typ / 1.5 V max @ Vds = Vgs, Id = 1 mA [p. 2] | ✓ | GPIO41 at 3.2 V drives gate well above threshold. Rds(on) at 3.2 V: ~8–10 Ω extrapolated from Fig. 4 [p. 3]. |
| MOSFET Rds(on) | "low" [kickoff] | Rds(on) typ 1.36 Ω @ Vgs = 4.5 V; at Vgs = 3.2 V (operating point) extrapolated ~8–10 Ω from Fig. 4 [p. 2–3] | ⚠ | At 20 mA LED current the Vds drop is ~0.16–0.20 V — negligible. Verify on bench. See WARN-01. |
| Gate resistor | 47 Ω series | Rg (internal) = 11 Ω typ @ 1 MHz [p. 2]; 47 Ω external in series | ✓ | Total gate path = 58 Ω. Limits shoot-through current, slows edges — correct. |
| Gate pull-down | 10 kΩ to GND | Datasheet silent; standard practice [p. 1] | ✓ | Ensures MOSFET off at boot before GPIO41 is driven. |
| LED series resistors | 47 Ω × 2 (v7.2 BOM "flashlight ×2") | Datasheet silent (external circuit) | ✓ | 2 × 47 Ω = 94 Ω. At 5 V supply, Vf ≈ 3.2 V, Vds(on) ≈ 0.1 V: I ≈ 18 mA — within 30 mA abs-max. |
| 5 V source | BQ25619 PMID boost | 5.0 V boost, 1 A max, boost/charge mutually exclusive [v7.2] | ✓ | See 5 V Boost Arbitration section. |
| GPIO control | GPIO41 (GPIO_FLASHLIGHT) | Datasheet silent | ✓ | v7.2 assigns GPIO41 with external 10 kΩ pull-down. Boot state clean. |

**Key conflict:** LED Vf "typical" of 3.2 V is a mid-range estimate only. Resistor sizing must be validated against the full 2.8–3.6 V window.

---

## Pinout — LED (TJ-S4008SW4TGLCCW-A5)

| Pin | Name | Function | Notes |
|---|---|---|---|
| + (longer pad) | Anode | LED anode | Connects to 5 V via 2 × 47 Ω in series [p. 2] |
| − (shorter pad) | Cathode | LED cathode | Connects to drain of U12 (BSS138W) [p. 2, 6] |

*Package: 4.0 × 1.4 mm body, 0.8 mm thick, 2-pad SMD. Anode on left, cathode on right in standard orientation [p. 2].*

## Pinout — MOSFET (BSS138W, SOT-323 / SC-70)

| Pin | Name | Function | Notes |
|---|---|---|---|
| 1 | Source (S) | Source | Tied to GND [p. 1] |
| 2 | Drain (D) | Drain | Connects to LED2 cathode [p. 1] |
| 3 | Gate (G) | Gate | GPIO41 via 47 Ω series; 10 kΩ pull-down to GND [p. 1] |

*SOT-323 = SC-70, 3-lead, 1.25 × 2 mm body (JEDEC MO-203), CASE 419AB [p. 5].*

---

## Circuit Topology (iv7.1 as-built)

```
+5 V (BQ25619 PMID boost)
    │
   47 Ω  ← R_ser1 (series current limit)
    │
   47 Ω  ← R_ser2
    │
  LED2 Anode  (TJ-S4008SW4TGLCCW-A5)
  LED2 Cathode
    │
  U12 Drain  (BSS138W)
  U12 Source ── GND
  U12 Gate ──┬── 47 Ω ── GPIO41 (ESP32-S3, 3.2 V rail)
             └── 10 kΩ ── GND
```

**Current at operating points [p. 3 LED; p. 2 MOSFET — derived]:**

| Condition | Vf | I_LED |
|---|---|---|
| Nominal (mid-range Vf) | 3.2 V | ≈ 18.1 mA |
| Worst-case low Vf | 2.8 V | ≈ 22.9 mA |
| Worst-case high Vf | 3.6 V | ≈ 13.3 mA |

All within the 30 mA abs-max [p. 3].

---

## LED Electrical & Optical Specifications

### Absolute Maximum Ratings (TA = 25 °C) [p. 3]

| Parameter | Symbol | Value | Unit |
|---|---|---|---|
| Forward current (continuous) | If | 30 | mA |
| Peak pulsed current (1/8 duty, 1 kHz) | Ifp | 125 | mA |
| Reverse voltage | Vr | 5 | V |
| Power dissipation | Pd | 108 | mW |
| Operating temperature | Top | −40 to +80 | °C |
| Storage temperature | Tstg | −40 to +85 | °C |

### Electro-optical Characteristics (TA = 25 °C, If = 20 mA) [p. 3]

| Parameter | Symbol | Min | Typ | Max | Unit |
|---|---|---|---|---|---|
| Color temperature | CCT | 6000 | — | 8000 | K |
| Forward voltage | Vf | 2.8 | — | 3.6 | V |
| Luminous intensity | Iv | 6 | — | 9 | lm |
| Viewing angle at 50% Iv (If = 10 mA) | 2θ½ | — | 120 | — | deg |
| Reverse current (Vr = 5 V) | Ir | — | — | 10 | µA |

**No explicit typical Vf given** [p. 3]. Forward-voltage curve (Fig. 3 [p. 4]) shows knee at ~3.0–3.2 V with steep rise above 3.2 V up to 30 mA.

### Power Dissipation at Operating Points [p. 3 — derived]

| Condition | If | Vf (est.) | P_LED |
|---|---|---|---|
| Nominal | 18 mA | 3.2 V | ~58 mW |
| Worst-case low Vf | 23 mA | 2.8 V | ~64 mW |
| Worst-case high Vf | 13 mA | 3.6 V | ~47 mW |
| Absolute max continuous | 30 mA | 3.6 V | 108 mW |

### Derating with Temperature [p. 4, Fig. 2]

If de-rates from 30 mA at 25 °C to approximately 10 mA at 80 °C. At wrist temperature (~35 °C) de-rating is minimal. **No θja given in the datasheet** — see WARN-02.

---

## MOSFET Electrical Specifications

### Absolute Maximum Ratings (TA = 25 °C) [p. 1]

| Parameter | Symbol | Value | Unit |
|---|---|---|---|
| Drain–source voltage | Vdss | 50 | V |
| Gate–source voltage | Vgss | ±20 | V |
| Drain current, continuous | Id | 0.21 | A |
| Drain current, pulsed | Id(pulse) | 0.84 | A |
| Operating junction temperature | Tj | −55 to +150 | °C |

### Thermal Characteristics [p. 2]

| Parameter | Symbol | Value | Unit |
|---|---|---|---|
| Power dissipation (TA = 25 °C) | PD | 340 | mW |
| Derate above 25 °C | — | 2.72 | mW/°C |
| Thermal resistance junction to ambient | θja | 367 | °C/W |

### Key Electrical Characteristics (TA = 25 °C) [p. 2]

| Parameter | Symbol | Condition | Min | Typ | Max | Unit |
|---|---|---|---|---|---|---|
| Gate threshold voltage | Vgs(th) | Vds = Vgs, Id = 1 mA | 0.8 | 1.3 | 1.5 | V |
| Rds(on) | — | Vgs = 10 V, Id = 0.22 A | — | 1.17 | 3.5 | Ω |
| Rds(on) | — | Vgs = 4.5 V, Id = 0.22 A | — | 1.36 | 6.0 | Ω |
| Rds(on) at 125 °C | — | Vgs = 10 V, Id = 0.22 A | — | 2.16 | 5.8 | Ω |
| Input capacitance | Ciss | Vds = 25 V, f = 1 MHz | — | 38 | — | pF |
| Gate resistance (internal) | Rg | f = 1 MHz | — | 11 | — | Ω |
| Turn-on delay | td(on) | Vdd = 30 V, Rgen = 6 Ω | — | 2.3 | 5 | ns |
| Turn-off delay | td(off) | same | — | 6.7 | 36 | ns |
| Total gate charge | Qg | Vds = 25 V, Id = 0.22 A | — | 1.1 | — | nC |

**Rds(on) at Vgs = 3.2 V (extrapolated from Fig. 4 [p. 3]):** ~8–10 Ω at Id = 20 mA.
Vds(on) ≈ 0.16–0.20 V — negligible. Verify on bench.

**MOSFET dissipation at operating point:** P = Id² × Rds(on) = (0.018)² × 9 ≈ **2.9 mW** — far below 340 mW PD rating.

---

## Initialization / Drive Sequence

No register map — purely hardware-controlled. Firmware interaction via GPIO41 only.

```
Boot default (MOSFET off):
1. GPIO41 is INPUT (Hi-Z) at reset.
   10 kΩ pull-down holds Gate = GND → MOSFET off → LED off.

Enable flashlight:
2. Configure GPIO41 as OUTPUT.
3. Enable BQ25619 PMID boost (5 V) via I2C — wait ~100 µs for stabilization.
4. Set GPIO41 HIGH (3.2 V) → MOSFET on → LED lights up.
   Turn-on delay: td(on) typ 2.3 ns [p. 2]. Effectively instantaneous.

Disable flashlight:
5. Set GPIO41 LOW → MOSFET off → LED off.
   Turn-off: td(off) + tf typ 13.2 ns [p. 2]. Instantaneous.

PWM dimming:
6. LEDC at ≥ 1 kHz (above flicker threshold), ≤ 100 kHz (well within
   MOSFET capability: f_max ≈ Vgs/(Rg_total × Qg) ≈ 50 MHz [derived p. 2]).
   Average current = duty × I_on.
```

---

## Power Consumption

| State | Condition | Current (5 V rail) | Notes |
|---|---|---|---|
| Off | GPIO41 = LOW, boost on | ~0 mA | Reverse leakage < 10 µA [p. 3] |
| On, nominal | Vf = 3.2 V, 2 × 47 Ω | ≈ 18 mA | [p. 3 — derived] |
| On, worst-case low Vf | Vf = 2.8 V | ≈ 23 mA | [p. 3 — derived] |
| On, worst-case high Vf | Vf = 3.6 V | ≈ 13 mA | [p. 3 — derived] |
| PWM 50% duty | Nominal Vf | ≈ 9 mA (avg) | duty × I_on |
| GPIO gate avg | 100 kHz PWM | ~12 µA | 38 pF × 3.2 V × 100 kHz [p. 2 — derived] |

---

## 5 V Boost Arbitration

| Consumer | Peak current (5 V rail) | Notes |
|---|---|---|
| MAX30101 VDD_LED | up to ~200 mA | HR/SpO2 LEDs at full drive |
| WS2812B-2020 | up to ~60 mA | Full white [20.15 extract] |
| Flashlight LED2 | ≈ 13–23 mA | Across Vf tolerance window |
| **Combined worst-case** | **< 300 mA** | Well within 1 A boost limit |

All three may be active simultaneously without exceeding the 1 A PMID headroom. **However, boost is mutually exclusive with charging** [20.13 extract] — firmware must disable boost when USB-C is inserted.

---

## Datasheet Notes

1. TJ-S4008SW4TGLCCW-A5 is a "specification for approval" document — some typical values (including Vf typical) are intentionally omitted. Validate Vf against the min/max window in production. [p. 1]
2. Vf window 2.8–3.6 V (0.8 V span at 20 mA) is unusually wide. Current-regulated drive (series resistor + fixed 5 V) is correct — it normalises brightness across the Vf spread. [p. 3]
3. Luminous intensity 6–9 lm at 20 mA [p. 3]. At 18 mA nominal ≈ 5.4–8.1 lm — a narrow-cone torch, not a room illuminator.
4. LED operating temp limit is 80 °C [p. 3]; MOSFET is 150 °C [p. 1]. The LED is the thermal weak link.
5. No dominant wavelength or color bin given beyond CCT 6000–8000 K (cool white) [p. 3].
6. Gate charge Qg = 1.1 nC [p. 2] — very low; no gate driver IC needed.
7. BSS138W body diode Vsd max 1.4 V [p. 2]. Not a concern in this topology.

---

## Warnings & Errata

| ID | Title | Impact | Notes |
|---|---|---|---|
| WARN-01 | Rds(on) at Vgs = 3.2 V not in spec table | LOW | Extrapolated ~8–10 Ω from Fig. 4 [p. 3]. Vds(on) ≈ 0.16–0.20 V at 20 mA — acceptable. Measure Vds(on) on bench to confirm. |
| WARN-02 | LED θja not specified; thermal limit 80 °C | MED | No junction thermal resistance given [p. 3]. Unknown junction temperature inside sealed titanium case under sustained load. Mitigation: firmware timeout (e.g., 30 s max continuous on). Measure LED surface temp on prototype. If case heats up, If must be PWM-limited (derating to ~10 mA at 80 °C [p. 4, Fig. 2]). |
| WARN-03 | 5 V boost must be enabled before flashlight | HIGH | GPIO41 HIGH without boost = MOSFET on into no supply → no light, no damage, but confusing. Sequence: (1) enable boost via BQ25619 I2C, (2) wait ~100 µs, (3) assert GPIO41. Encapsulate in a single FW function. |
| WARN-04 | Boost/charge mutual exclusion | HIGH | Charger plug-in while flashlight active: disable boost first, then allow charging. Register charger-plug event and gate flashlight accordingly [20.13 extract]. |
| WARN-05 | Wide Vf → brightness variation across units | LOW | ~1.5× intensity variation at fixed series resistance. Acceptable for Mk I. For production, consider constant-current drive or per-unit calibration. |
| WARN-06 | SOT-323 / SC-70 package naming | LOW | LCSC BOM says "SC-70-3"; onsemi says SOT-323 / CASE 419AB [p. 5]. Same package (JEDEC MO-203). Confirm PCB footprint pad layout matches onsemi mechanical drawing [p. 5] before fabrication. |

---

## Open Questions

1. **Bench verify Rds(on) at 3.2 V gate:** Measure Vds(on) with 5 V supply, GPIO41 from 3.2 V source, known series resistor. Action: Ivan measures on first-article board.
2. **LED junction temp under continuous load:** Surface temp after 30 s in sealed case? Action: IR thermometer or thermocouple on prototype.
3. **Firmware flashlight timeout:** Hard cutoff at 30 s or 60 s? Action: decide after thermal bench result.
4. **PWM dimming levels:** Multiple brightness steps desired (low/mid/full)? LEDC at ≥ 1 kHz is straightforward. Action: Ivan decides at feature spec stage.

---

*20.17 — End of extract.*
