porupski/kompic-wearable/firmware/docs/datasheet_extracts/20.12_BME688_Datasheet_Extract_iv7.1_f0.0_2026-06-18.md

# 20.12 — BME688 DATASHEET EXTRACT
**Date:** 2026-06-18 · **Datasheet:** bst-bme688-ds000.pdf (Bosch BST-BME688-DS000-03, Rev 1.3, Feb 2024) + bst-bme688-an001.pdf (BME AI-Studio Manual, Rev 1.6.0, June 2021) · **Pages:** 60 + 78 total · **Hardware:** iv7.1 · **Firmware porting:** f0.0
**Parsed by:** Claude Code Opus

---

## Critical findings (read this first)

### 1. CSB pin MUST be tied to V_DDIO for I²C mode [p. 45, 46, 52]

The BME688 supports both I²C and SPI. Interface auto-selects based on CSB pin level **at power-up reset**:
- **CSB = HIGH (V_DDIO) → I²C mode**
- CSB = LOW or transient toggle → SPI mode locked in (until next POR)

**v7.2 / porting-doc do not call out the CSB pin disposition.** If left floating or routed to an ESP GPIO that happens to read LOW during BME688 power-up, the chip will lock into SPI mode and stay deaf to I²C until next power-cycle. **Action:** confirm v7.2 schematic ties CSB directly to V_DDIO (3V3) at the chip. Datasheet [p. 52, Picture 15(a)] shows the I²C connection diagram explicitly with CSB→V_DDIO.

### 2. SDO pin cannot float [p. 45]

SDO selects the I²C address LSB:
- **SDO = GND → address 0x76 (default)**
- SDO = V_DDIO → address 0x77 (clash with BMP280)

*"The SDO pin cannot be left floating; if left floating, the I²C address will be undefined."* [p. 45]

v7.2 / porting-doc say address = 0x76. **Action:** confirm SDO is tied to GND on PCB.

### 3. No interrupt pin [p. 51, Table 26]

BME688 has **no INT pin**. There is no `new_data` interrupt output. The only way to know a measurement is complete is to poll the `meas_status` register (0x1D/0x2E/0x3F bit 7 = new_data). The porting-doc line 31 *"INT — not routed"* — confirmed; there's no INT signal anywhere on the chip. **All status sampling is polled.**

This makes the 200 ms forced-mode cycle even more interesting: the FW *must* poll repeatedly during that window (or trust the meas-dur computation and sleep blindly). The Bosch BME68x library uses the latter approach — `bme68x_get_meas_dur()` returns a μs estimate; FW calls `delay()` for that long, then issues a single read.

---

## Cross-reference vs v7.2

| Spec | v7.2 / porting-doc says | Datasheet says | Match? | Action |
|---|---|---|---|---|
| Part / package | BME688 LGA-8, 3.0×3.0×0.9 mm | BME688 LGA, 3.0×3.0×0.93 mm metal-lid [p. 3, 53] | ✓ | — |
| I²C address (7-bit) | 0x76 (BME68X_I2C_ADDR_LOW; ADDR pin = GND) | 0x76 with SDO=GND, 0x77 with SDO=V_DDIO [p. 45] | ✓ | Datasheet uses SDO (not "ADDR") for the address-select pin. Naming alias. |
| Chip-ID register | 0xD0, expect 0x61 | 0xD0 (I²C) = chip_id, value 0x61 [p. 32, 36] | ✓ | — |
| Variant ID register | (not mentioned) | 0xF0 (I²C) = variant_id, value 0x01 distinguishes BME688 from BME680 (variant 0x00) [p. 36] | new | **Recommend FW also verify variant_id at boot** — chip_id 0x61 is shared between BME680 and BME688; only the variant_id confirms BME688. |
| I²C bus | Bus 1 (GPIO1=SDA, GPIO2=SCL), 400 kHz | Standard 100 kHz, Fast 400 kHz, High Speed 3.4 MHz [p. 3, 49] | ✓ | — |
| **CSB pin disposition** | (not specified) | **MUST be tied to V_DDIO for I²C mode** [p. 45, 46, 52] | ? | **HARDWARE GAP — see Critical Finding #1** |
| **SDO pin disposition** | "ADDR pin = GND" (implicit) | GND for 0x76; cannot float [p. 45] | ✓ (verify) | Confirm v7.2 schematic ties SDO to GND |
| V_DD supply rail | "3V3 (TPS62840, always-on)" | 1.71–3.6 V (typ **1.8 V; optimized for 1.8 V** per footnote [p. 7]) | ✓ | The chip works at 3V3 but Bosch optimizes power efficiency for 1.8 V. Acceptable trade-off in Mk I. |
| V_DDIO supply rail | (not split; single 3V3 rail) | 1.2–3.6 V (typ 1.6 V) | ✓ | OK to share with V_DD at 3V3 |
| Single rail OK? | "Single rail; no V_IO split" | V_DD and V_DDIO are independent supplies (datasheet p. 51) but can be tied together | ✓ | — |
| Heater profile | "320 °C / 150 ms (Bosch default)" | Up to 10 programmable steps, target temp 0–400 °C, duration 0–4032 ms [p. 27, 38, 39] | ✓ | — |
| Heater settle time | "~20 ms" (porting log Profiling table) | **~20–30 ms necessary for heater to reach intended target temperature** [p. 28] | ✓ | — |
| Forced-mode cycle | "~200 ms typical" | TPH meas + heater-on time + read latency. At 1x OSR + 150 ms heater = ~150 + 30 (settle) + ~10 (TPH meas) = ~190 ms. Use `bme68x_get_meas_dur()` for exact. | ✓ | — |
| **INT pin** | "not routed" | **chip has no INT pin** [p. 51] | ✓ | Polled-only operation is forced |
| Sleep mode | (between forced-mode cycles) | I_DDSL = 0.15 µA typ, 1 µA max [p. 7] | ✓ | — |
| Heater pulse current | "~12 mA peak, ~1 mA average" | I_DD = 9 / 12 / 13 mA min/typ/max at 320 °C constant; I_Peak = 15 / 17 / 18 mA in first 1 ms of switch-on [p. 8] | ✓ | The "~12 mA average during pulse" porting figure is the steady-state plateau current per [p. 8 Table 2]. |

---
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
