porupski/kompic-wearable/firmware/docs/datasheet_extracts/20.13_BQ25619_Datasheet_Extract_iv7.1_f0.0_2026-06-18.md

# 20.13 — BQ25619 DATASHEET EXTRACT
**Date:** 2026-06-18 · **Datasheet:** bq25619.pdf (TI SLUSDF8F, June 2019 – Revised February 2025) · **Pages:** 56 total · **Hardware:** iv7.1 · **Firmware porting:** f0.0
**Parsed by:** Claude Code Opus

---

## Critical finding (read this first)

**The BQ25619 has NO battery voltage ADC.** The complete I²C register map is REG00–REG0C (13 registers, p. 32). REG0B is the Part Information register, not a VBAT readout. There is **no register anywhere in the chip that reports the measured battery voltage to the host.**

This directly contradicts two things:
1. **v7.2 §POWER ARCHITECTURE** ("Battery voltage: read via I²C BATSNS (no external ADC)") — wrong. BATSNS (pin 10) is an *analog* remote-sense input the IC uses to close its own CV regulation loop. It is not exposed to I²C.
2. **The porting doc** `BQ25619_2026-06-11_iv7.1.f0.0.md` line 82 and DEFECT-005 — `BQ25619_REG_VBAT_ADC (0x0B)` does not exist. 0x0B is REG0B Part Information. There is no VBAT ADC and no scaling formula to verify.
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
