porupski/kompic-wearable/docs/img/development/1_mk1_pcbs.jpeg

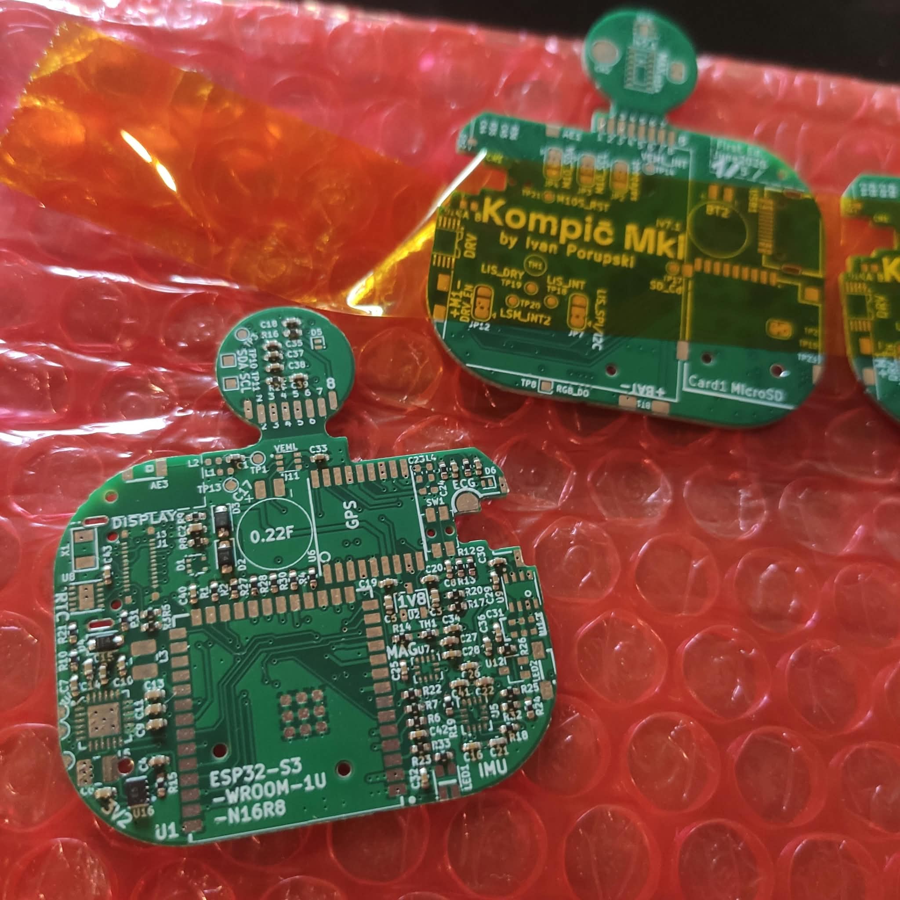
docs/img/development/1_mk1_pcbs.jpeg
