porupski/kompic-wearable/docs/img/development/2_reflow.jpeg

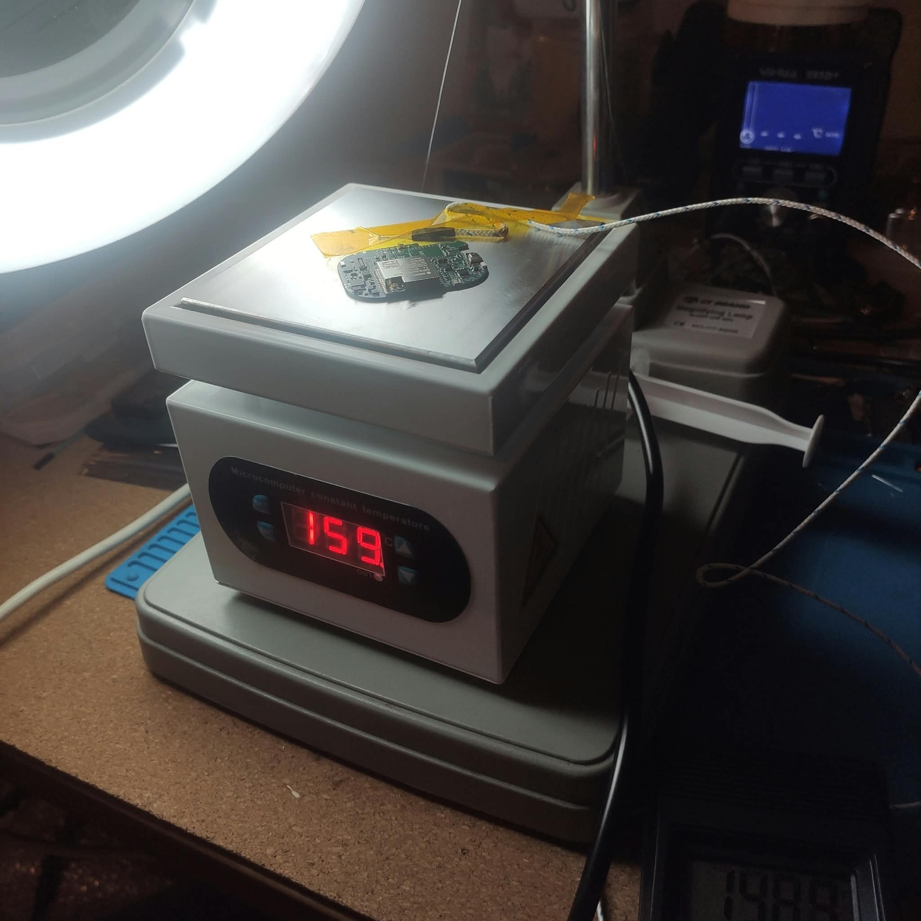
docs/img/development/2_reflow.jpeg
