porupski/kompic-wearable/docs/img/development/3_mk1_first_light.jpeg

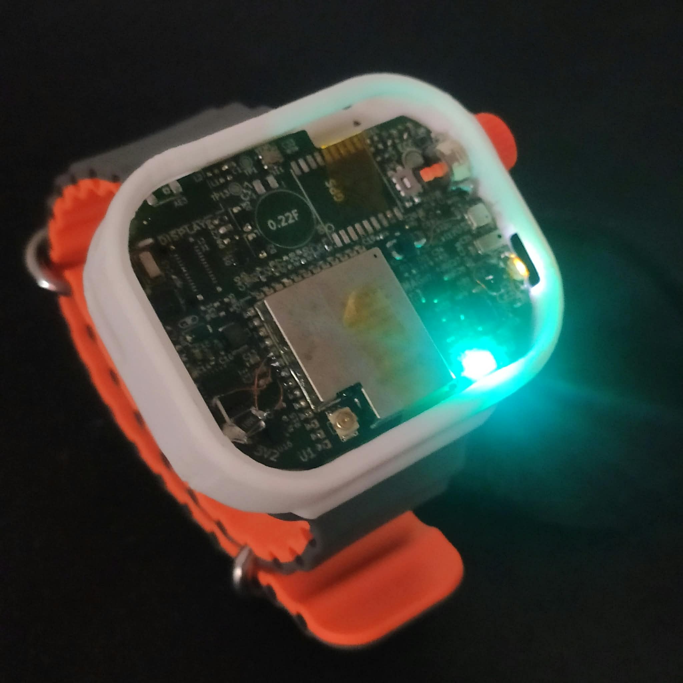
docs/img/development/3_mk1_first_light.jpeg
