porupski/kompic-wearable/docs/img/development/4_bodges.jpeg

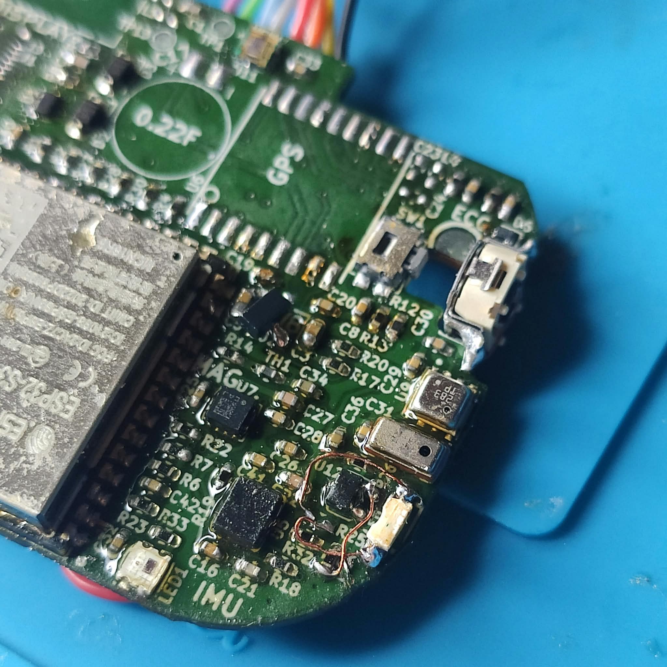
docs/img/development/4_bodges.jpeg
