porupski/kompic-wearable/docs/img/development/6_daughter_board.jpeg

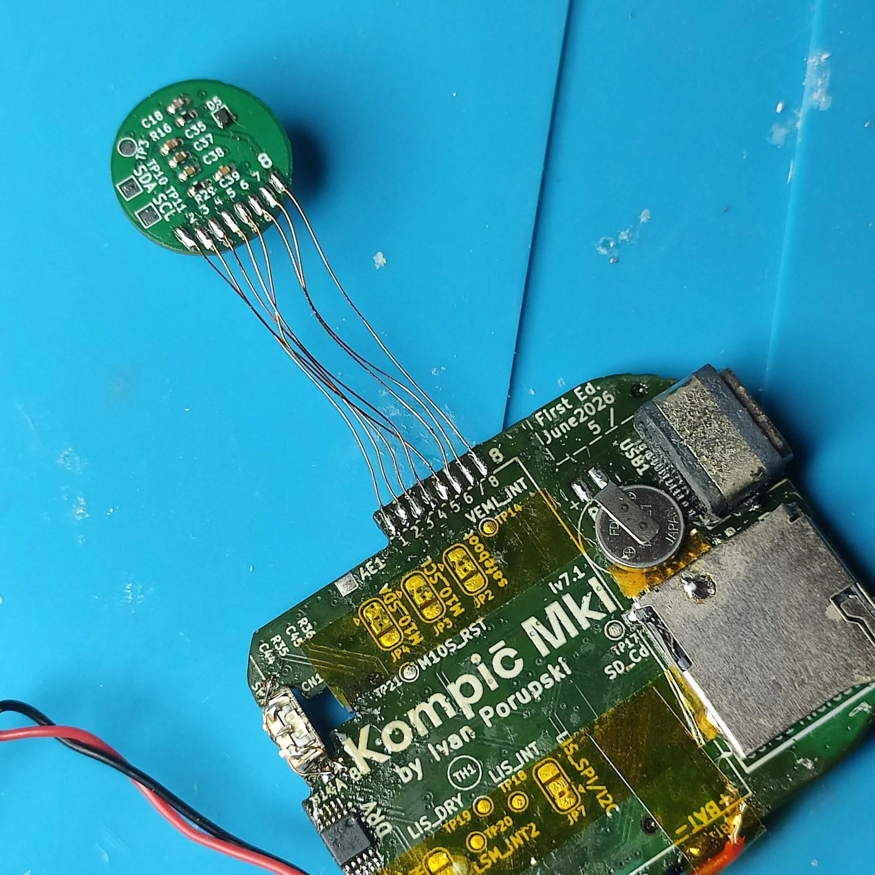
docs/img/development/6_daughter_board.jpeg
