porupski/kompic-wearable/docs/img/development/7_mk1b_3d_render.jpeg

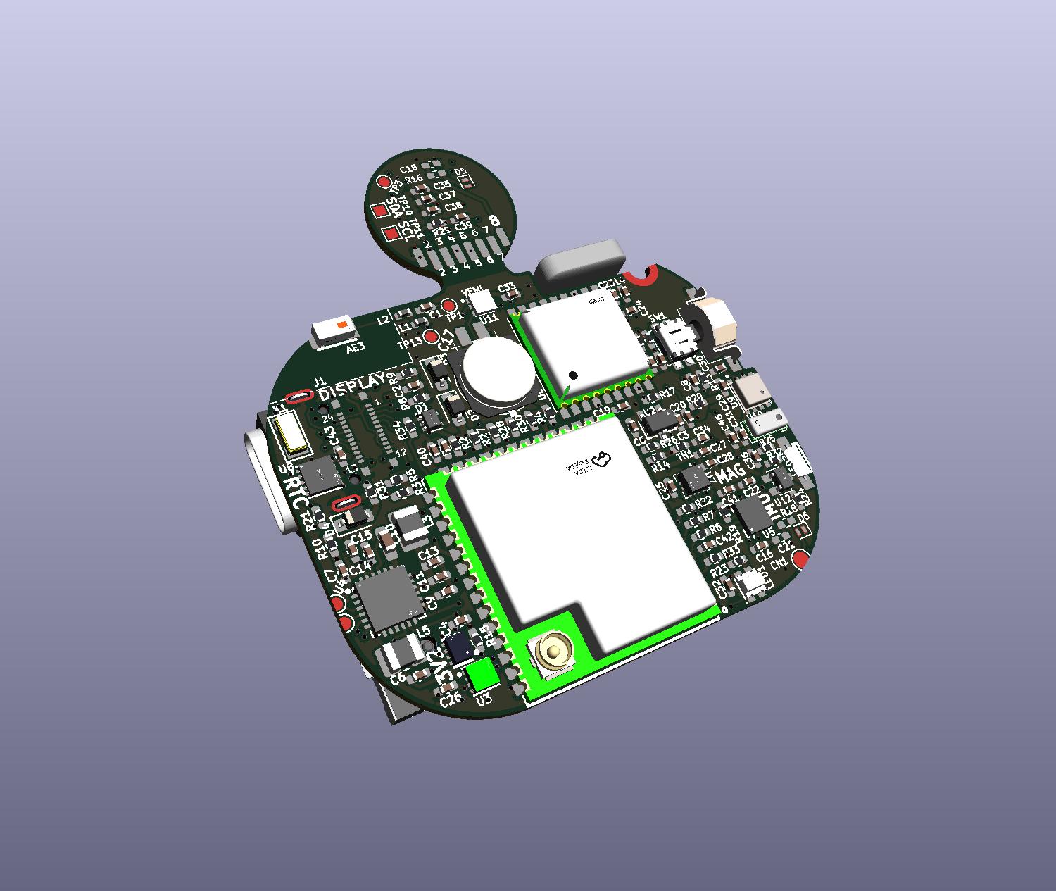
docs/img/development/7_mk1b_3d_render.jpeg
