porupski/kompic-wearable/docs/img/development/9_gps_bodge.jpeg

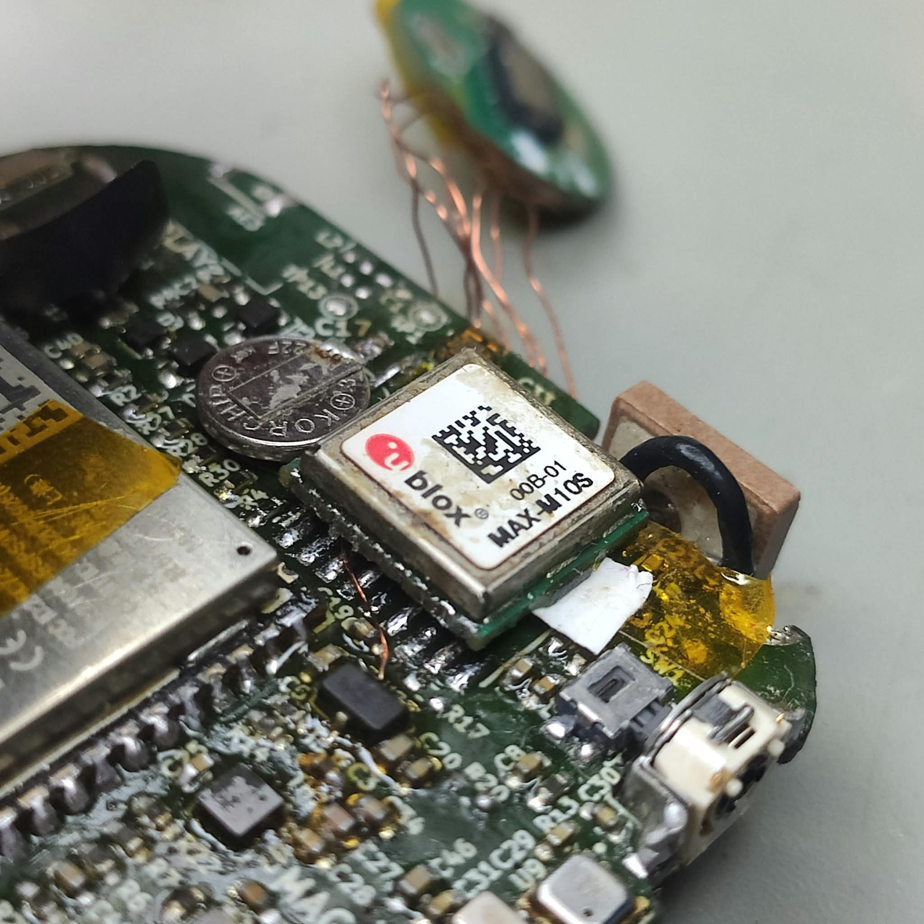
docs/img/development/9_gps_bodge.jpeg
