porupski/kompic-wearable/docs/img/development/11_mk1b_layout_b.jpeg

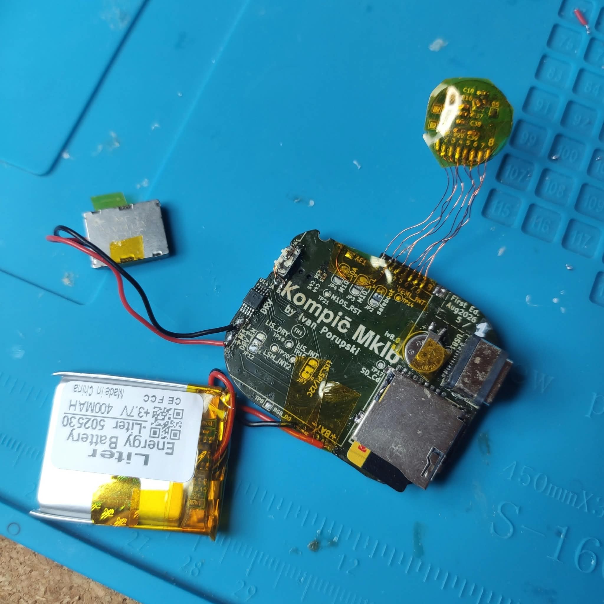
docs/img/development/11_mk1b_layout_b.jpeg
