porupski/kompic-wearable/docs/img/development/12_mk1b_packed.jpeg

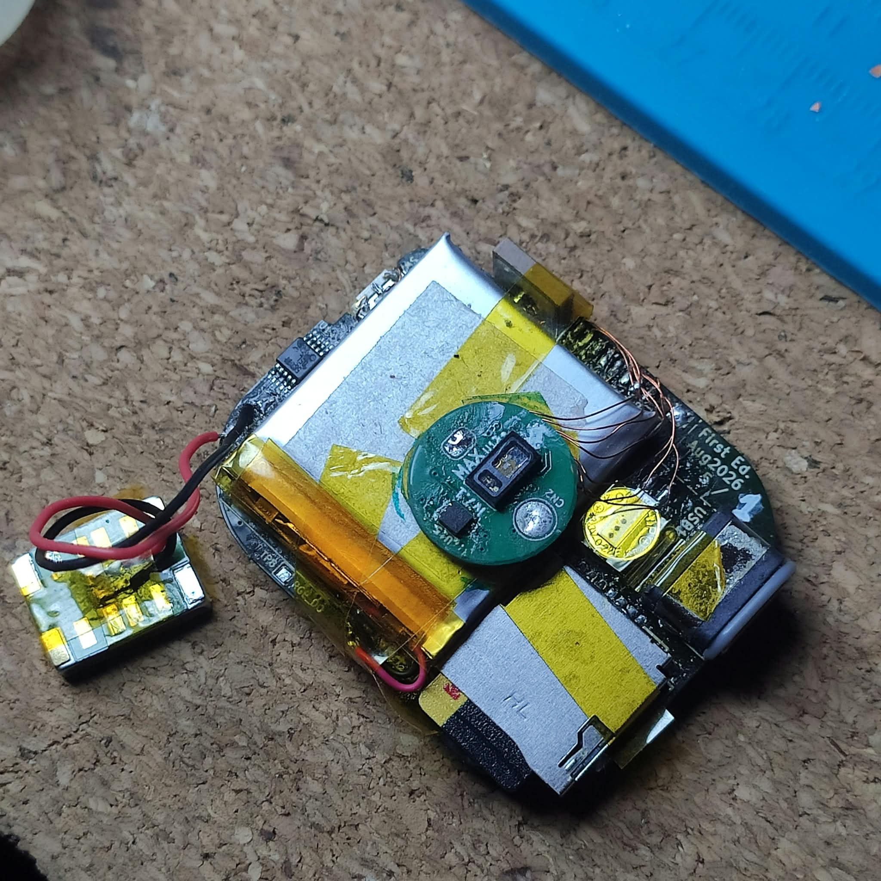
docs/img/development/12_mk1b_packed.jpeg
