porupski/kompic-wearable/docs/img/development/13_adding_display.jpeg

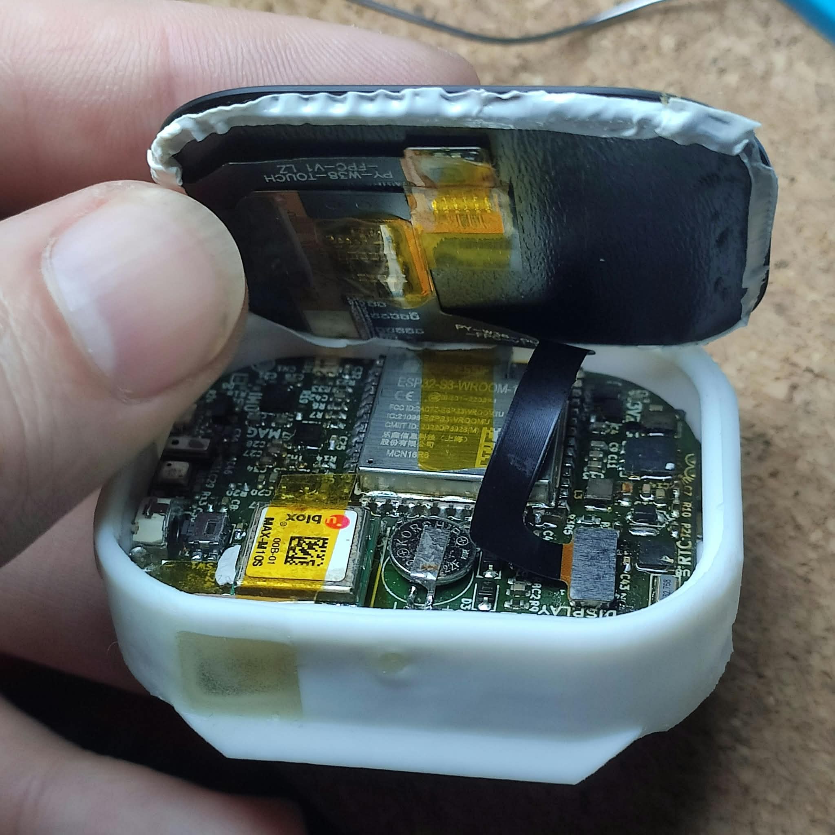
docs/img/development/13_adding_display.jpeg
