porupski/kompic-wearable/docs/img/Kompic_3D_demo_Back_v1.jpeg

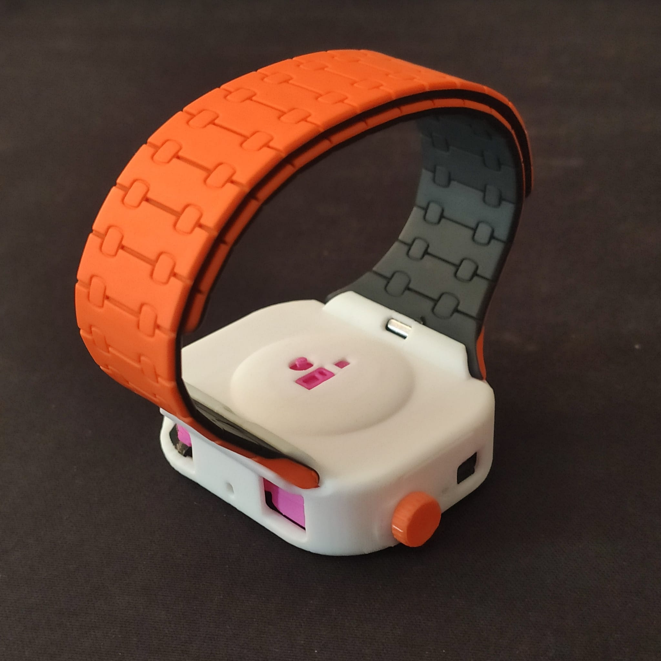
docs/img/Kompic_3D_demo_Back_v1.jpeg
