porupski/kompic-wearable/docs/img/Kompic_Mk1b_Back_v1.jpeg

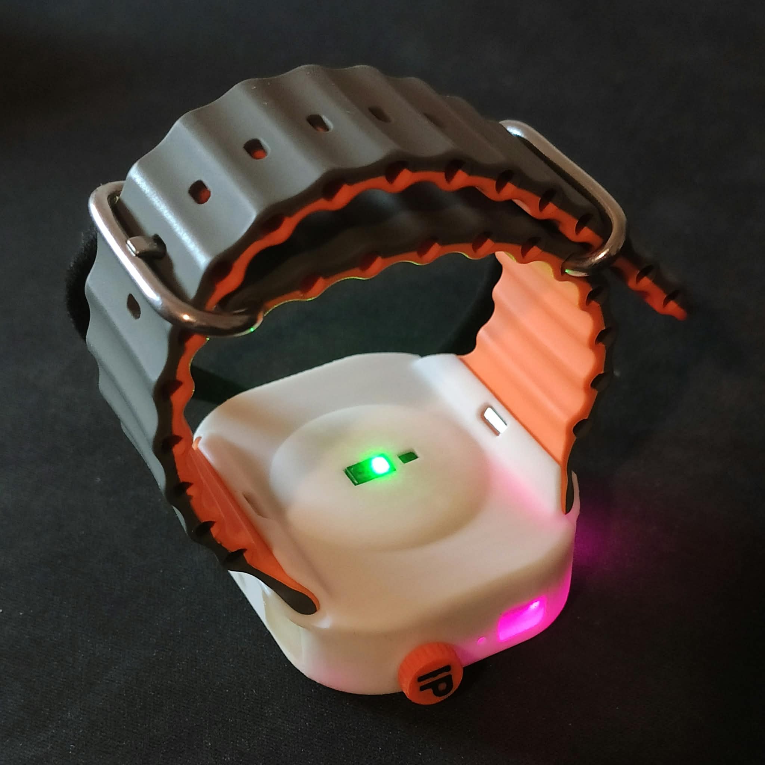
docs/img/Kompic_Mk1b_Back_v1.jpeg
