porupski/kompic-wearable/docs/img/Kompic_Mk1b_Front_v1.jpeg

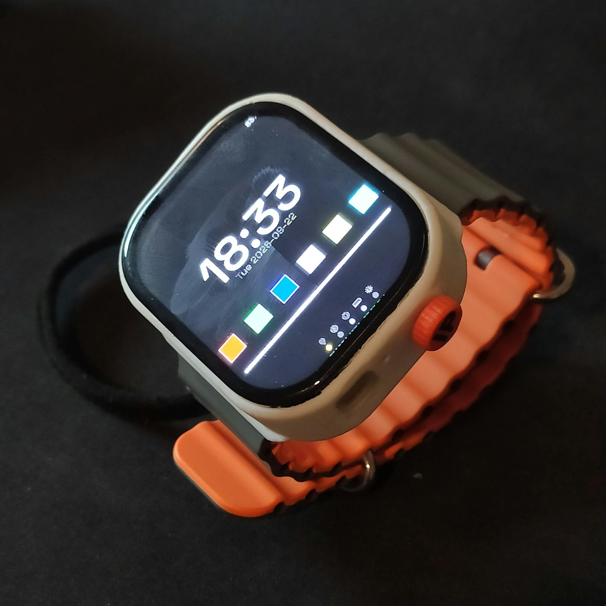
docs/img/Kompic_Mk1b_Front_v1.jpeg
