porupski/kompic-wearable/docs/img/pcb_Kompic_Mk1_iv7.1_L1_top.png

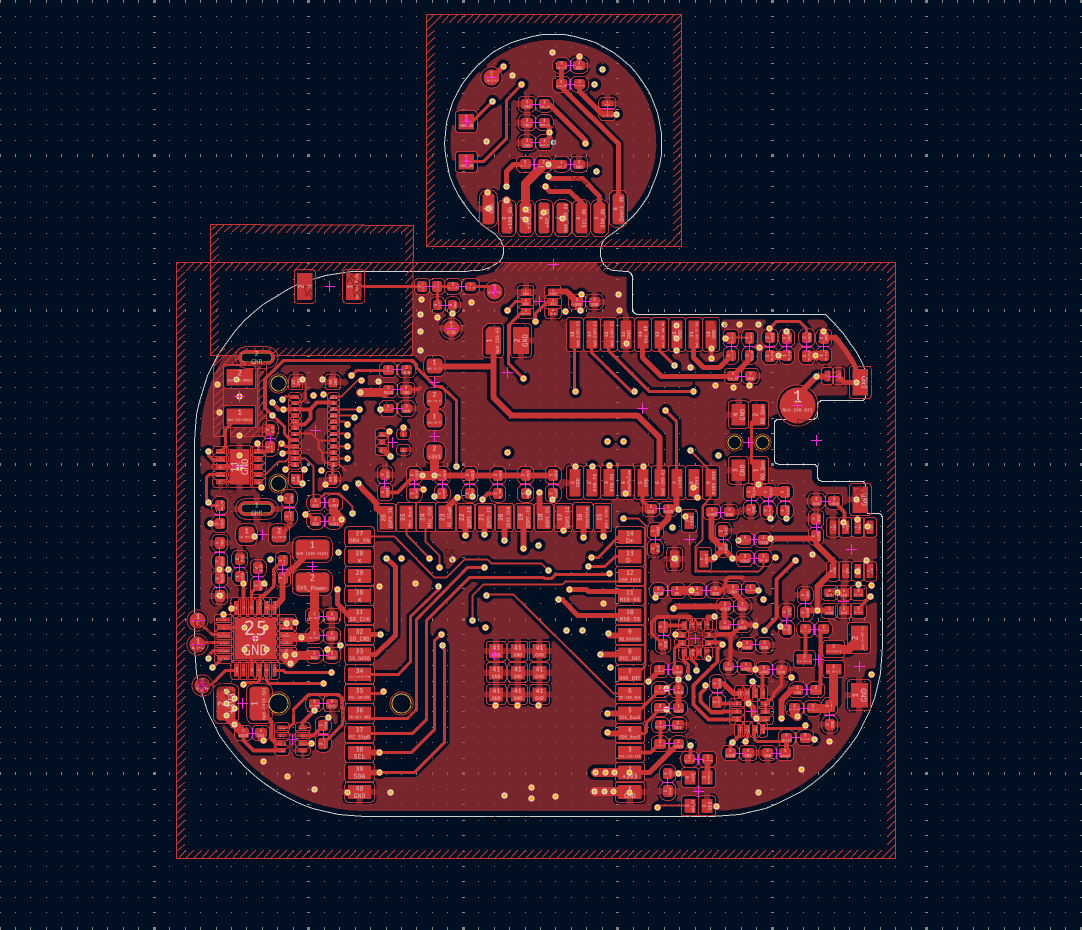
docs/img/pcb_Kompic_Mk1_iv7.1_L1_top.png
