porupski/kompic-wearable/docs/img/pcb_Kompic_Mk1_iv7.1_L4_bottom.png

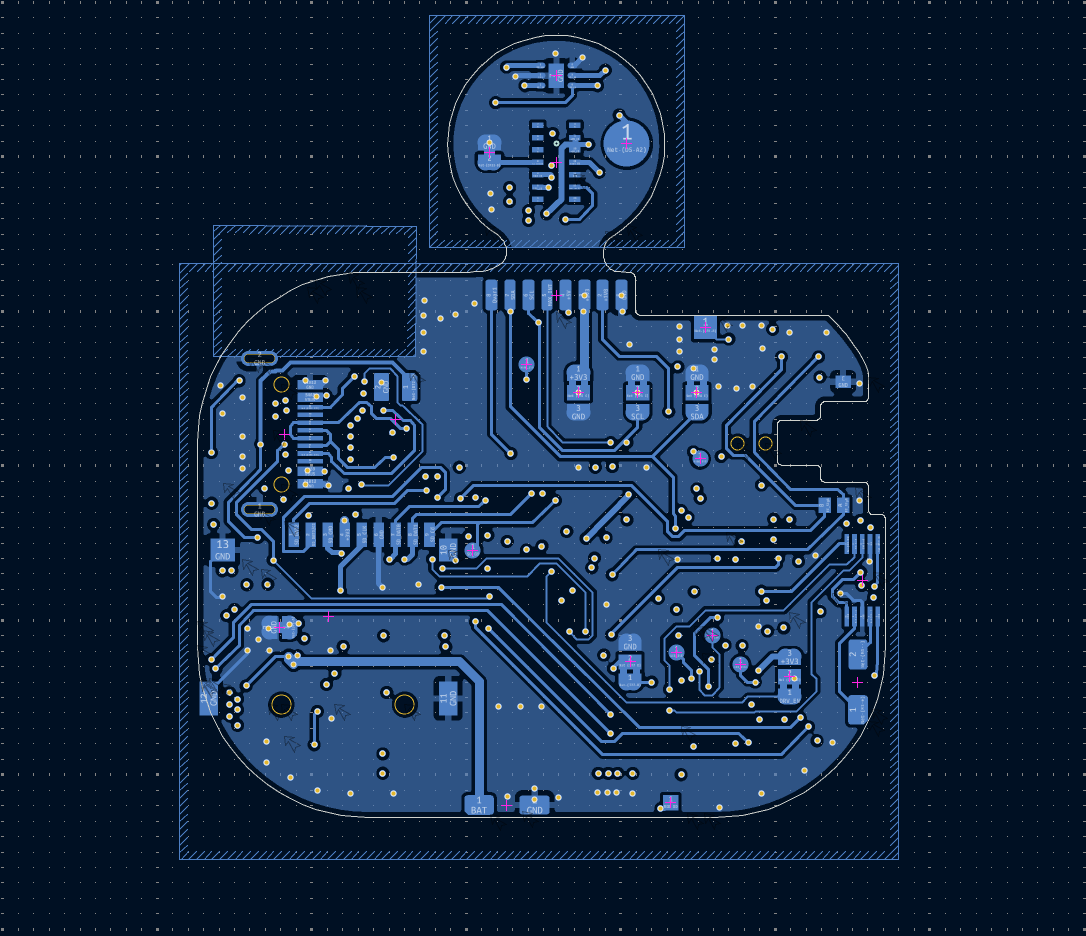
docs/img/pcb_Kompic_Mk1_iv7.1_L4_bottom.png
