porupski/kompic-wearable/docs/build_info/Mk1b_build_reports/Stage_32_Mk1b_Tile_Subject_Sweep.md

# Stage 32 -- Mk1b bulk tile -> subject conversion

**Date opened:** 2026-09-18
**Date closed:** (open)
**Board:** Mk1b iv8.0.
**Firmware baseline:** 0.4.87 (Stage 31 close: env + gps tiles are
subject-bound, drawer is a sibling pane, shared pane style + drain
timer + observer plumbing all in place).
**Status:** OPEN, ready to start in a fresh session.

**Companion refs:**
`docs/build_info/reference_files/lvgl_9/LVGL9_Kompic_Architecture.md`
(architecture spec), `Stage_31_Mk1b_LVGL_Foundations_Rebuild.md`
(the foundations that make this stage a mechanical sweep instead
of design work).

---

## 1. Why this stage exists

Stage 31 landed the LVGL 9 idioms and proved them on env (pilot,
labels-only) and gps (worst case, two-way switch + photo overlay +
robust status). Every other tile still uses the pre-Stage-31 poll
pattern (per-tile `update()` that reads broker + snprintfs into
labels every 200 ms).

This stage does the mechanical sweep: convert the remaining seven
tiles to `lv_subject_t` bindings, bring each layout inside the
corner-safe zone with bigger fonts, and shrink each tile's
`update()` to residual state (button feedback timers, one-shot
transitions). Nothing here changes hardware behavior.

## 2. Scope

Four batches, similar-shape tiles grouped for one-flash amortisation:

| Batch | Tiles | Theme | LOC pre |
|---|---|---|---|
| 32.1  | `imu_tile` + `compass_tile` | Motion sensors, read-only | 369 + 387 |
| 32.2  | `haptic_tile` + `light_tile` | UI-driven params (sliders, waveform pick) -- exercises two-way binding beyond gps power toggle | 471 + 537 |
| 32.3  | `health_tile` + `battery_tile` | PPG/BCG strings + smallest tile | 367 + 176 |
| 32.4  | `system_tile` + `rtc_tile` | NVS-driven, non-sensor producer shape | 290 + 300 |

Total ~2900 LOC touched. Each batch is one Opus session + one flash
cycle per [[feedback_flash_per_checkpoint]]. Wall-clock ~1-2 weeks.

## 3. Per-batch template

Every tile in every batch follows the same three-step recipe (proven
on env in 31.2 + gps in 31.4a):

**Step A -- extend ui_subjects.**
Add string subjects for value labels + int subjects for LED status /
toggles / mode indicators. Owned queue for the producer domain if not
already present. Buffer pairs behind `xxx_STR_BUF_LEN` macro.

**Step B -- producer publishes.**
After `broker_xxx_write()`, add `xQueueOverwrite(g_xxx_q, &sample)`.
When the producer task early-outs on `!enabled`, push a "disabled"
sample so the tile status reflects immediately (bme688 / max_m10s
pattern).

**Step C -- rewrite the tile.**
- Corner-safe layout: 60 px H pad, 40 px V pad for interactive
  elements per [[project_display_corner_cutoff]].
- Bigger font: `UI_FONT_TITLE` (28 px) for data rows, `UI_FONT_LABEL`
  (20 px) for chips. If 28 px still feels small, generate a 40 px
  face per [[feedback_lv_font_conv_flags]].
- Labels bind via `lv_label_bind_text(lbl, &subj_xxx_str, NULL)`.
- Switches bind via `lv_obj_bind_checked(sw, &subj_xxx_enabled)`
  with an `obs_xxx_enabled_to_broker` observer in ui_subjects.c
  (two-way).
- Sliders / mode pickers: same pattern, `lv_obj_bind_value` or
  event cb -> subject -> observer -> broker.
- `tile_update()` shrinks to LED colour + button feedback timeout.
- Header text is chip-name only (no chip-desc). Optional short
  descriptor as chip beneath status line.

**Step D -- fw bump + stage log.**
Standard per-batch flash summary.

## 4. Batch details

### 4.1 -- Batch 32.1 (imu_tile + compass_tile)

Same shape as env: multi-row read-only sensor data + status LED +
power toggle. No sliders, no photo view, no fancy interactions --
easy first sweep to burn in the muscle memory.

- IMU subjects: `subj_imu_accel_str`, `subj_imu_gyro_str`,
  `subj_imu_temp_str`, `subj_imu_activity_str`, `subj_imu_status`,
  `subj_imu_enabled`.
- Compass subjects: `subj_mag_field_str`, `subj_mag_bearing_str`,
  `subj_mag_hdop_str`, `subj_mag_calstate_str`, `subj_mag_status`,
  `subj_mag_enabled`.
- Producers: `lsm6dsv16x` + `lis3mdl` -- push to `g_imu_q` + `g_mag_q`.

Bench watch: tile shows live accel / gyro / mag values, LED tracks
status, power toggle works via bind_checked. Then flip theme, verify.

### 4.2 -- Batch 32.2 (haptic_tile + light_tile)

**Beyond env/gps:** these tiles have UI-DRIVEN parameters, not just
read-only sensor values. Haptic has waveform pick (dropdown / roller);
light has brightness slider + auto-brightness toggle.

- New two-way pattern to exercise: `lv_slider_bind_value` +
  observer -> `broker_light_set_manual_brightness`.
- Haptic waveform: `lv_dropdown_bind_value` + observer ->
  `haptic_set_ui_effect`.
- Blue-light toggle: `lv_obj_bind_checked` -> broker.
- If any of the widget-side binds don't have a stock LVGL 9 helper
  (e.g. `lv_slider_bind_value` might not exist yet), add a small
  observer + LV_EVENT_VALUE_CHANGED cb pair -- same shape as the
  gps two-way switch.

Bench watch: drag brightness slider, watch AMOLED backlight change
in real time. Tap waveform picker, feel the haptic play.

### 4.3 -- Batch 32.3 (health_tile + battery_tile)

Health: PPG (heart rate) + BCG derived. Currently poll-based. Add
subjects for HR bpm + PPG signal quality + BCG SNR. Producer is
`max30101` task + a bcg derivation step.

Battery: smallest tile in the tree. Read-only percent + charging
icon. Likely lands as a bonus during health's bench cycle.

### 4.4 -- Batch 32.4 (system_tile + rtc_tile)

**Different producer shape:** these read from NVS + uptime + PMU
locks + RTC registers, NOT from a sampling sensor task. Validates
that the drain pattern works for on-demand producers too.

- System tile: uptime, heap, PSRAM, cpu freq, current mode.
  Producer? Add a small `system_metrics` snapshot task that
  periodically pushes to `g_system_q`.
- RTC tile: wall time, wake alarm, RAM byte state. Producer =
  `pcf85063` task (already exists, add queue push).

## 5. Non-goals

- Alarm as sibling pane / delete `ui_navigation.c` -- Stage 33.1.
- Delete every tile's `apply_theme()` cb + delete `apply_ui_theme`
  fan-out loop -- Stage 33.3.
- Shutdown overlay -> `lv_msgbox` -- Stage 33.2.
- Delete update-cb from tile_registry contract -- Stage 33.3 (needs
  every tile's `update()` to be truly no-op first, which this stage
  gets us to).
- New GPS diagnostics / dynamic-model expansion -- 31.4 already
  covered the immediate wins; anything more waits on bench hw fix.
- Encoder INTERMITTENT recovery -- separate stage,
  [[project_encoder_dead_on_iv80]].
- i2c_master API migration -- separate stage, blocker for
  [[project_i2c_hw_fsm_reset_crash]].

## 6. Definition of done for Stage 32

1. All seven remaining tiles are subject-bound; each `tile_update()`
   is <= 40 lines (LED + feedback + residual).
2. All seven tiles use corner-safe layout (60 H / 40 V pads,
   `UI_FONT_TITLE` for data rows).
3. Each tile's producer pushes to `g_xxx_q` including the "disabled"
   snapshot path.
4. `ui_subjects.c` grows to ~15 domains but the drain-cb is still
   a simple round-robin queue check.
5. Bench: every tile displays live data (or a coherent
   "no data"/"disabled" status), power toggles work, theme swap
   works, no LVGL asserts.

## 7. Bench log

### 7.1 -- Batch 32.1 flash (fw 0.4.88)

**What landed:**
- `ui_subjects.{c,h}`:
  - New IMU domain: 10 string subjects (accel x/y/z, gyro x/y/z, roll,
    pitch, temp, status) + 1 int (`subj_imu_enabled`) + `g_imu_q`
    queue. Formatter `imu_format_and_publish()` builds a status line
    from `broker_imu_hw_alive/get_status/get_enabled` and blanks the
    numeric labels on disabled/offline paths. Two-way observer
    `obs_imu_enabled_to_broker` writes broker on subject change (drain
    mirrors broker->subject the following tick).
  - New MAG domain: 4 string subjects (xyz, heading, cardinal, cal-btn)
    + 1 int (`subj_mag_enabled`) + `g_mag_q` queue. Formatter derives
    xyz + heading text from data + status; cal-button label reflects
    `d.calibrating` / `d.cal_countdown`. Two-way observer for the
    power switch.
  - Init log line updated to `env(5) + gps(9 str + 2 int) + imu(10
    str + 1 int) + mag(4 str + 1 int) subjects created; g_env_q +
    g_gps_q + g_imu_q + g_mag_q up`.
  - Drain cb extended with `xQueueReceive` branches for both queues
    (round-robin; each queue is depth-1 overwrite).
- `lsm6dsv16x.c` `task_imu_fn`:
  - Includes `ui_subjects.h`.
  - After `broker_imu_write(&bd)` -> `xQueueOverwrite(g_imu_q, &bd)`.
  - On `!enabled` early-out, push a one-shot "disabled" snapshot (edge-
    detected via `s_prev_pushed_disabled`) so the tile flips to
    "Disabled" instantly without waiting for re-enable.
- `lis3mdl.c` `task_mag_fn` + `task_mag_cal_fn`:
  - Includes `ui_subjects.h` + `freertos/queue.h`.
  - After every `broker_mag_write` (main + 3 calibration paths + cancel
    path) -> `xQueueOverwrite(g_mag_q, &bd)`.
  - On `!enabled` early-out in task_mag_fn, push one "disabled"
    snapshot (edge-detected).
- `lis3mdl/CMakeLists.txt`: added `lvgl_ui` to REQUIRES (matches
  lsm6dsv16x + bme688 pattern).
- `imu_tile.c` rewrite:
  - Corner-safe 60H/40V layout (matches env/gps convention).
  - Header text is chip-name only (`lsm6dsv16x_get_chip_name()`);
    chip-desc dropped per LOG.md 2026-09-18 note.
  - All 9 value labels + status label bound via `lv_label_bind_text`.
  - Power switch bound via `lv_obj_bind_checked(&subj_imu_enabled)`.
    Deleted `cb_power()` + `s_syncing_power` guard entirely.
  - `imu_tile_update()` shrunk from ~90 lines to ~20 -- LED colour +
    status-label semantic colour only. All text updates drain-driven.
  - `apply_theme()` still recolours labels + parent bg (Stage 33.3
    deletion scope).
- `compass_tile.c` rewrite:
  - Corner-safe 60H/40V layout.
  - Header text chip-name only.
  - XYZ / heading / cardinal / cal-button labels bound via
    `lv_label_bind_text`. Cal-button label auto-flips
    "CALIBRATE" <-> "CAL 15s" via drain (no snprintf in tile).
  - Power switch bound via `lv_obj_bind_checked(&subj_mag_enabled)`.
    Deleted `cb_power_toggle()` + `s_syncing` guard entirely.
  - `compass_tile_update()` keeps only: LED colour, heading+cardinal
    colour semantic tint, needle rotation (transform_angle), and
    cal-button colour + enable state. All text drain-driven.
- `firmware_version.h`: 0.4.87 -> 0.4.88.

**Local build:** clean. 0x14f780 B, 56% partition free (was 57% at
Stage 31 close; extra ~4 KB from IMU + MAG subject buffers + formatters).

**What to watch on flash:**
1. Boot log:
   - `UI_SUBJ: init: env(5) + gps(9 str + 2 int) + imu(10 str + 1 int)
     + mag(4 str + 1 int) subjects created; g_env_q + g_gps_q +
     g_imu_q + g_mag_q up` (once)
   - `IMU_TILE: LSM6DSV16X tile init OK (subject-bound)` (once)
   - `COMPASS_TILE: LIS3MDLTR tile init OK (subject-bound)` (once)
2. Swipe to IMU tile:
   - Initial state: labels show `X: ---` etc. Switch reflects broker.
   - Turn switch ON via tap: `UI_SUBJ: imu switch ->
     broker_imu_set_enabled(1)` at DEBUG. Within one drain tick
     (~200 ms), status flips to "Online" + all 9 value labels
     populate. Roll/Pitch track wrist orientation.
   - Turn switch OFF: within one drain tick, status = "Disabled",
     all numeric labels = "---". No lag waiting for re-enable.
3. Swipe to Compass tile:
   - Same shape. Switch tap toggles via bind_checked + observer.
   - When enabled, XYZ + heading + cardinal populate. Needle rotates
     as the board turns.
   - Tap CALIBRATE (when enabled) -> label shows "CAL 30s" counting
     down. Rotate the board in a figure-8. Countdown drives the label
     text via drain -- no per-tile snprintf.
4. Theme swap on System tile:
   - IMU + Compass value labels + headers recolour via surviving
     apply_theme (Stage 33.3 sweep will delete these).
5. Regression:
   - Env tile still populates when its switch is on.
   - GPS tile still shows status line + subject-driven labels.
   - Drawer opens on swipe-up, closes on swipe-down.
6. No new E-lines from LVGL about observer/mutex, no
   `queue_trans failed`, no assert about un-initialised subject.

**If something's off, useful escalation:**
- `esp_log_level_set("UI_SUBJ", ESP_LOG_DEBUG)` -> per-drain
  `imu sample consumed` / `mag sample consumed` ticks + switch
  observer messages.
- `esp_log_level_set("UI_SUBJ", ESP_LOG_VERBOSE)` -> per-write
  `imu published: ax=... gx=... roll=... enabled=1` firehose.

**Bench verdict:** *(fill in after flash)*

## 8. Next-steps hook -- Stage 33

**Stage 33 -- structural finish** (~3 batches):
- 33.1: alarm as sibling pane; delete the alarm branch of
  `ui_navigation.c`; delete `ui_navigation.c` entirely if empty.
- 33.2: shutdown overlay -> `lv_msgbox` on `lv_layer_top()`; audit
  lock overlay + notification overlay layer usage.
- 33.3: delete every tile's `apply_theme()` cb; delete
  `apply_ui_theme` fan-out loop; delete `broker_xxx_read()` sensor
  accessors (queue is now private to drain timer); delete
  tile `update` cbs from registry contract.

After Stage 33 close, the LVGL 9 rebuild is done end-to-end.

## 9. References

- Stage 31 close doc: `Stage_31_Mk1b_LVGL_Foundations_Rebuild.md`
- LVGL 9 architecture spec:
  `docs/build_info/reference_files/lvgl_9/LVGL9_Kompic_Architecture.md`
- Corner-safe zone rule: [[project_display_corner_cutoff]]
- Font conversion: [[feedback_lv_font_conv_flags]]
- Flash cadence: [[feedback_flash_per_checkpoint]]
- Venue batching: [[feedback_group_work_by_venue]]
- Active-tile-at-Col-1 workflow: [[feedback_active_tile_at_col_1]]
- CLI-first testability: [[feedback_cli_first_testability]]
- Log tiering: [[feedback_esp_log_verbosity_practice]]
- MD frontmatter convention: [[feedback_md_frontmatter_convention]]
