porupski/kompic-wearable/docs/build_info/Mk1_build_reports/Stage_11_PM_Plan.md

# Stage 11 Item D — Power management implementation plan

Baseline to beat: **106 mA** at USB with `batt_test=1` (sensors parked, LEDs blipping every 10 s, RTC + BQ25619 + ESP core running). Battery-life run in progress from `/sd/data/battery/batt_0025.csv`.

This plan is written to survive a re-flash cycle: keep `batt_test=1` as the measurement mode. Each numbered block below is meant to land as a separate small commit + retest so we can attribute the delta.

---

## 1. Current sinks (what's drawing at baseline)

At 106 mA @ ~4.15 V ≈ 440 mW. Order-of-magnitude breakdown (rough — needs profiler validation, but useful to prioritise):

| Sink | Rough share | Notes |
|---|---|---|
| ESP32-S3 CPU @ 240 MHz active (never idle) | ~40-60 mA | Field-capture task's 5 ms poll = no light-sleep opportunity |
| WS2812 quiescent when off | ~1-2 mA | 50 ms cyan blip every 10 s adds ~0.1 mA average |
| BQ25619 running + I2C 1 Hz | ~1 mA | Small |
| PCF85063 + coin cell trickle | ~µA | Negligible |
| USB peripheral (Serial-JTAG active) | ~10-15 mA | Non-trivial — JTAG is polled by the RTC-CLI task |
| SDMMC host (mounted, idle) | ~5-10 mA | Currently kept mounted for the battery-test CSV writes |
| Regulator quiescent + LDOs | ~5-10 mA | Board-level, can't do much in firmware |

**The big pot: CPU active time. Everything else is small.**

---

## 2. The four blocks — ordered by effort × value

### Block A — Enable PM + tickless + DFS  (small; sets the stage)

**sdkconfig deltas (to be clicked, mirrored to `sdkconfig.defaults`):**
```
CONFIG_PM_ENABLE=y
CONFIG_PM_DFS_INIT_AUTO=y                    # DFS on from boot
CONFIG_FREERTOS_USE_TICKLESS_IDLE=y          # required for auto-light-sleep
CONFIG_FREERTOS_IDLE_TIME_BEFORE_SLEEP=3     # tick threshold (3 = 30 ms @ 100 Hz)
CONFIG_PM_SLP_IRAM_OPT=y                     # place sleep hooks in IRAM
CONFIG_PM_RTOS_IDLE_OPT=y
```

`esp_pm_config_t` set at boot:
```c
esp_pm_config_t pm = {
    .max_freq_mhz  = 240,     // CPU when active
    .min_freq_mhz  = 40,      // CPU when DFS decides to drop
    .light_sleep_enable = true,
};
esp_pm_configure(&pm);
```

**Expected delta on its own:** small (~5-15 mA) because the field-capture task's 5 ms tick prevents light-sleep from ever engaging. Real wins require Block B first.

**Risks:** PM locks are needed by any driver that requires a fixed frequency (RMT for WS2812, SDMMC clock, PDM mic, I2S). Every existing "just polls" driver is safe. The dodgy paths are RMT (LED) and PDM (mic). Both need `ESP_PM_APB_FREQ_MAX` locks around active use.

### Block B — Field-capture task: event-driven wake  (medium; the big win)

**Current problem:** `task_field_capture_fn` spins `POLL_TICK_MS = 5 ms` regardless of activity. In STANDBY that's 200 wake-ups/s that block light-sleep.

**Approach:**
- Keep the 5 ms poll only when we've seen encoder or button activity in the last ~2 seconds ("active window").
- After 2 s of no input, drop to 50 ms poll AND set up ESP_SLEEP_EXT1 wake sources for GPIO16 (button), GPIO21 (enc A), GPIO43 (enc B). Any edge wakes us.
- LSM tap-Z can also be a wake source (INT1 on GPIO8) — see Stage 10 §9 line about wake-on-motion.

**Concrete code changes:**
1. Add `s_input_active_until_ms` — bumped to `now + 2000` on any encoder/button event.
2. In the task loop, choose `vTaskDelay(pdMS_TO_TICKS(now < s_input_active_until_ms ? 5 : 50))`.
3. In `field_capture_init()`, `esp_sleep_enable_ext1_wakeup(1 << PIN_BUTTON | 1 << PIN_ENC_A | 1 << PIN_ENC_B, ESP_EXT1_WAKEUP_ANY_LOW)`. Note ESP32-S3 EXT1 needs RTC-capable GPIOs — verify all three qualify.
4. Encoder polling remains software (feedback_encoder_polling.md prohibits ISR), but the wake trigger is fine — first tick after wake resumes the state machine cleanly.

**Expected delta:** with tickless idle actually engaging in STANDBY, ~40-60% baseline reduction is plausible. Rerun `batt_test=1` → target **≤50 mA baseline**.

**Risks:**
- Encoder state machine (feedback_encoder_polling.md) needs 15 ms detent-rest confirmation. 50 ms poll means edge-of-edge cases could miss a detent — the wake-on-any-edge should catch the leaving-rest transition and re-enter 5 ms poll immediately, but this needs bench verification.
- Any recording session needs the fast poll — extend `s_input_active_until_ms` for the whole recording, not just per-input.
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
