porupski/kompic-wearable/docs/build_info/Mk1_build_reports/Stage_8_Re-Blueprinting.md

# Stage 8 Re-Blueprinting — Kompic iv8.0

**Date opened:** 2026-07-13
**Basis:** Stage 7 Field Report (2026-07-12 → 2026-07-13). iv7.1 declared current-canon in Stage 7 § 13; this document defines **iv8.0** — the first fixed spin. When iv8.0 is fabricated and a working unit exists, that unit becomes **Kompic Mk II** — but this doc is only about the schematic / BOM / layout deltas required to *get* to Mk II from iv7.1.
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
