porupski/kompic-wearable/docs/build_info/aux_scripts/battery/battery_analysis.png

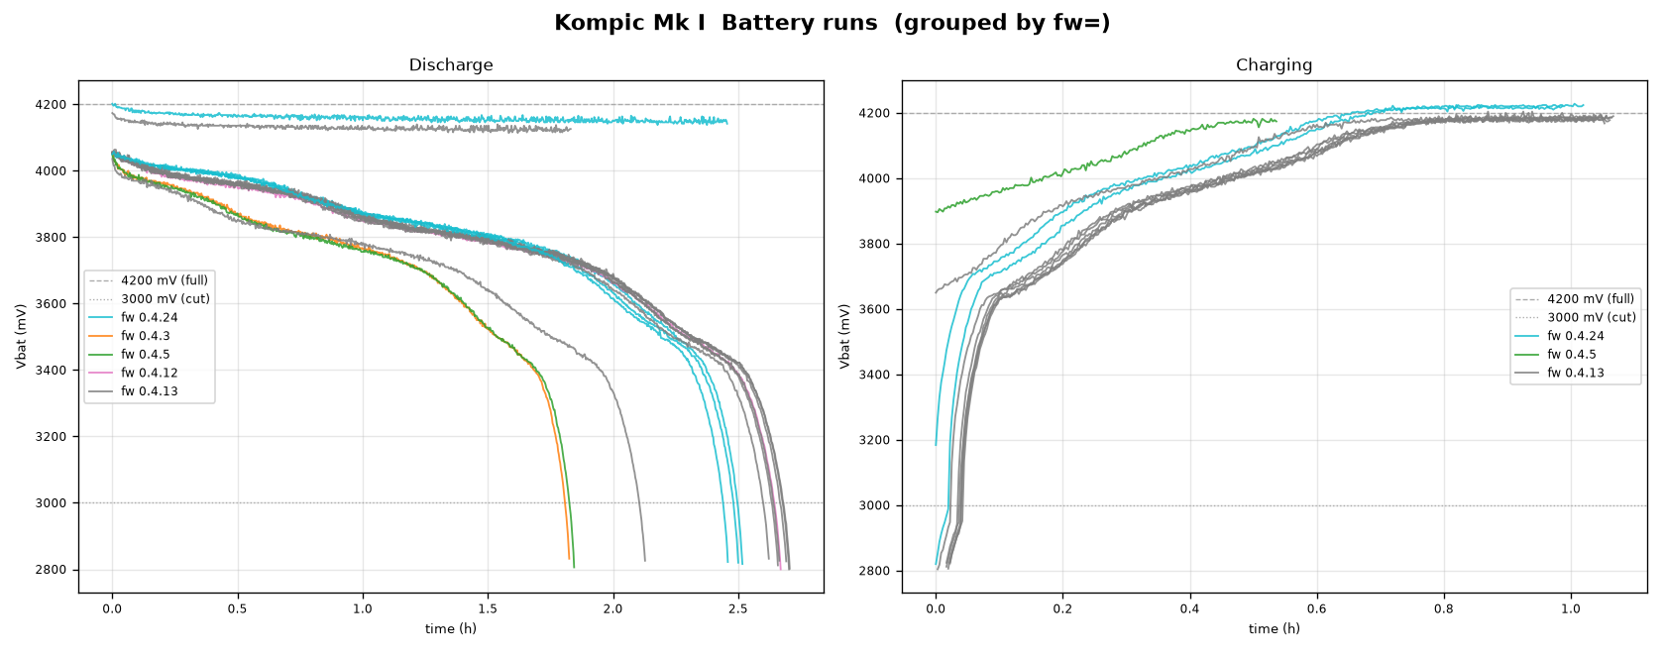
docs/build_info/aux_scripts/battery/battery_analysis.png
