porupski/kompic-wearable/docs/img/development/5_3d_print_iterations.jpeg

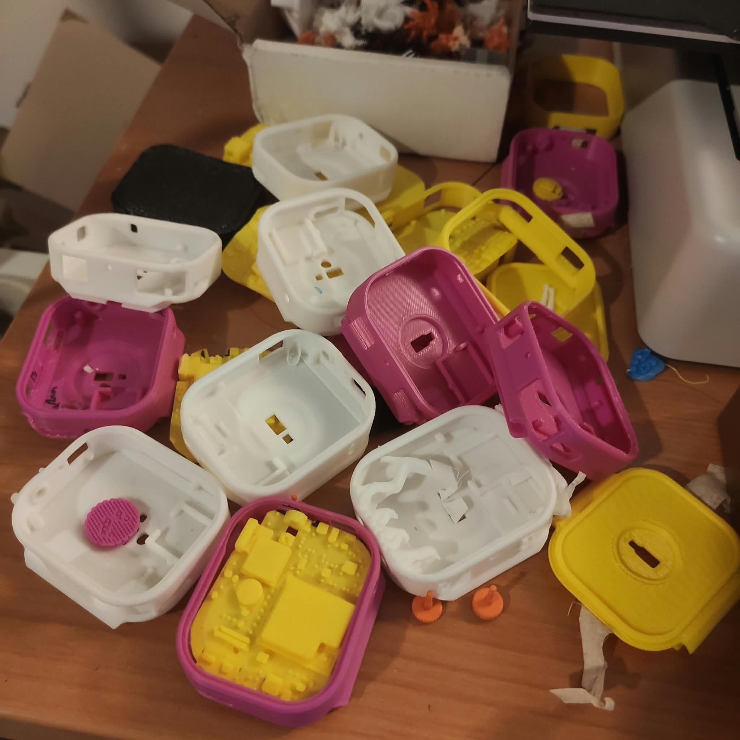
docs/img/development/5_3d_print_iterations.jpeg
