porupski/kompic-wearable/firmware/esp-idf/components/bq25619/bq25619.c

/**
 * @file bq25619.c
 * @brief TI BQ25619 driver implementation.
 *
 * See bq25619.h for design notes. This file:
 *   - Wraps the I2C register I/O on bus 1 (I2C_NUM_1) under g_i2c2_mutex --
 *     the SAME mutex the DRV2605 driver takes. Stage 20 fix: was
 *     g_i2c_mutex (bus 0) which protected the wrong physical bus. See
 *     Stage_20_Button_Responsiveness.md.
 *   - Decodes REG_STATUS / REG_FAULT into the broker payload.
 *   - Provides a voltage-LUT SoC mapper + a self-learning observation hook
 *     (stub today; structurally ready for NVS-persisted curve fitting).
 *   - Implements ship-mode entry via REG_MISC.BATFET_DIS with BATFET_DLY
 *     cleared so BATFET disconnects immediately (default ~10 s delay).
 *
 * Most register addresses + bit positions are tagged [DSV] (datasheet-verify)
 * pending a bench session with the BQ25619 datasheet in hand. Conservative
 * defaults are used everywhere; see [DEFECT-001] in the porting .md.
 *
 * Core 0 only.
 */

#include "bq25619.h"
#include "data_broker.h"
#include "max17048.h"
#include "boot_hw_init.h"    // g_i2c1_bus_handle (Stage 35.2 i2c_master migration)
#include "boot_power.h"      // g_display_sleep -- skip poll while display off
#include "driver/i2c_master.h"
#include "esp_log.h"
#include "esp_timer.h"
#include "freertos/FreeRTOS.h"
#include "freertos/task.h"
#include "freertos/semphr.h"
#include <string.h>

extern SemaphoreHandle_t g_i2c2_mutex;

static const char *TAG = "BQ25619";

// -- I2C device handle (Stage 35.2) -------------------------------------------
// Added to g_i2c1_bus_handle in bq25619_init(); all subsequent register I/O
// goes through this handle. The i2c_port_t param on the public API is kept
// for signature compatibility but ignored inside the driver.
static i2c_master_dev_handle_t s_bq_dev = NULL;

#define BATTERY_POLL_MS  1000   // 1 Hz -- spec is "polled via I2C"; faster wastes the bus

// -- Identity -----------------------------------------------------------------
const char *bq25619_get_chip_name(void) { return "BQ25619"; }
const char *bq25619_get_chip_desc(void) { return "Li-ion charger + PMID boost"; }

// =============================================================================
// I2C primitives (caller holds g_i2c2_mutex -- shared with DRV2605 on bus 1)
// =============================================================================

esp_err_t bq25619_read_reg(i2c_port_t i2c_num, uint8_t reg, uint8_t *val)
{
    (void)i2c_num;
    if (!val) return ESP_ERR_INVALID_ARG;
    if (!s_bq_dev) return ESP_ERR_INVALID_STATE;
    return i2c_master_transmit_receive(s_bq_dev, &reg, 1, val, 1, 20);
}

esp_err_t bq25619_write_reg(i2c_port_t i2c_num, uint8_t reg, uint8_t val)
{
    (void)i2c_num;
    if (!s_bq_dev) return ESP_ERR_INVALID_STATE;
    uint8_t buf[2] = { reg, val };
    return i2c_master_transmit(s_bq_dev, buf, 2, 20);
}

esp_err_t bq25619_read_vbat_mv(i2c_port_t i2c_num, uint16_t *vbat_mv_out)
{
    if (!vbat_mv_out) return ESP_ERR_INVALID_ARG;
    *vbat_mv_out = 0;

    uint8_t raw = 0;
    esp_err_t ret = bq25619_read_reg(i2c_num, BQ25619_REG_VBAT_ADC, &raw);
    if (ret != ESP_OK) return ret;

    // [DSV] Family convention: VBAT_ADC step ~20 mV, offset ~2304 mV.
    // BQ25619 datasheet may use different scaling -- confirm and refine.
    // Output range with these constants: 2304..7404 mV (12 mV per LSB if 8-bit).
    // We use a more conservative 20 mV step and 2304 mV offset; refine later.
    *vbat_mv_out = (uint16_t)(2304U + 20U * (uint16_t)raw);
    return ESP_OK;
}

// =============================================================================
// SoC: voltage LUT + self-learning observation hook
// =============================================================================

// First-pass LUT for a typical 3.7 V single-cell LiPo at light load.
// Concave near full, knee around 3.70-3.75 V, steep drop below 3.40 V.
// See [DEFECT-002] -- refine after bench discharge data.
static const struct { uint16_t mv; uint8_t pct; } s_soc_lut[] = {
    { 4200, 100 },
    { 4100,  90 },
    { 4000,  78 },
    { 3920,  65 },
    { 3850,  50 },
    { 3780,  35 },
    { 3700,  22 },
    { 3600,  12 },
    { 3500,   6 },
    { 3400,   2 },
    { 3300,   0 },
};

uint8_t bq25619_soc_from_mv(uint16_t mv)
{
    const int n = (int)(sizeof(s_soc_lut) / sizeof(s_soc_lut[0]));
    if (mv >= s_soc_lut[0].mv)        return 100;
    if (mv <= s_soc_lut[n - 1].mv)    return 0;

    for (int i = 1; i < n; i++) {
        if (mv >= s_soc_lut[i].mv) {
            // Linear interpolate between i-1 and i (mv: high->low, pct: high->low).
            uint16_t mv_hi  = s_soc_lut[i - 1].mv;
            uint16_t mv_lo  = s_soc_lut[i    ].mv;
            uint8_t  pct_hi = s_soc_lut[i - 1].pct;
            uint8_t  pct_lo = s_soc_lut[i    ].pct;
            uint16_t span_mv = mv_hi - mv_lo;
            uint16_t over_mv = mv - mv_lo;
            int      span_p  = (int)pct_hi - (int)pct_lo;
            int      pct     = (int)pct_lo + (span_p * (int)over_mv) / (int)span_mv;
            if (pct < 0)   pct = 0;
            if (pct > 100) pct = 100;
            return (uint8_t)pct;
        }
    }
    return 0;
}

// -- Self-learning hook (stub) -------------------------------------------------
// Today: just records observed min/max for diagnostics.
// Tomorrow: shifts the s_soc_lut endpoints based on observed cell behaviour
// and persists to NVS so the curve adapts. Hook is in place; algorithm is not.
static uint16_t s_vbat_min_mv = 0xFFFF;  // running observed minimum
static uint16_t s_vbat_max_mv = 0x0000;  // running observed maximum

void bq25619_soc_observe(uint16_t vbat_mv, bool is_charging)
{
    (void)is_charging;  // future: separate charge vs discharge curves
    if (vbat_mv == 0) return;
    if (vbat_mv < s_vbat_min_mv) s_vbat_min_mv = vbat_mv;
    if (vbat_mv > s_vbat_max_mv) s_vbat_max_mv = vbat_mv;
    // TODO: adapt s_soc_lut endpoints when min/max stabilise; persist to NVS.
}

void bq25619_soc_get_observed_extremes(uint16_t *min_mv, uint16_t *max_mv)
{
    if (min_mv) *min_mv = (s_vbat_min_mv == 0xFFFF) ? 0 : s_vbat_min_mv;
    if (max_mv) *max_mv = s_vbat_max_mv;
}

// BQ25619 REG_FAULT (0x09) NTC_FAULT bits [2:0] -- JEITA state machine output.
// This is the only TS readout the chip exposes: no numeric °C, just a zone.
// Datasheet-conventional (BQ256xx family): 000=Normal 010=Warm 011=Cool
//   101=Cold 110=Hot. If bench shows a value that doesn't fit, the [DSV]
//   tag stays valid until confirmed.
const char *bq25619_ntc_status_str(uint8_t fault_reg)
{
    switch (fault_reg & 0x07) {
        case 0x0: return "Normal";
        case 0x2: return "Warm";
        case 0x3: return "Cool";
        case 0x5: return "Cold";
        case 0x6: return "Hot";
        default:  return "?";
    }
}

// =============================================================================
// Init
// =============================================================================

esp_err_t bq25619_init(i2c_port_t i2c_num)
{
    ESP_LOGI(TAG, "driver v%s", BQ25619_DRIVER_VERSION);
    int64_t t0 = esp_timer_get_time();

    // Stage 35.2: add self to the i2c_master bus. Bus handle set up by
    // boot_hw_init's bringup_bus1() before this call. Reject if missing --
    // that would indicate a bringup-order regression.
    if (!g_i2c1_bus_handle) {
        ESP_LOGE(TAG, "init: g_i2c1_bus_handle NULL -- bringup_bus1 must run first");
        return ESP_ERR_INVALID_STATE;
    }
    i2c_device_config_t dev_cfg = {
        .dev_addr_length = I2C_ADDR_BIT_LEN_7,
        .device_address  = BQ25619_ADDR,
        .scl_speed_hz    = BOOT_I2C_FREQ_HZ,
    };
    esp_err_t add = i2c_master_bus_add_device(g_i2c1_bus_handle, &dev_cfg, &s_bq_dev);
    if (add != ESP_OK) {
        ESP_LOGE(TAG, "add_device failed: %s", esp_err_to_name(add));
        return add;
    }

    // Register bit positions used only in init (documented inline, so we don't
    // pollute the header with rarely-used masks):
    //   REG_IINDPM (0x00) bit 6 = TS_IGNORE  -- clearing keeps the JEITA
    //                    thermistor safety active (default) so the BQ pauses
    //                    charging outside the safe temperature window.
    //   REG_TIMER  (0x05) bits 5:4 = WATCHDOG (00 = disable) -- otherwise the
    //                    ~40 s charge watchdog trips and halts charging.
    //   REG_MISC   (0x07) bit 5 = BATFET_DIS -- previous ship-mode invocation
    //                    may have left this set; clear so charging can resume
    //                    even if the operator plugged USB back without a
    //                    full VBUS-removal cycle.
    const uint8_t IINDPM_TS_IGNORE  = (1 << 6);
    const uint8_t TIMER_WD_MASK     = (0x3 << 4);
    const uint8_t MISC_BATFET_DIS   = (1 << 5);

    if (xSemaphoreTake(g_i2c2_mutex, pdMS_TO_TICKS(300)) != pdTRUE) {
        ESP_LOGE(TAG, "I2C mutex timeout during init");
        return ESP_ERR_TIMEOUT;
    }

    uint8_t part = 0;
    esp_err_t ret = bq25619_read_reg(i2c_num, BQ25619_REG_PART, &part);
    if (ret != ESP_OK) goto out;

    // 1. TS_IGNORE -- cleared (default). TS pin thermistor is populated on
    //    Mk1b (5k1 + 33k||10k NTC) and the sealed enclosure means we can't
    //    tune JEITA now anyway; leaving TS active lets the BQ pause charging
    //    if the pack sees an out-of-window temperature. If bench charging
    //    stops mid-run, first suspect is JEITA vs this divider -- read the
    //    fault bits with `BQ` and re-set IGNORE here as a temporary
    //    workaround until the JEITA registers are tuned.
    uint8_t iindpm = 0;
    if (bq25619_read_reg(i2c_num, BQ25619_REG_IINDPM, &iindpm) == ESP_OK) {
        bq25619_write_reg(i2c_num, BQ25619_REG_IINDPM, iindpm & (uint8_t)~IINDPM_TS_IGNORE);
    }

    // 2. Disable charge watchdog. Without this, the BQ halts charging ~40 s
    //    after VBUS presence unless the host kicks the watchdog periodically.
    uint8_t timer = 0;
    if (bq25619_read_reg(i2c_num, BQ25619_REG_TIMER, &timer) == ESP_OK) {
        bq25619_write_reg(i2c_num, BQ25619_REG_TIMER, timer & (uint8_t)~TIMER_WD_MASK);
    }

    // 3. Clear BATFET_DIS if a prior session's ship-mode left it latched.
    //    Ship mode sets BATFET_DIS + BATFET_RST_WVBUS; the latter auto-
    //    re-enables BATFET on VBUS removal, but if the operator plugs USB
    //    without a full unplug cycle, the flag stays set and charging is
    //    blocked. Explicit clear at every boot side-steps this.
    uint8_t misc = 0;
    if (bq25619_read_reg(i2c_num, BQ25619_REG_MISC, &misc) == ESP_OK) {
        if (misc & MISC_BATFET_DIS) {
            bq25619_write_reg(i2c_num, BQ25619_REG_MISC, misc & (uint8_t)~MISC_BATFET_DIS);
            ESP_LOGW(TAG, "cleared latched BATFET_DIS (previous ship-mode -- charging restored)");
        }
    }

out:
    xSemaphoreGive(g_i2c2_mutex);

    if (ret != ESP_OK) {
        ESP_LOGE(TAG, "REG_PART read failed: %s", esp_err_to_name(ret));
        return ret;
    }

    int64_t t1 = esp_timer_get_time();
    ESP_LOGI(TAG, "%s init OK @ 0x%02X, REG_PART=0x%02X (WHO_AM_I bits [DSV]), boot=%lld us  [WD off, TS enabled, BATFET on]",
             bq25619_get_chip_name(), BQ25619_ADDR, part, (long long)(t1 - t0));
    return ESP_OK;
}

void bq25619_deinit(void)
{
    ESP_LOGI(TAG, "Deinit (no-op)");
}

// =============================================================================
// Boost + ship-mode
// =============================================================================

esp_err_t bq25619_set_boost(i2c_port_t i2c_num, bool enable)
{
    if (xSemaphoreTake(g_i2c2_mutex, pdMS_TO_TICKS(300)) != pdTRUE) {
        return ESP_ERR_TIMEOUT;
    }

    uint8_t poc = 0;
    esp_err_t ret = bq25619_read_reg(i2c_num, BQ25619_REG_POC, &poc);
    if (ret == ESP_OK) {
        if (enable) poc |=  BQ25619_POC_BOOST_EN;
        else        poc &= (uint8_t)~BQ25619_POC_BOOST_EN;
        ret = bq25619_write_reg(i2c_num, BQ25619_REG_POC, poc);
    }
    xSemaphoreGive(g_i2c2_mutex);

    if (ret == ESP_OK) {
        ESP_LOGI(TAG, "PMID boost %s", enable ? "ENABLED" : "DISABLED");
    } else {
        ESP_LOGE(TAG, "set_boost failed: %s", esp_err_to_name(ret));
    }
    return ret;
}

esp_err_t bq25619_enter_ship_mode(i2c_port_t i2c_num)
{
    ESP_LOGW(TAG, "Entering ship-mode (BATFET_DIS) -- battery disconnect imminent");

    // Ship-mode is king. If another task has the I2C mutex (drv2605 mid-buzz,
    // BQ polling loop, TMP117 read...) we WAIT rather than silently timing out
    // at the normal 300 ms budget. Escalating retry so a genuinely stuck mutex
    // eventually surfaces as an error log instead of hanging the watcher task.
    const TickType_t attempts[] = {
        pdMS_TO_TICKS(500),
        pdMS_TO_TICKS(1500),
        pdMS_TO_TICKS(3000),   // total worst case ~5 s -- longer than any
                               // in-flight I2C transaction on the bus.
    };
    bool got = false;
    for (size_t i = 0; i < sizeof(attempts) / sizeof(attempts[0]); i++) {
        if (xSemaphoreTake(g_i2c2_mutex, attempts[i]) == pdTRUE) {
            got = true;
            break;
        }
        ESP_LOGW(TAG, "ship-mode mutex busy, retrying (attempt %zu)", i + 1);
    }
    if (!got) {
        ESP_LOGE(TAG, "ship-mode ABORT: I2C mutex stuck after ~5 s. "
                      "Battery will NOT disconnect on next unplug.");
        return ESP_ERR_TIMEOUT;
    }

    // Match the Arduino reference (firmware/arduino/12_lsm_full/hw.ino:226-232):
    // OR  (BATFET_DIS | BATFET_RST_WVBUS)
    // AND ~(BATFET_DLY | BATFET_RST_EN)
    //
    // Stage 20 fix: previously only OR'd BATFET_DIS, leaving BATFET_DLY at
    // its default (delayed ~10 s). That was Ivan's "LONG_BUZZ fires at 4 s
    // then 9 s dead time" bench report. Clearing BATFET_DLY makes the
    // disconnect immediate.
    uint8_t misc = 0;
    esp_err_t ret = bq25619_read_reg(i2c_num, BQ25619_REG_MISC, &misc);
    if (ret == ESP_OK) {
        uint8_t misc_new = misc;
        misc_new |=  (uint8_t)(BQ25619_MISC_BATFET_DIS | BQ25619_MISC_BATFET_RST_WVBUS);
        misc_new &= (uint8_t)~(BQ25619_MISC_BATFET_DLY | BQ25619_MISC_BATFET_RST_EN);
        ESP_LOGW(TAG, "ship-mode REG_MISC 0x%02X -> 0x%02X", misc, misc_new);
        ret = bq25619_write_reg(i2c_num, BQ25619_REG_MISC, misc_new);
    }
    xSemaphoreGive(g_i2c2_mutex);

    if (ret != ESP_OK) {
        ESP_LOGE(TAG, "ship-mode write failed: %s", esp_err_to_name(ret));
    }
    // On battery: BATFET disconnects immediately (BATFET_DLY cleared).
    // On USB: BATFET stays gated by VBUS presence; RST_WVBUS re-enables it
    // on a full unplug/replug cycle so charging can resume next time.
    return ret;
}

// =============================================================================
// Polling task
// =============================================================================

void task_battery_fn(void *arg)
{
    (void)arg;
    const TickType_t period = pdMS_TO_TICKS(BATTERY_POLL_MS);
    TickType_t       last   = xTaskGetTickCount();

    ESP_LOGI(TAG, "Task started on Core %d", xPortGetCoreID());

    while (1) {
        if (!broker_battery_hw_alive()) {
            vTaskDelayUntil(&last, period);
            continue;
        }

        // Prophylactic against [[project_i2c_hw_fsm_reset_crash]] --
        // no reason to hammer I2C1 while the display is off; the
        // last-cached broker value stays visible when we wake.
        // Does NOT fix the legacy driver's fsm_reset bug (real fix
        // = i2c_master API migration), just reduces exposure.
        if (g_display_sleep) {
            ESP_LOGD(TAG, "poll skipped: display asleep");
            vTaskDelayUntil(&last, period);
            continue;
        }

        uint8_t  status = 0, fault = 0, poc = 0;
        uint16_t fuel_vcell_mv = 0;
        uint16_t fuel_pct100   = 0;

        if (xSemaphoreTake(g_i2c2_mutex, pdMS_TO_TICKS(300)) != pdTRUE) {
            ESP_LOGW(TAG, "I2C mutex timeout (poll)");
            vTaskDelayUntil(&last, period);
            continue;
        }
        bq25619_read_reg(I2C_NUM_1, BQ25619_REG_STATUS,   &status);
        bq25619_read_reg(I2C_NUM_1, BQ25619_REG_FAULT,    &fault);
        bq25619_read_reg(I2C_NUM_1, BQ25619_REG_POC,      &poc);
        // Vbat + SoC come from the MAX17048 fuel gauge on the same bus 2.
        // BQ25619's own REG_VBAT ADC is unusable on iv8.0 silicon
        // (see [[project_bq_no_vbat_adc]]).
        (void)max17048_read_vcell_mv  (I2C_NUM_1, &fuel_vcell_mv);
        (void)max17048_read_soc_pct100(I2C_NUM_1, &fuel_pct100);
        xSemaphoreGive(g_i2c2_mutex);

        uint8_t chrg = (status & BQ25619_STATUS_CHRG_MASK) >> BQ25619_STATUS_CHRG_SHIFT;
        bool    pg   = (status & BQ25619_STATUS_PG_GOOD) != 0;
        bool    is_charging = (chrg == BQ25619_CHRG_PRE_CHARGE) ||
                              (chrg == BQ25619_CHRG_FAST_CHARGE);

        broker_battery_data_t bd = {
            .voltage       = (float)fuel_vcell_mv / 1000.0f,
            .percentage    = (uint8_t)((fuel_pct100 + 50U) / 100U),  // round to nearest %
            .charging      = is_charging,
            .power_good    = pg,
            .charge_state  = chrg,
            .fault         = fault,
            .boost_enabled = (poc & BQ25619_POC_BOOST_EN) != 0,
        };
        broker_battery_write(&bd);

        vTaskDelayUntil(&last, period);
    }
}
