porupski/kompic-wearable/firmware/esp-idf/components/lsm6dsv16x/lsm6dsv16x.c

/**
 * @file lsm6dsv16x.c
 * @brief ST LSM6DSV16X driver -- Core 0 only.
 *
 * Replaces qmi8658.c at the chip layer. The complementary-filter logic in
 * task_imu_fn is the verbatim carry-forward from the QMI8658 implementation,
 * because the math is chip-independent.
 *
 * Scaling:
 *   Accel: ±4g full-scale, 0.122 mg/LSB -> 8192 LSB/g.
 *   Gyro:  ±2000 dps full-scale, 70 mdps/LSB -> ~14.29 LSB/dps.
 *   Temp:  256 LSB/°C with 25 °C offset.
 *
 * Read-before-write pattern (Blueprint 4 §3):
 *   Task reads broker before writing so the UI-owned `enabled` field is
 *   never clobbered. Same pattern as veml6030.c and haptic.c.
 */

#include "lsm6dsv16x.h"
#include "data_broker.h"
#include "ui_event.h"
#include "ui_subjects.h"    // Stage 32.1: g_imu_q for UI drain path
#include "boot_hw_init.h"   // g_i2c0_bus_handle (Stage 35.3)
#include "driver/i2c_master.h"
#include "esp_attr.h"
#include "esp_log.h"
#include "esp_timer.h"
#include "freertos/FreeRTOS.h"
#include "freertos/task.h"
#include "freertos/semphr.h"
#include <math.h>
#include <string.h>

extern SemaphoreHandle_t g_i2c_mutex;

static const char *TAG = "LSM6DSV16X";

// -- I2C device handle (Stage 35.3) -------------------------------------------
static i2c_master_dev_handle_t s_lsm_dev = NULL;
i2c_master_dev_handle_t lsm6dsv16x_get_dev_handle(void) { return s_lsm_dev; }

// ---------------------------------------------------------------------------
// Complementary filter state (Core 0 only)
// ---------------------------------------------------------------------------
#define CF_ALPHA   0.98f
#define CF_DT      (LSM6DSV16X_POLL_MS / 1000.0f)

static float s_roll_deg     = 0.0f;
static float s_pitch_deg    = 0.0f;
static bool  s_filter_seeded = false;

// ---------------------------------------------------------------------------
// Tap-Z monotonic counters (see lsm6dsv16x.h for consumer contract)
// ---------------------------------------------------------------------------
static volatile uint32_t s_tap_z_single_count = 0;
static volatile uint32_t s_tap_z_double_count = 0;

uint32_t lsm6dsv16x_tap_z_single_count(void) { return s_tap_z_single_count; }
uint32_t lsm6dsv16x_tap_z_double_count(void) { return s_tap_z_double_count; }

// ---------------------------------------------------------------------------
// INT1 ISR plumbing
// ---------------------------------------------------------------------------
static TaskHandle_t s_int1_task   = NULL;
static volatile bool s_isr_added  = false;

static void IRAM_ATTR lsm_int1_isr(void *arg)
{
    (void)arg;
    BaseType_t hpw = pdFALSE;
    if (s_int1_task) {
        vTaskNotifyGiveFromISR(s_int1_task, &hpw);
    }
    if (hpw) portYIELD_FROM_ISR();
}

// ---------------------------------------------------------------------------
// Identity
// ---------------------------------------------------------------------------
const char *lsm6dsv16x_get_chip_name(void) { return "LSM6DSV16X"; }
const char *lsm6dsv16x_get_chip_desc(void) { return "6-axis IMU + sensor fusion"; }

// ---------------------------------------------------------------------------
// I2C primitives (caller holds g_i2c_mutex)
// ---------------------------------------------------------------------------
static esp_err_t write_reg(i2c_port_t port, uint8_t reg, uint8_t val)
{
    (void)port;
    if (!s_lsm_dev) return ESP_ERR_INVALID_STATE;
    uint8_t buf[2] = { reg, val };
    return i2c_master_transmit(s_lsm_dev, buf, 2, 20);
}

static esp_err_t read_reg(i2c_port_t port, uint8_t reg, uint8_t *out)
{
    (void)port;
    if (!s_lsm_dev) return ESP_ERR_INVALID_STATE;
    return i2c_master_transmit_receive(s_lsm_dev, &reg, 1, out, 1, 20);
}

static esp_err_t read_regs(i2c_port_t port, uint8_t reg, uint8_t *buf, size_t len)
{
    (void)port;
    if (!s_lsm_dev) return ESP_ERR_INVALID_STATE;
    return i2c_master_transmit_receive(s_lsm_dev, &reg, 1, buf, len, 20);
}

// ---------------------------------------------------------------------------
// Init
// ---------------------------------------------------------------------------
esp_err_t lsm6dsv16x_init(i2c_port_t i2c_num)
{
    (void)i2c_num;
    ESP_LOGI(TAG, "driver v%s", LSM6DSV16X_DRIVER_VERSION);

    if (!g_i2c0_bus_handle) {
        ESP_LOGE(TAG, "init: g_i2c0_bus_handle NULL -- bringup_bus0 must run first");
        return ESP_ERR_INVALID_STATE;
    }
    i2c_device_config_t dev_cfg = {
        .dev_addr_length = I2C_ADDR_BIT_LEN_7,
        .device_address  = LSM6DSV16X_I2C_ADDR,
        .scl_speed_hz    = BOOT_I2C_FREQ_HZ,
    };
    esp_err_t add = i2c_master_bus_add_device(g_i2c0_bus_handle, &dev_cfg, &s_lsm_dev);
    if (add != ESP_OK) {
        ESP_LOGE(TAG, "add_device failed: %s", esp_err_to_name(add));
        return add;
    }

    if (xSemaphoreTake(g_i2c_mutex, pdMS_TO_TICKS(100)) != pdTRUE) {
        return ESP_ERR_TIMEOUT;
    }

    uint8_t chip_id = 0;
    esp_err_t ret = read_reg(i2c_num, REG_WHO_AM_I, &chip_id);
    if (ret != ESP_OK || chip_id != LSM6DSV16X_WHO_AM_I_VAL) {
        xSemaphoreGive(g_i2c_mutex);
        ESP_LOGE(TAG, "WHO_AM_I failed: got 0x%02X, expected 0x%02X",
                 chip_id, LSM6DSV16X_WHO_AM_I_VAL);
        return ESP_FAIL;
    }

    // Soft reset
    (void)write_reg(i2c_num, REG_CTRL3, CTRL3_SW_RESET);
    xSemaphoreGive(g_i2c_mutex);
    vTaskDelay(pdMS_TO_TICKS(20));

    if (xSemaphoreTake(g_i2c_mutex, pdMS_TO_TICKS(100)) != pdTRUE) {
        return ESP_ERR_TIMEOUT;
    }

    // BDU = 1 (block data update), IF_INC = 1 (auto-increment for burst reads)
    (void)write_reg(i2c_num, REG_CTRL3, CTRL3_BDU | CTRL3_IF_INC);

    // ─── Stage 11 Item C: correct DSV16X CTRL1/2/6/8 layout ────────────────────
    // Pre-Item-C the accel silently ran at OP_MODE_XL=LP3 + ODR_XL=7.5 Hz +
    // (likely) ±8g scale -- bench 2026-07-24 confirmed with MLC file rows
    // repeating every ~140 ms and az~19.5 m/s^2 at rest. See lsm6dsv16x.h
    // header comment for the datasheet layout.

    // Accel: High-Performance mode, 120 Hz ODR
    (void)write_reg(i2c_num, REG_CTRL1, CTRL1_OP_MODE_HP | CTRL1_ODR_XL_120HZ);

    // Gyro: High-Performance mode, 240 Hz ODR
    (void)write_reg(i2c_num, REG_CTRL2, CTRL2_OP_MODE_HP | CTRL2_ODR_G_240HZ);

    // Gyro full-scale: ±2000 dps (matches GYRO_LSB_PER_DPS=14.286)
    (void)write_reg(i2c_num, REG_CTRL6, CTRL6_FS_G_2000DPS);

    // Accel full-scale: ±4g (matches ACCEL_LSB_PER_G=8192)
    (void)write_reg(i2c_num, REG_CTRL8, CTRL8_FS_XL_4G);

    // INT1: enable DRDY_XL routing (useful for ISR-driven mode later).
    // For wake-on-motion, MD1_CFG bit 5 must also be set (done in install_int1_isr).
    (void)write_reg(i2c_num, REG_INT1_CTRL, 0x00);  // disabled by default; tile can enable

    xSemaphoreGive(g_i2c_mutex);
    vTaskDelay(pdMS_TO_TICKS(20));

    ESP_LOGI(TAG, "%s init OK @ 0x%02X (WHO_AM_I=0x%02X)",
             lsm6dsv16x_get_chip_name(), LSM6DSV16X_I2C_ADDR, chip_id);
    return ESP_OK;
}

// ---------------------------------------------------------------------------
// Read + scale
// ---------------------------------------------------------------------------
esp_err_t lsm6dsv16x_read(i2c_port_t i2c_num, broker_imu_data_t *out)
{
    if (!out) return ESP_ERR_INVALID_ARG;

    // 14 bytes from REG_OUT_TEMP_L (0x20):
    //   [0-1]   TEMP
    //   [2-7]   GYRO  X/Y/Z (low/high)
    //   [8-13]  ACCEL X/Y/Z (low/high)
    uint8_t raw[14];
    esp_err_t ret = read_regs(i2c_num, REG_OUT_TEMP_L, raw, sizeof(raw));
    if (ret != ESP_OK) return ret;

    int16_t t_raw  = (int16_t)((raw[1]  << 8) | raw[0]);
    int16_t gx_raw = (int16_t)((raw[3]  << 8) | raw[2]);
    int16_t gy_raw = (int16_t)((raw[5]  << 8) | raw[4]);
    int16_t gz_raw = (int16_t)((raw[7]  << 8) | raw[6]);
    int16_t ax_raw = (int16_t)((raw[9]  << 8) | raw[8]);
    int16_t ay_raw = (int16_t)((raw[11] << 8) | raw[10]);
    int16_t az_raw = (int16_t)((raw[13] << 8) | raw[12]);

    out->temperature = ((float)t_raw / TEMP_LSB_PER_C) + TEMP_OFFSET_C;
    out->accel_x     = ((float)ax_raw / ACCEL_LSB_PER_G) * GRAVITY_MS2;
    out->accel_y     = ((float)ay_raw / ACCEL_LSB_PER_G) * GRAVITY_MS2;
    out->accel_z     = ((float)az_raw / ACCEL_LSB_PER_G) * GRAVITY_MS2;
    out->gyro_x      = (float)gx_raw / GYRO_LSB_PER_DPS;
    out->gyro_y      = (float)gy_raw / GYRO_LSB_PER_DPS;
    out->gyro_z      = (float)gz_raw / GYRO_LSB_PER_DPS;
    return ESP_OK;
}

// ---------------------------------------------------------------------------
// INT1 (wake-on-motion) -- ISR install/uninstall
// ---------------------------------------------------------------------------
esp_err_t lsm6dsv16x_install_int1_isr(TaskHandle_t notify_task)
{
    if (notify_task == NULL) {
        if (s_isr_added) {
            gpio_isr_handler_remove(LSM6DSV16X_INT1_GPIO);
            s_isr_added = false;
        }
        s_int1_task = NULL;
        return ESP_OK;
    }

    gpio_config_t io = {
        .pin_bit_mask = 1ULL << LSM6DSV16X_INT1_GPIO,
        .mode         = GPIO_MODE_INPUT,
        .pull_up_en   = GPIO_PULLUP_DISABLE,
        .pull_down_en = GPIO_PULLDOWN_ENABLE,
        .intr_type    = GPIO_INTR_POSEDGE,   // [DSV] LSM6DSV16X INT idles LOW
    };
    esp_err_t ret = gpio_config(&io);
    if (ret != ESP_OK) return ret;

    esp_err_t svc = gpio_install_isr_service(ESP_INTR_FLAG_LEVEL1);
    if (svc != ESP_OK && svc != ESP_ERR_INVALID_STATE) return svc;

    s_int1_task = notify_task;
    ret = gpio_isr_handler_add(LSM6DSV16X_INT1_GPIO, lsm_int1_isr, NULL);
    if (ret != ESP_OK) {
        s_int1_task = NULL;
        return ret;
    }
    s_isr_added = true;
    ESP_LOGI(TAG, "INT1 ISR installed on GPIO%d (pos edge)", LSM6DSV16X_INT1_GPIO);
    return ESP_OK;
}

// ---------------------------------------------------------------------------
// Task (Blueprint 4 §3 -- read-before-write)
// ---------------------------------------------------------------------------
// -- Stage 18 §3.4 wrist-gesture state ---------------------------------------
// Low-pass-filtered chip-Z acceleration (in g). accel_z is the dominant signal
// for a wrist-worn device face-up / face-down and is already computed by
// lsm6dsv16x_read into broker_imu_data_t.accel_z (m/s^2). This filter runs at
// the 50 Hz task tick; alpha 0.2 -> ~200 ms time constant, quick enough for a
// wrist raise (typical ~300-500 ms motion) and slow enough to reject a single
// tap or wobble.
static float    s_az_lpf_g          = 0.0f;
static bool     s_az_lpf_seeded     = false;
static uint32_t s_gesture_changes   = 0;   // counter for GESTURE CLI dump
static uint32_t s_gesture_last_ms   = 0;   // ms uptime of last change

// Hysteresis bands (in g). Signs picked so the physical action of raising
// the wrist to look at the display maps to WRIST_RAISE. Bench polarity
// check 2026-08-27: screen-up-on-table on the iv7.1 prototype reads
// az_lpf ~ -0.9 g, screen-down reads +0.9 g -- so WRIST_RAISE triggers
// on the NEGATIVE Z. Mk1b's enclosure orientation may want these flipped
// again; retune with the GESTURE live log after first bring-up.
#define WRIST_RAISE_ON_G   (-0.55f)   // az_lpf <= this  -> raise
#define WRIST_DOWN_ON_G    (+0.35f)   // az_lpf >= this  -> down

static void gesture_update(float az_g)
{
    if (!s_az_lpf_seeded) {
        s_az_lpf_g      = az_g;
        s_az_lpf_seeded = true;
        return;
    }
    // Alpha 0.2 IIR LPF.
    s_az_lpf_g = 0.8f * s_az_lpf_g + 0.2f * az_g;

    uint8_t prev = g_imu_gesture;
    uint8_t next = prev;
    if (s_az_lpf_g <= WRIST_RAISE_ON_G) {
        next = (uint8_t)IMU_GESTURE_WRIST_RAISE;
    } else if (s_az_lpf_g >= WRIST_DOWN_ON_G) {
        next = (uint8_t)IMU_GESTURE_WRIST_DOWN;
    }
    if (next != prev) {
        g_imu_gesture     = next;
        s_gesture_changes++;
        s_gesture_last_ms = (uint32_t)(esp_timer_get_time() / 1000LL);
        // Stage 18 §7.6: live event log. Rate is naturally throttled by the
        // hysteresis bands + LPF -- a flip fires 1 line, not spam. Ivan
        // flips the board and watches the console; no CLI polling needed.
        static const char *NAMES[] = {"NONE", "WRIST_RAISE", "WRIST_DOWN", "SHAKE"};
        const char *pn = (prev < 4) ? NAMES[prev] : "?";
        const char *nn = (next < 4) ? NAMES[next] : "?";
        ESP_LOGI(TAG, "[GESTURE] %s -> %s  (az_lpf=%+.2f g)",
                 pn, nn, (double)s_az_lpf_g);
    }
}

// Public accessors used by fc_cli.c's GESTURE dump.
float    lsm6dsv16x_gesture_az_lpf_g(void)   { return s_az_lpf_g; }
uint32_t lsm6dsv16x_gesture_change_count(void){ return s_gesture_changes; }
uint32_t lsm6dsv16x_gesture_last_change_ms(void){ return s_gesture_last_ms; }

void task_imu_fn(void *arg)
{
    (void)arg;
    ESP_LOGI(TAG, "Task started on Core %d", xPortGetCoreID());

    // Stage 32.1: push at most one "disabled" snapshot per transition so
    // the UI tile flips to "Disabled" instantly without waiting for the
    // next enabled cycle. Producer-side edge-detect on enabled matches
    // the pattern max_m10s uses when the chip goes silent.
    bool s_prev_pushed_disabled = false;

    while (1) {
        vTaskDelay(pdMS_TO_TICKS(LSM6DSV16X_POLL_MS));

        if (!broker_imu_hw_alive())    continue;
        if (!broker_imu_get_enabled()) {
            if (!s_prev_pushed_disabled && g_imu_q) {
                broker_imu_data_t off = {0};
                broker_imu_read(&off);
                off.enabled = false;
                (void)xQueueOverwrite(g_imu_q, &off);
                s_prev_pushed_disabled = true;
            }
            continue;
        }
        s_prev_pushed_disabled = false;

        broker_imu_data_t bd = {0};
        broker_imu_read(&bd);

        if (xSemaphoreTake(g_i2c_mutex, pdMS_TO_TICKS(50)) != pdTRUE) continue;
        esp_err_t ret = lsm6dsv16x_read(I2C_NUM_0, &bd);
        xSemaphoreGive(g_i2c_mutex);

        if (ret != ESP_OK) {
            ESP_LOGW(TAG, "Read failed: %s", esp_err_to_name(ret));
            continue;
        }

        // Complementary filter -- carried forward verbatim from qmi8658.c.
        float acc_roll  = atan2f(bd.accel_y, bd.accel_z) * (180.0f / (float)M_PI);
        float acc_pitch = atan2f(-bd.accel_x,
                                 sqrtf(bd.accel_y * bd.accel_y + bd.accel_z * bd.accel_z))
                          * (180.0f / (float)M_PI);

        if (!s_filter_seeded) {
            s_roll_deg      = acc_roll;
            s_pitch_deg     = acc_pitch;
            s_filter_seeded = true;
        } else {
            s_roll_deg  = CF_ALPHA * (s_roll_deg  + bd.gyro_x * CF_DT)
                          + (1.0f - CF_ALPHA) * acc_roll;
            s_pitch_deg = CF_ALPHA * (s_pitch_deg + bd.gyro_y * CF_DT)
                          + (1.0f - CF_ALPHA) * acc_pitch;
        }

        bd.roll_deg  = s_roll_deg;
        bd.pitch_deg = s_pitch_deg;

        broker_imu_write(&bd);

        // Stage 32.1: publish to UI drain queue in addition to broker.
        // Overwrite semantics: producer never blocks; drain timer picks up
        // the freshest sample every 200 ms on the LVGL task.
        if (g_imu_q) {
            (void)xQueueOverwrite(g_imu_q, &bd);
        }

        // Stage 18 §3.4 wrist gesture: LPF chip-Z, publish to g_imu_gesture.
        // Consumers today: fc_cli GESTURE dump; future: rgb_policy wrist-off
        // gate + display wake on Mk1b.
        gesture_update(bd.accel_z / 9.81f);

        // ─── Advanced-feature polling (Blueprint 4 §3 read-before-write) ──────
        //   Runs every tick at the base 50 Hz poll rate. Tap-Z is polled every
        //   tick (chip clears TAP_SRC on read when LIR=0, so we can't miss an
        //   event by reading too often). Pedometer is polled once per second
        //   -- the on-chip counter accumulates, no need to slam I2C on it.

        // Tap -> UI event queue. Two independent fixes on top of the
        // Stage-10 all-axes accept:
        //  1. Accept any of the three enabled axes (wrist geometry means
        //     the "tap the case" gesture mostly lands on X, not Z).
        //  2. Edge-detect on the SINGLE/DOUBLE bits -- TAP_SRC latches
        //     for ~365 ms per real tap event with LIR=1, so a naive
        //     level-based count fires 15-20 times per tap at 20 ms poll
        //     (bench log 2026-07-23). We track prev-poll state and count
        //     only on 0->1 transitions. One real double-tap => cnt+=1.
        static uint8_t s_prev_flags = 0;
        if (broker_imu_hw_alive()) {
            uint8_t src = lsm6dsv16x_tap_poll_src();
            bool any_axis = (src & (TAP_SRC_X_TAP | TAP_SRC_Y_TAP | TAP_SRC_Z_TAP)) != 0;
            bool now_double  = any_axis && (src & TAP_SRC_DOUBLE_TAP);
            bool now_single  = any_axis && (src & TAP_SRC_SINGLE_TAP);
            bool prev_double = (s_prev_flags & TAP_SRC_DOUBLE_TAP) != 0;
            bool prev_single = (s_prev_flags & TAP_SRC_SINGLE_TAP) != 0;
            ui_event_t ev = { .payload = { .tap = { .src = src } } };
            if (now_double && !prev_double) {
                s_tap_z_double_count++;
                ev.type = UI_EVENT_TAP_Z_DOUBLE;
                (void)ui_event_send(&ev);
            } else if (now_single && !prev_single) {
                s_tap_z_single_count++;
                ev.type = UI_EVENT_TAP_Z_SINGLE;
                (void)ui_event_send(&ev);
            }
            // Remember only the SINGLE/DOUBLE bits (axis bits reset per tap).
            s_prev_flags = src & (TAP_SRC_DOUBLE_TAP | TAP_SRC_SINGLE_TAP);
        }

        // Pedometer -> broker_steps, once per second.
        static uint32_t s_next_pedo_ms = 0;
        uint32_t now_ms = (uint32_t)(esp_timer_get_time() / 1000ULL);
        if (broker_steps_hw_alive() && broker_steps_get_enabled() && now_ms >= s_next_pedo_ms) {
            s_next_pedo_ms = now_ms + 1000;
            uint32_t steps = 0;
            if (lsm6dsv16x_pedometer_read(&steps) == ESP_OK) {
                broker_steps_data_t sd = {0};
                broker_steps_read(&sd);
                sd.step_count = steps;
                sd.enabled    = true;
                broker_steps_write(&sd);
            }
        }
    }
}
