porupski/kompic-wearable/firmware/esp-idf/components/lsm6dsv16x/imu_tile.c

/**
 * @file imu_tile.c
 * @brief LSM6DSV16X IMU tile -- LVGL 9, Core 1 only.
 *
 * Stage 32.1 rewrite -- subject-bound, corner-safe. Every value label is
 * driven from ui_subjects; imu_tile_update() only owns LED colour +
 * subj_imu_status_str colour tinting. Power switch uses
 * lv_obj_bind_checked against subj_imu_enabled (two-way -- observer in
 * ui_subjects.c mirrors to broker).
 *
 * Layout (portrait 410x502, 60H/40V corner-safe pads per
 * project_display_corner_cutoff):
 *   Row 0 (y=40):  LED(16) + header + power switch
 *   y=100:         "Acquiring..." / "Online" / "Disabled" status
 *   y=140-200:     Accel XYZ (left) + Gyro XYZ (right)
 *   y=250:         Orientation header
 *   y=284:         Roll (left) + Pitch (right)
 *   y=-40 (bot):   Temperature
 */

#include "imu_tile.h"
#include "lsm6dsv16x.h"      // identity strings
#include "data_broker.h"
#include "ui_theme_colors.h"
#include "ui_subjects.h"     // subj_imu_*, subj_imu_enabled
#include "esp_log.h"

static const char *TAG = "IMU_TILE";

// ---------------------------------------------------------------------------
// Corner-safe layout constants (matches env_tile / gps_tile convention)
// ---------------------------------------------------------------------------
#define IMU_PAD_H_UI       60
#define IMU_PAD_H_TEXT     40
#define IMU_PAD_V_UI       40
#define IMU_STATUS_Y      100
#define IMU_COL_HDR_Y     140
#define IMU_ROW_Y0        170
#define IMU_ROW_STEP       32
#define IMU_ORIENT_HDR_Y  280
#define IMU_ORIENT_VAL_Y  314

// ---------------------------------------------------------------------------
// Static widget handles
// ---------------------------------------------------------------------------
static lv_obj_t *s_parent           = NULL;

static lv_obj_t *s_led_status       = NULL;
static lv_obj_t *s_lbl_header       = NULL;
static lv_obj_t *s_sw_power         = NULL;
static lv_obj_t *s_lbl_status       = NULL;

static lv_obj_t *s_lbl_accel_hdr    = NULL;
static lv_obj_t *s_lbl_gyro_hdr     = NULL;
static lv_obj_t *s_lbl_orient_hdr   = NULL;

static lv_obj_t *s_lbl_ax           = NULL;
static lv_obj_t *s_lbl_ay           = NULL;
static lv_obj_t *s_lbl_az           = NULL;
static lv_obj_t *s_lbl_gx           = NULL;
static lv_obj_t *s_lbl_gy           = NULL;
static lv_obj_t *s_lbl_gz           = NULL;
static lv_obj_t *s_lbl_roll         = NULL;
static lv_obj_t *s_lbl_pitch        = NULL;
static lv_obj_t *s_lbl_temp         = NULL;

// ---------------------------------------------------------------------------
// Helper: map sensor_status_t -> LED colour
// ---------------------------------------------------------------------------
static void update_led(sensor_status_t st)
{
    lv_color_t col;
    switch (st) {
        case SENSOR_ONLINE:    col = COL_STATUS_ONLINE;    break;
        case SENSOR_OFFLINE:   col = COL_STATUS_OFFLINE;   break;
        case SENSOR_ACQUIRING: col = COL_STATUS_ACQUIRING; break;
        case SENSOR_STALE:     col = COL_STATUS_STALE;     break;
        case SENSOR_DISABLED:
        default:               col = COL_STATUS_DISABLED;  break;
    }
    lv_led_set_color(s_led_status, col);
}
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
